hasseily/appletini-one/docs/FABRIC_TIMING_MARGIN_PLAN.md

# Fabric Timing Margin Plan

## Goal

Raise intrinsic fabric timing margin at 133.333 MHz. A timing candidate may
become the incremental reference only after it meets all of these gates:

- Two clean, full, non-incremental builds of the same Git commit pass in a row.
- Each build has setup WNS of at least `+0.300 ns` and setup TNS of `0`.
- Each build has nonnegative hold WNS and hold TNS of `0`.
- Each build has nonnegative pulse-width slack and no failing endpoints.
- Each build has no unconstrained internal endpoint, route error, bus-skew
  error, or XDC query that matched no object.
- The exact firmware made from the first passing checkpoint passes the full
  hardware test list.
- The checkpoint, bitstream, XSA, firmware, reports, commit, and tool version
  have saved hashes or IDs.

The `+0.300 ns` setup target gives useful build margin. Two runs with Vivado's
default seed show repeatability on one tool version and host. They do not prove
that all seeds or later Vivado releases will pass. Record both facts and rerun
the gate after a tool change.

## Confirmed Starting Point

The prior `+0.012 ns` result came from a full build. It did not use the known
good checkpoint. Its final timing was:

| Check | Result |
| --- | ---: |
| Setup WNS | `+0.012 ns` |
| Setup TNS | `0.000 ns` |
| Hold WNS | `+0.048 ns` |
| Hold TNS | `0.000 ns` |
| Pulse-width WNS | `+0.265 ns` |

The worst setup path starts at `ab_read_r.addr[11]` and ends in the Apple cycle
capture FIFO RAM. It has about `6.685 ns` of data delay, ten logic levels, and
about 79 percent route delay. The next two paths end at a Disk II
`drive_bit_offset` clock enable and have 15 logic levels. A fix to the capture
path can expose Disk II as the next limit, so each change needs a new top-path
review.

The prior resource report showed 10,223 slices, 30,465 LUTs, 20,153 registers,
74 block RAM tiles, and 1,001 control sets. Vivado reported a minimum of 994
control sets. This leaves little gain from a broad control-set rewrite unless a
later report shows a worse result.

Current synthesis maps both 4,096 by 16-bit SSI263 F2 copies and the 2,048 by
8-bit SmartPort C8 ROM into LUTs. The earlier assumption that the C8 ROM used
block RAM was wrong. The bus write arbiter has 12 clients; vTW is client 11.
Most clients already register their requests.

## Build Records and Promotion

Each build gets an immutable directory under:

```text
.timing_runs/<UTC>-<commit>-<full-or-incremental>/
```

The directory contains a manifest, the final checkpoint, bitstream, XSA, and
reports. `.timing_runs/builds.csv` stores one row per attempt.
`.timing_runs/paths.csv` stores the top ten setup paths, including full start
and end names, cell types, clocks, delay split, route share, logic levels, and
fanout. Failed attempts also get a manifest and CSV row.

The manifest records:

- Git commit and dirty state.
- Vivado version, device, speed grade, build mode, and reference checkpoint.
- Synthesis and implementation strategies and key directives.
- Timing, failing endpoints, route status, bus skew, and constraint warnings.
- Slice, LUT, register, block RAM, DSP, and control-set use.
- SHA-256 hashes for the checkpoint, bitstream, and XSA.

The build script keeps a named checkpoint and XSA in each build directory for
test firmware. It does not replace the known-good checkpoint. Promotion takes
two named build IDs. It checks that they are the two latest consecutive full
builds of one clean commit and that both pass every timing gate. It also checks
an immutable hardware record tied to the first checkpoint and tested firmware.

## Phase 0: Measure the Design

Status: complete for the initial baseline.

1. Add immutable build manifests, `builds.csv`, and `paths.csv` to the normal
   build script.
2. Record setup, hold, pulse width, failing endpoints, route and bus-skew
   status, missing XDC objects, resources, control sets, strategies, tool
   version, and hashes.
3. Add an optional diagnostic set:
   `report_design_analysis -congestion`, `report_high_fanout_nets`, and
   `report_qor_suggestions`. Always write timing, use, control-set, route,
   bus-skew, clock, method, and constraint reports.
4. Add a promotion script that enforces the two-build and hardware gates.
5. Add direct simulator tests at the Apple renderer and SDD capture FIFO
   boundaries before changing their timing.
6. Run a clean full build with diagnostics. Treat its reports as the campaign
   baseline and rank path classes by delay, route share, fanout, and count.

Run the baseline from a clean commit:

```powershell
$env:APPLETINI_FULL_BUILD = "1"
$env:APPLETINI_TIMING_DIAGNOSTICS = "1"
vivado -mode batch -source scripts/build_and_export_xsa.tcl
Remove-Item Env:APPLETINI_FULL_BUILD
Remove-Item Env:APPLETINI_TIMING_DIAGNOSTICS
```

Do not compare WNS alone. Compare the top path class, setup path count, hold,
route share, LUT levels, use, and control sets.

### Phase 0 Baseline Result

The clean full build `20260812T153728Z-7342c1a5-full` used commit
`7342c1a51dd9b1e8b29220e276b0094d885b3038` and Vivado 2025.2. It used no
incremental reference and no rescue pass. It produced:

| Check | Result |
| --- | ---: |
| Setup WNS / TNS | `+0.012 ns` / `0.000 ns` |
| Hold WNS / TNS | `+0.048 ns` / `0.000 ns` |
| Pulse-width WNS / TNS | `+0.265 ns` / `0.000 ns` |
| Worst bus-skew slack | `+5.496 ns` |
| Route errors | `0` |
| Unconstrained internal endpoints | `0` |
| Missing XDC objects | `0` |

The final design used 10,226 slices, 30,465 LUTs, 20,153 registers, 74 block
RAM tiles, six DSPs, and 1,001 control sets. The routed design had no congestion
window above Vivado level 5. Vivado gave no QoR suggestion because timing met.
This makes broad floorplanning and control-set work lower priority than the
measured path classes.

The top ten setup paths were:

| Rank | End block | Slack | Route share | Levels | Max fanout |
| ---: | --- | ---: | ---: | ---: | ---: |
| 1 | Apple capture FIFO RAM | `+0.012 ns` | 78.6% | 10 | 48 |
| 2-3 | Disk II `drive_bit_offset` enable | `+0.015 ns` | 72.8% | 15 | 81 |
| 4-5 | Apple capture FIFO RAM | `+0.050` to `+0.073 ns` | about 78% | 10 | 48-54 |
| 6 | Apple bus direction output | `+0.079 ns` | 44.7% | 5 | 11 |
| 7-9 | Apple cycle egress space logic | `+0.079 ns` | 57.9% | 13 | 8 |
| 10 | Disk II `drive_phase` enable | `+0.108 ns` | 74.0% | 14 | 81 |

The first five and tenth paths start at `ab_read_r.addr[11]`. The capture path
passes through slot-7 overlay qualification, pending-record selection, and the
FIFO input before it reaches block RAM. The Disk II path passes through slot-7,
boot-menu, vTW Disk II, and drive-state logic. The capture register stage should
remove three top-ten paths, but Disk II will then set WNS near `+0.015 ns` unless
placement changes. Review the Disk II path before assuming bus-snapshot copies
alone can add the remaining margin.

## Phase 1: Remove Route-Heavy Capture Paths

### 1. Register Capture Records

Add one record-assembly stage before each FIFO write path:

- Apple cycle renderer capture.
- SDD capture.

Register the complete source record and a valid bit at the capture event. Feed
the current collision, pending-event, loss, gap, storm, and jam rules from that
stage. Do not delay only `wr_en`; data and all event state must move together.

The tests must prove:

- Normal Apple writes keep address, data, and flags together.
- Frame events keep their order against Apple writes.
- I/O events that arrive first stay first.
- Pending collisions keep both events without duplication.
- A full FIFO sets the same sticky drop and overlay-loss state.
- Acknowledge and a new drop in one clock use set-wins behavior.
- C029, SHR mode, reset, and overlay flags stay on the same record.
- SDD records keep all address, data, and state bits.
- Storm and jam records keep the last intended record and count.
- Disable and reset clear the same state as before.

One extra 133 MHz cycle is about 7.5 ns. CPU1 drains these queues much later,
so this latency should not affect visible behavior. The full regression and
hardware tests still decide acceptance.

After this change, run a full build. Accept it only if the old capture path
class leaves the top paths and all counts remain exact. If Disk II becomes the
new limit, record that result before the next edit.

#### First Capture-Pipeline Build

Commit `e26205d08f3a2fdfcb7bc00d295d669a3f09c537` added the one-cycle
record stage to both capture FIFOs. The direct simulations proved consecutive
records, I/O-before-Apple order, pending-record handling, full-FIFO loss,
set-over-ack behavior, reset, SDD storm and jam trigger records, and exact
record data. The VidHD/SHR, Apple egress, SDD stream, and linear-overlay tests
also passed.

The clean full build `20260812T160459Z-e26205d0-full` produced:

| Check | Result |
| --- | ---: |
| Setup WNS / TNS | `+0.006 ns` / `0.000 ns` |
| Hold WNS / TNS | `+0.037 ns` / `0.000 ns` |
| Pulse-width WNS / TNS | `+0.265 ns` / `0.000 ns` |
| Worst bus-skew slack | `+5.904 ns` |
| Route errors | `0` |
| Unconstrained internal endpoints | `0` |
| Missing XDC objects | `0` |

No capture FIFO endpoint remained in the top ten. The change removed the
target path class, but it did not raise total margin. The new leading paths
were:

| Rank | End block | Slack | Route share | Levels |
| ---: | --- | ---: | ---: | ---: |
| 1 | vTW 65C02 `a_q[1]` to `p_q[1]` | `+0.006 ns` | 62.0% | 13 |
| 2 | Apple DMA `line_idx_q[2]` to PSRAM write data | `+0.037 ns` | 72.0% | 9 |
| 3-4 | Disk II `drive_phase` | `+0.044` to `+0.050 ns` | 77-79% | 11-12 |
| 5 | vTW Apple-bus direction output | `+0.057 ns` | 48.2% | 3 |
| 6-7, 9 | SmartPort output FIFO address | `+0.063` to `+0.101 ns` | about 76% | 12 |

The build used 10,072 slices, 30,541 LUTs, 20,282 registers, 74 block RAM
tiles, and 1,008 control sets. Against the baseline, slices fell by 154 while
LUTs rose by 76, registers rose by 129, and control sets rose by seven. The
build used the normal post-route `Explore` pass and no extra rescue pass.

Keep the capture stage because it removes the measured long decode-to-BRAM
path and its tests pass. Do not promote this build. Trace the new 65C02,
DMA/PSRAM, Disk II, and SmartPort paths before the next edit. A local vTW
Disk II enable register is a better first cut for the measured 11- to 12-level
Disk II cone than a broad fanout setting. Bus snapshot copies may still help
the SmartPort paths and the remaining common route delay, but fresh reports
must show the useful copy points.

#### vTW Disk II Gate Build

Commit `4a61407ff25d3e649a967ff854959f9f28383880` registered only the
boot-menu Disk II gate used by vTW. It kept the native handoff gate live. All
14 vTW benches, 19 standard Disk II tests, and 66 WOZ tests passed. The clean
full build `20260812T163431Z-4a61407f-full` produced:

| Check | Result |
| --- | ---: |
| Setup WNS / TNS | `+0.004 ns` / `0.000 ns` |
| Hold WNS / TNS | `+0.057 ns` / `0.000 ns` |
| Pulse-width WNS / TNS | `+0.265 ns` / `0.000 ns` |
| Worst bus-skew slack | `+5.366 ns` |
| Route errors | `0` |
| Missing XDC objects | `0` |

The long address-to-vTW Disk II path left the top ten. Local Disk II paths
now start at registered drive state and have at least `+0.100 ns` slack. Four
of the top ten paths start at `ab_read_r.addr[13]` and end in SmartPort or
Disk II; they have 46 to 74 loads and about 74 to 77 percent route delay. The
worst path is a Mockingboard response to the Apple data-direction pin at
`+0.004 ns`.

The design used 10,077 slices, 30,598 LUTs, 20,305 registers, 74 block RAM
tiles, and 1,053 control sets. Keep the local Disk II gate stage, but do not
promote this build. Test a synthesis `MAX_FANOUT` of 32 on the sampled 16-bit
Apple address register as one flow change. Do not apply it to the whole bus or
to the local capture record stage.

#### Apple Address `MAX_FANOUT` Build

Commit `3802754e1313f12d0a34a9e875a405ce103e2a02` set `MAX_FANOUT` to
32 on the 16 sampled Apple address registers. A post-synthesis cell check found
155 address-register cells instead of 16, so synthesis made 139 copies. It made
the most copies for the low address bits and only two cells for each of bits
11 through 15.

The clean full build `20260812T165450Z-3802754e-full` produced:

| Check | Result |
| --- | ---: |
| Setup WNS / TNS | `+0.004 ns` / `0.000 ns` |
| Hold WNS / TNS | `+0.014 ns` / `0.000 ns` |
| Pulse-width WNS / TNS | `+0.265 ns` / `0.000 ns` |
| Worst bus-skew slack | `+5.657 ns` |
| Route errors | `0` |
| Missing XDC objects | `0` |

Setup WNS did not change from the prior full build, while hold WNS fell from
`+0.057 ns` to `+0.014 ns`. The worst path still started at live
`ab_read_r.addr[11]` and ended in Disk II. Other address-to-Disk II and
address-to-SmartPort paths remained in the top ten. The build used 9,787
slices, 30,577 LUTs, 20,319 registers, 74 block RAM tiles, and 1,041 control
sets.

The broad limit did not make useful per-card groups and did not raise margin.
Commit `f75dc4d` removed it. Do not use a broad `MAX_FANOUT` rule on these
registers. If a later path calls for copies, make explicit same-cycle source
copies for named consumer groups, preserve the Apple bus sample edge, and
measure that change on its own.

#### Physical Response Stage Build

Commit `fbddd81997ee8c0c537ce64c6929aa006f886051` registered the
physical data-response tuple after the 12-client arbiter. Data, normal data
enable, address ownership, R/W, and the INH dependency move together. Address,
R/W, control-line requests, and the early DMA-window control remain live. The
staged byte also feeds the DMA window because both DMA clients hold it well
before that window opens.

The stage keeps the raw PHI0 release at the placed output LUT. It also stores
the INH dependency with an II+ saved read, so closing the machine-mode
interlock releases both INH and the live or held byte. The focused tests proved
late and back-to-back card responses, native and vTW-owned reads and writes,
II+ saved-byte hold, live and saved INH cutoff, reset masking, and the existing
AD8088 DMA window. The AD8088 bench still measured `158.8` to `323.8 ns`, with
zero ghost writes.

The clean full build `20260813T045644Z-fbddd819-full` produced:

| Check | Result |
| --- | ---: |
| Setup WNS / TNS | `+0.003 ns` / `0.000 ns` |
| Hold WNS / TNS | `+0.045 ns` / `0.000 ns` |
| Pulse-width WNS / TNS | `+0.265 ns` / `0.000 ns` |
| Worst bus-skew slack | `+5.376 ns` |
| Route errors | `0` |
| Missing XDC objects | `0` |

The card-to-data-direction path left the top paths. Against the prior accepted
netlist, slices fell from 10,077 to 9,752, LUTs fell from 30,598 to 30,558,
and control sets fell from 1,053 to 1,008. Registers rose from 20,305 to
20,314. Keep the stage for the removed output path and lower use, but do not
promote this build. Setup margin stayed flat because Disk II replaced the
removed path:

| Rank | Path class | Slack | Route share | Levels |
| ---: | --- | ---: | ---: | ---: |
| 1-4 | Apple address to Disk II bit-offset enable | `+0.003 ns` | 79.8% | 10 |
| 5 | PS to Disk II underrun count | `+0.010 ns` | 77.5% | 5 |
| 6-9 | Disk II spin count to latch enable | `+0.014 ns` | 75.3% | 13 |
| 10 | Disk II spin count to step-delay enable | `+0.034 ns` | 77.2% | 12 |

Trace and cut these two Disk II enable classes before adding bus snapshot
copies. The new report does not support a broad address-copy change.

#### Disk II vTW Rotation Stage Build

Commit `03de4daec1d2d03a1c566bdffe669365ec97d0f1` registered the
Disk II rotation state only at the boundary into vTW speed control. Local Q7,
cache-miss, media-ready, and sequencer logic remain live. Motor and drive
changes come through physical Disk II cycles, so the new view settles well
before vTW can start another private cycle.

All 14 vTW benches, 19 standard Disk II tests, and 66 WOZ tests passed. The
boot-menu source checks passed 19 of 20 tests; the one failed source-order guard
is unrelated to this RTL change and existed before it.

The clean full build `20260813T052716Z-03de4dae-full` produced:

| Check | Result |
| --- | ---: |
| Setup WNS / TNS | `+0.093 ns` / `0.000 ns` |
| Hold WNS / TNS | `+0.047 ns` / `0.000 ns` |
| Pulse-width WNS / TNS | `+0.265 ns` / `0.000 ns` |
| Worst bus-skew slack | `+5.921 ns` |
| Route errors | `0` |
| Missing XDC objects | `0` |
| Rescue used | `0` |

The spin-count-to-vTW-to-Disk II feedback paths left the top ten. The prior
Apple-address-to-Disk II paths also stayed out of the top ten in this placement.
The build used 9,916 slices, 30,540 LUTs, 20,285 registers, 74 block RAM tiles,
and 1,007 control sets. Against the response-stage build, LUTs fell by 18,
registers fell by 29, control sets fell by one, and slices rose by 164.

The new top paths are:

| Rank | Path class | Slack | Route share | Levels |
| ---: | --- | ---: | ---: | ---: |
| 1 | Raw PHI0 input to data-direction output | `+0.093 ns` | 39.7% | 3 |
| 2-4 | vTW cycle address to record enable | `+0.112 ns` | 71.9% | 10 |
| 5 | vTW cycle address to record enable | `+0.135 ns` | 72.0% | 10 |
| 6-10 | Slot mapping to Disk II dirty-track enable | `+0.163 ns` | 76.9% | 11 |

Keep the rotation stage, but do not promote this build. The setup gain is
`0.090 ns`, and the target remains `+0.300 ns`. Review the fixed PHI0 release
route, then cut the vTW record-control and Disk II mapping cones. Do not add a
broad fanout rule: none of these paths starts at a high-load source.

#### Data-Direction Pad Build

Commit `d9cb0beefc688798046bfe52a6ae8dba0b4e8016` kept the existing
12 mA drive on `a2fpga_dir_d` and changed only its output slew from slow to
fast. This keeps the raw-PHI0 truth table and clock count unchanged. A routed
checkpoint test predicted `+0.624 ns` on the eight-nanosecond pad-to-pad bound.
All 14 vTW benches passed before the full build.

The clean full build `20260813T055125Z-d9cb0bee-full` produced:

| Check | Result |
| --- | ---: |
| Setup WNS / TNS | `+0.036 ns` / `0.000 ns` |
| Hold WNS / TNS | `+0.066 ns` / `0.000 ns` |
| Pulse-width WNS / TNS | `+0.265 ns` / `0.000 ns` |
| Worst bus-skew slack | `+5.388 ns` |
| Route errors | `0` |
| Missing XDC objects | `0` |
| Rescue used | `0` |

The target path improved from `+0.093` to `+0.476 ns`, even though its route
delay rose from `3.136` to `3.284 ns`. The output-buffer delay fell by about
`0.53 ns`. Keep this constraint because the raw-PHI0 release path now clears
the campaign target without changing its logic. Hardware signoff must still
check the faster control edge for ringing.

Global WNS fell due to placement of a different path. The new top paths are:

| Rank | Path class | Slack | Route share | Levels |
| ---: | --- | ---: | ---: | ---: |
| 1-2, 4-5, 10 | Slot state to SmartPort output-FIFO address | `+0.036` to `+0.207 ns` | 74-76% | 12-13 |
| 3 | Disk II track length to data latch | `+0.161 ns` | 75.9% | 13 |
| 6-9 | vTW cycle address to RamWorks data enable | `+0.205 ns` | 69.1% | 10 |

The build used 10,013 slices, 30,542 LUTs, 20,267 registers, 74 block RAM
tiles, and 1,008 control sets. Do not promote it. Cut the SmartPort FIFO
address path next, then the measured vTW and Disk II paths.

#### SmartPort FIFO Address Build

Commit `12dc4977418f0cc3e4e35812c63ebf772b6a716e` removed the same-edge
post-pop lookahead from the SmartPort output FIFO. The block RAM now reads
from the registered pointer. The word catches up one fabric clock after a
pop, before either the native Apple bus or vTW can issue its next DATA read.
The test bench covers a five-byte word crossing through both paths. All 14
vTW benches, 16 SmartPort service tests, six ROM tests, and 15 menu tests
passed before the full build.

The clean full build `20260813T061638Z-12dc4977-full` produced:

| Check | Result |
| --- | ---: |
| Setup WNS / TNS | `+0.017 ns` / `0.000 ns` |
| Hold WNS / TNS | `+0.030 ns` / `0.000 ns` |
| Pulse-width WNS / TNS | `+0.265 ns` / `0.000 ns` |
| Worst bus-skew slack | `+5.915 ns` |
| Route errors | `0` |
| Missing XDC objects | `0` |
| Rescue used | `0` |

The target SmartPort block-RAM address path left the top ten. Keep the cut.
The lower global WNS comes from a different machine-mode-to-data-direction
route under the ten-nanosecond output bound. The new top paths are:

| Rank | Path class | Slack | Route share | Levels |
| ---: | --- | ---: | ---: | ---: |
| 1 | Machine mode to data-direction output | `+0.017 ns` | 55.5% | 3 |
| 2-5 | Disk II quarter-track to bit-offset enable | `+0.124 ns` | 75.3% | 13 |
| 6-7 | Apple address to Disk II WOZ shift enable | `+0.137 ns` | 77.9% | 11 |
| 8-10 | Disk II quarter-track to stream-position enable | `+0.159` to `+0.165 ns` | 75.2% | 13 |

The build used 9,909 slices, 30,567 LUTs, 20,289 registers, 74 block RAM
tiles, and 1,018 control sets. Do not promote it. First remove the live
machine-mode decode from the direction-output cone. Then cut the measured
Disk II rotation and native-event cones.

#### Bus Safety Interlock Copy Build

Commit `c647de77861ad7cadaf797d77da7be7e61db13ee` added a preserved,
same-edge copy of the machine INH safety flag for `apple_bus_wrapper`. The
copy keeps reset and machine-mode update behavior unchanged. All 14 vTW
benches passed before the full build.

The clean full build `20260813T063714Z-c647de77-full` used Vivado 2025.2,
no incremental reference, and no rescue pass. It produced:

| Check | Result |
| --- | ---: |
| Setup WNS / TNS | `+0.116 ns` / `0.000 ns` |
| Hold WNS / TNS | `+0.075 ns` / `0.000 ns` |
| Pulse-width WNS / TNS | `+0.265 ns` / `0.000 ns` |
| Worst bus-skew slack | `+5.928 ns` |
| Route errors | `0` |
| Missing XDC objects | `0` |
| Unconstrained internal endpoints | `0` |
| Rescue used | `0` |

The build used 9,826 slices, 30,541 LUTs, 20,296 registers, 74 block RAM
tiles, six DSPs, and 1,009 control sets. The new top paths are:

| Rank | Path class | Slack | Route share | Levels |
| ---: | --- | ---: | ---: | ---: |
| 1-7 | vTW CPU state to private RamWorks-bank enable | `+0.116 ns` | 80.8% | 7 |
| 8 | vTW cycle address to card-control read data | `+0.140 ns` | 68.8% | 14 |
| 9 | Apple address to SmartPort input count | `+0.155 ns` | 67.6% | 14 |
| 10 | Disk II quarter-track to bit-offset enable | `+0.159 ns` | 74.4% | 13 |

The first path class starts at a CPU state bit with fanout 93 and ends at all
seven `ss_ramworks_bank` clock enables. Cut this measured class next by using
a private soft-switch apply pulse after the captured vTW cycle tuple is ready.

The copy improved placement, but it did not remove every old
machine-mode-to-data-direction route. The new local-copy path to `DIR_D` has
`+0.445 ns` slack, while the original machine-mode path through the write
arbiter remains at `+0.359 ns`. Neither path limits this build. Keep the copy,
but do not claim that it removed the old route. Do not promote this build;
setup margin remains below `+0.300 ns`.

#### vTW Soft-Switch Apply Build

Commit `bceefabda0ba6449a5fa5a42009c41f13abba786` moved only the
private vTW soft-switch manager to a one-clock apply stage. `X_CAPTURE` saves
the core address, read/write state, write data, and pre-access switch state.
`X_ROUTE` applies that saved tuple to the private manager. The shared
`ssm_pulse` and the `$C074` speed latch remain at `X_CAPTURE`.

The full-system test now checks both `$C071` and `$C073`: the RamWorks bank
stays old at `X_CAPTURE`, changes at `X_ROUTE`, and appears in the next access
snapshot. Its existing checks also kept `$C006/$C007`, the C3/CFFF claim and
release, double `$C083`, video switches, and `$C074` behavior intact. All 14
vTW benches passed. The RamWorks 8 MB contract test, capture-FIFO, cycle-egress,
SDD stream, linear-overlay, and VidHD/SHR regressions also passed.

The clean full build `20260813T071806Z-bceefabd-full` used Vivado 2025.2,
no incremental reference, and no rescue pass. It produced:

| Check | Result |
| --- | ---: |
| Setup WNS / TNS | `+0.009 ns` / `0.000 ns` |
| Hold WNS / TNS | `+0.041 ns` / `0.000 ns` |
| Pulse-width WNS / TNS | `+0.265 ns` / `0.000 ns` |
| Worst bus-skew slack | `+5.911 ns` |
| Route errors | `0` |
| Missing XDC objects | `0` |
| Unconstrained internal endpoints | `0` |
| Rescue used | `0` |

The build used 9,855 slices, 30,501 LUTs, 20,263 registers, 74 block RAM
tiles, six DSPs, and 1,008 control sets. Against the bus-safety-copy build,
slices rose by 29, LUTs fell by 40, registers fell by 33, and control sets
fell by one.

The CPU-state-to-`ss_ramworks_bank` enable paths left the top ten, so keep
this structural cut. Global WNS fell by `0.107 ns` because Disk II and live
Apple-address paths took over:

| Rank | Path class | Slack | Route share | Levels |
| ---: | --- | ---: | ---: | ---: |
| 1, 7-10 | Disk II quarter-track to WOZ-shift enable | `+0.009`, then `+0.075 ns` | 76.1-76.2% | 12 |
| 2 | Apple address to Disk II bit-offset data | `+0.017 ns` | 76.7% | 12 |
| 3, 5 | Disk II quarter-track to data-latch enable | `+0.038`, `+0.069 ns` | 76.3-76.5% | 12 |
| 4 | Apple address to SmartPort input-FIFO write enable | `+0.066 ns` | 74.9% | 12 |
| 6 | vTW cycle address to posted-write memory input | `+0.074 ns` | 76.4% | 10 |

Do not promote this build. It passes the nonnegative export gates but remains
well below `+0.300 ns`. Trace the Disk II quarter-track enable cone and the
live Apple-address consumer cone before choosing the next cut. Do not infer a
new change from WNS alone; both classes are route-heavy and need path-level
control-flow review.

#### vTW Disk II Time-Tick Stage Build

Commit `bd99547fb82abcf90b5c4adbf7928926b536be46` stages only the
accepted normal vTW Disk II time tick by one 133.333 MHz fabric clock. The
stage clears when the core session ends. Private Disk II reads keep their
registered direct-access tick, while native and Q7 cycles keep the physical
1 MHz tick path.

All 14 vTW benches passed. The focused checks prove exact accepted and output
pulse counts across a readiness stall, let an accepted tick drain after a
later stall, clear a pending tick on session reset, and keep private, native,
and Q7 tick selection separate. All 19 standard Disk II tests, 66 WOZ tests,
the capture-FIFO and cycle-egress tests, nine SDD tests, the linear-overlay
source and RTL tests, and 17 VidHD/SHR tests also passed.

The clean full diagnostic run `20260813T082040Z-bd99547f-full` used Vivado
2025.2, the default seed, and no incremental reference. Its normal
post-route `Explore` result had `-0.030 ns` setup WNS. The extra
`AggressiveExplore` rescue pass did not improve it, so `rescue_used=1`. The
run failed its setup gate and exported no candidate DCP, bitstream, or XSA.

| Check | Result |
| --- | ---: |
| Build status | `failed` |
| Setup WNS / TNS | `-0.030 ns` / `-0.030 ns` |
| Setup failing endpoints | `1` |
| Hold WNS / TNS | `+0.039 ns` / `0.000 ns` |
| Pulse-width WNS / TNS | `+0.265 ns` / `0.000 ns` |
| Worst bus-skew slack | `+5.994 ns` |
| Route errors | `0` |
| Missing XDC objects | `0` |
| Unconstrained internal endpoints | `0` |
| Rescue used | `1` |
| Hardware export | refused |

The run used 9,725 slices, 30,398 LUTs, 20,289 registers, 74 block RAM
tiles, six DSPs, and 1,008 control sets. Against the soft-switch apply build,
slices fell by 130, LUTs fell by 103, registers rose by 26, and control sets
stayed unchanged. Setup WNS fell by `0.039 ns`, hold WNS fell by `0.002 ns`,
and bus-skew slack rose by `0.083 ns`.

The old Disk II quarter-track/readiness/normal-tick paths to the WOZ shift and
data-latch enables left the top ten. The existing vTW posted-write class took
over instead:

| Rank | Path class | Slack | Route share | Levels |
| ---: | --- | ---: | ---: | ---: |
| 1, 5-7, 9 | vTW cycle address to posted-write BRAM enable/data | `-0.030`, then `+0.059` to `+0.123 ns` | 76.3-76.6% | 10 |
| 2 | vTW write-direction state to address-direction output | `+0.003 ns` | 48.4% | 2 |
| 3 | Machine-INH safety copy to data-direction output | `+0.004 ns` | 53.5% | 3 |
| 4, 8 | vTW cycle address to posted-fill state | `+0.040`, `+0.119 ns` | 66.7-67.4% | 13 |
| 10 | Disk II request address to recalibration-sound arm state | `+0.133 ns` | 80.2% | 8 |

Keep the time-tick stage because it cut the measured same-cycle feedback and
passed its functional checks. Do not claim that it removed every Disk II
quarter-track consumer. Do not promote this run: it has one failing setup
endpoint, used the rescue pass, and produced no hardware outputs. Trace the
cycle-address-to-posted-write BRAM enable cone before choosing another cut.

#### vTW Posted-Write Tuple Stage Build

Commit `72903dd21744a04e6f493c650492b66c3b66c4c3` adds one registered
address/data/valid tuple between final core-or-ARM acceptance and the vTW bus
engine's posted queue. The core keeps priority on an exact collision. The
stage can drain and refill on the same edge, so it keeps one write per fabric
clock. It adds one 133.333 MHz clock, about 7.5 ns, before queue entry. Reset,
disable, or Apple `RES#` cancels the pending tuple at the same transaction
boundary that clears the queue.

All 14 vTW benches passed. Away from a queue-clear boundary, the full-system
test now proves that each accepted core or ARM tuple reaches the engine on the
next edge with the same address and data. It also checks a sustained
eight-write ARM burst, exact core-over-ARM collision order, overlay-write order
before slot-7 `DEVSEL`, and reset cancellation of an accepted tuple. The
capture-FIFO, cycle-egress, nine SDD, linear-overlay source and RTL, 17
VidHD/SHR, and 16 SmartPort service tests also passed.

The clean full build `20260813T090405Z-72903dd2-full` used Vivado 2025.2, the
default seed, no incremental reference, and no rescue pass. It exported the
candidate DCP, bitstream, and XSA.

| Check | Result |
| --- | ---: |
| Build status | `exported` |
| Setup WNS / TNS | `+0.121 ns` / `0.000 ns` |
| Setup failing endpoints | `0` |
| Hold WNS / TNS | `+0.058 ns` / `0.000 ns` |
| Pulse-width WNS / TNS | `+0.265 ns` / `0.000 ns` |
| Worst bus-skew slack | `+5.816 ns` |
| Route errors | `0` |
| Missing XDC objects | `0` |
| Unconstrained internal endpoints | `0` |
| Rescue used | `0` |

The build used 10,014 slices, 30,533 LUTs, 20,273 registers, 74 block RAM
tiles, six DSPs, and 1,009 control sets. Against the Disk II time-tick run,
slices rose by 289, LUTs rose by 135, registers fell by 16, and control sets
rose by one. Setup WNS rose by `0.151 ns`, hold WNS rose by `0.019 ns`, and
bus-skew slack fell by `0.178 ns`.

The prior vTW posted-memory and posted-fill paths left the saved top ten, so
keep this cut. Live Apple-address consumers took over:

| Rank | Path class | Slack | Route share | Levels |
| ---: | --- | ---: | ---: | ---: |
| 1 | Apple address to Disk II recalibration-sound arm state | `+0.121 ns` | 73.6% | 12 |
| 2, 3, 5 | Apple address to SmartPort input-FIFO write enable | `+0.206` to `+0.255 ns` | 73.0-73.2% | 13 |
| 4, 10 | Apple address to Disk II bit-offset enable | `+0.222`, `+0.283 ns` | 75.5-75.7% | 12 |
| 6, 8 | PS AXI interface to egress and Ethernet config state | `+0.259`, `+0.278 ns` | 83.7-83.9% | 0 |
| 7 | Apple reset snapshot to control read data | `+0.264 ns` | 76.5% | 10 |
| 9 | Slot-enable mask to no-slot-clock reset | `+0.280 ns` | 80.5% | 7 |

Do not promote or package this build. Setup margin is still `0.179 ns` below
the `+0.300 ns` gate. For the next measured cut, split the native Disk II raw
read-response path from its controller side effects, then register the native
`$C0Ex` read/write pulse and low address for the stepper and bit-offset
updates. Capture write data at its current data phase. Keep the same-cycle
Apple read response and private vTW request order intact. This targets ranks
1, 4, and 10; remeasure before changing the SmartPort path.

#### Disk II Handoff Gate Build

Commit `e360dec24b71b16c96f2c3ffbb1f21e51d9cba4a` puts normal native
Disk II I/O, the physical timing strobe, and vTW activation behind the existing
one-fabric-clock registered handoff view. The first `$C600` handoff read keeps
a live one-clock bypass that ends in the slot-ROM response. The slot-6 enable
remains a live term in both gates. This avoids the unsafe plan to delay Disk II
controller side effects while keeping the first handoff ROM byte on its old
response schedule.

All 18 vTW benches passed, including the native physical-bus, native/vTW WOZ
read/write, all-speed vTW, and full vTW-to-WOZ tests. A directed RTL check
proves that the live bypass serves `$C600` but cannot turn `$C0EC` into a
controller event. All 21 boot-menu/reset, 19 standard Disk II, 66 WOZ, 16
SmartPort service, six SmartPort ROM, nine SDD, 17 VidHD/SHR, 12 Phasor,
Uthernet, SSC, cycle-egress, capture-FIFO, and linear-overlay checks also
passed. Hardware tests remain deferred.

The clean full build `20260813T112209Z-e360dec2-full` used Vivado 2025.2, the
default seed, no incremental reference, and no rescue pass. It exported the
candidate DCP, bitstream, and XSA.

| Check | Result |
| --- | ---: |
| Build status | `exported` |
| Setup WNS / TNS | `+0.053 ns` / `0.000 ns` |
| Setup failing endpoints | `0` |
| Hold WNS / TNS | `+0.049 ns` / `0.000 ns` |
| Pulse-width WNS / TNS | `+0.265 ns` / `0.000 ns` |
| Worst bus-skew slack | `+5.980 ns` |
| Route errors | `0` |
| Missing XDC objects | `0` |
| Unconstrained internal endpoints | `0` |
| Rescue used | `0` |

The build used 9,899 slices, 30,661 LUTs, 20,374 registers, 74 block RAM
tiles, six DSPs, and 1,025 control sets. Against the posted-write build, slices
fell by 115, LUTs rose by 128, registers rose by 101, and control sets rose by
16. Setup WNS fell by `0.068 ns`, hold WNS fell by `0.009 ns`, and bus-skew
slack rose by `0.164 ns`.

The old handoff-qualified Disk II paths left the saved top ten. A targeted
checkpoint query still finds Apple-address paths into the named Disk II
bit-offset and recalibration endpoint group, but their worst slack is now
`+0.362 ns` with seven logic levels instead of the prior `+0.121 ns` with 12
levels. The worst Apple-address path into the SmartPort input-FIFO BRAM write
enable is `+0.328 ns`; it also left the saved top ten but was not removed.

| Rank | Path class | Slack | Route share | Levels |
| ---: | --- | ---: | ---: | ---: |
| 1 | vTW write-direction state to the address-direction pad | `+0.053 ns` | 48.8% | 2 |
| 2, 8, 10 | Slot-C3-ROM state to SmartPort input count | `+0.092` to `+0.171 ns` | 64.3-65.0% | 16 |
| 3-6 | PS AXI interface to boot-menu key-FIFO enable | `+0.113 ns` | 73.9% | 6 |
| 7 | SSI263 formant accumulator to filter history | `+0.144 ns` | 44.6% | 20 |
| 9 | PS AXI interface to Phasor audio output | `+0.170 ns` | 84.2% | 0 |

Keep the handoff cut, but do not promote or package this build. Its setup
margin is still `0.247 ns` below the `+0.300 ns` gate, and no hardware check
has run. Trace the address-direction pad path and the slot-C3-ROM-to-SmartPort
count cone before choosing the next measured cut. Do not spend the next commit
on the old SmartPort BRAM-write path alone; its measured residual is already
above the promotion gate.

#### Address-Direction Fast-Edge Build

Commit `78b839a65f7893f9d0a0d51806f051da582c339e` kept the existing 12 mA
drive on `a2fpga_dir_a` and changed only its output slew from slow to fast.
The 18 vTW benches and the Appli-Card/AD8088 source checks passed. A query on
the prior routed checkpoint predicted that the output-buffer delay would fall
by `0.531 ns`, moving the target path from `+0.053 ns` to `+0.584 ns` without
changing logic or clock count.

The clean full build `20260813T114539Z-78b839a6-full` used Vivado 2025.2,
the default seed, no incremental reference, and no rescue pass. It exported
the candidate DCP, bitstream, and XSA.

| Check | Result |
| --- | ---: |
| Build status | `exported` |
| Setup WNS / TNS | `+0.015 ns` / `0.000 ns` |
| Setup failing endpoints | `0` |
| Hold WNS / TNS | `+0.044 ns` / `0.000 ns` |
| Pulse-width WNS / TNS | `+0.265 ns` / `0.000 ns` |
| Worst bus-skew slack | `+5.748 ns` |
| Route errors | `0` |
| Missing XDC objects | `0` |
| Unconstrained internal endpoints | `0` |
| Rescue used | `0` |

The build used 10,038 slices, 30,646 LUTs, 20,315 registers, 74 block RAM
tiles, six DSPs, and 1,007 control sets. Against the handoff-gate build,
slices rose by 139, LUTs fell by 15, registers fell by 59, and control sets
fell by 18. Setup WNS fell by `0.038 ns`, hold WNS fell by `0.005 ns`, and
bus-skew slack fell by `0.232 ns`.

The fast pad did reduce logic and output-buffer delay from `3.799 ns` to
`3.214 ns`. The route delay rose from `3.625 ns` to `4.244 ns`, however, so
the same address-direction endpoint remained worst and fell from `+0.053 ns`
to `+0.015 ns`. The target did not improve in a clean implementation.

| Rank | Path class | Slack | Route share | Levels |
| ---: | --- | ---: | ---: | ---: |
| 1 | vTW write-direction state to the address-direction pad | `+0.015 ns` | 56.9% | 2 |
| 2, 4, 8 | Apple address to SmartPort input-FIFO write enable | `+0.110` to `+0.159 ns` | 72.2-72.4% | 13 |
| 3 | Apple address to SmartPort input count | `+0.112 ns` | 63.3% | 16 |
| 5-7 | Disk II WOZ accumulator to data-latch enable | `+0.148 ns` | 60.2% | 10 |
| 9 | Apple address to SmartPort output count | `+0.163 ns` | 62.8% | 16 |
| 10 | vTW cycle address to aux-shadow BRAM address | `+0.169 ns` | 82.8% | 7 |

Reject and revert the DIR_A fast-edge trial. It did not improve the measured
target or global WNS, and its faster electrical edge cannot be checked without
hardware. Keep DIR_D fast because its own measured target cleared the campaign
gate; restore DIR_A to slow before the next structural build. Then register
the vTW SmartPort request target at the existing route-to-issue boundary so the
live handoff and Apple-address decode cannot reach the FIFO write/count cones.

#### vTW SmartPort Target Stage Build

Commit `81888341018f6a903d0141ba7934e1a0ffc4a1aa` captures the final
three-bit SmartPort request target when `X_ROUTE` accepts a SmartPort access.
`X_SP_ISSUE` already starts on the following fabric edge, so the register adds
no state or request cycle. The 18 vTW benches passed, including the Disk II
physical-bus, WOZ read/write, all-speed, and end-to-end WOZ checks. The 16
SmartPort service checks, 21 boot-menu/reset checks, and nine SuperSprite
checks also passed. The system bench drops SmartPort ownership after route
capture and proves that request-valid and the captured target stay fixed.

The clean full build `20260813T120543Z-81888341-full` used Vivado 2025.2,
the default seed, no incremental reference, and no rescue pass. It exported
the candidate DCP, bitstream, and XSA.

| Check | Result |
| --- | ---: |
| Build status | `exported` |
| Setup WNS / TNS | `+0.057 ns` / `0.000 ns` |
| Setup failing endpoints | `0` |
| Hold WNS / TNS | `+0.051 ns` / `0.000 ns` |
| Pulse-width WNS / TNS | `+0.265 ns` / `0.000 ns` |
| Worst bus-skew slack | `+5.885 ns` |
| Route errors | `0` |
| Missing XDC objects | `0` |
| Unconstrained internal endpoints | `0` |
| Rescue used | `0` |

The build used 9,915 slices, 30,561 LUTs, 20,236 registers, 74 block RAM
tiles, six DSPs, and 1,103 control sets. Against the kept Disk II handoff-gate
build, slices rose by 16, LUTs fell by 100, registers fell by 138, and control
sets rose by 78. Setup WNS rose by `0.004 ns`, hold WNS rose by `0.002 ns`,
and bus-skew slack fell by `0.095 ns`.

The prior vTW SmartPort target-to-FIFO class left the saved top ten. The exact
old slot-C3-ROM-to-input-count-bit-9 path improved from `+0.092 ns`, 16 logic
levels, and `7.315 ns` of data delay to `+1.132 ns`, 12 levels, and `6.305 ns`.
A targeted checkpoint query shows the new target-register paths at `+2.707 ns` to the
input-FIFO write enable, `+2.755 ns` to the input count, and `+3.634 ns` to
the output count. Live Apple-address, slot-C3-ROM, and boot-activation paths
still reach those endpoints through the native SmartPort slot-access route;
they were not removed. Their worst measured slacks are now `+0.844 ns`,
`+0.975 ns`, and `+1.356 ns`, respectively, across the three endpoint groups.

| Rank | Path class | Slack | Route share | Levels |
| ---: | --- | ---: | ---: | ---: |
| 1, 3, 4 | PS AXI interface to SmartPort input-FIFO read address | `+0.057` to `+0.153 ns` | 62.8-63.8% | 8-9 |
| 2 | PS AXI interface to AXI exclusive-access lock state | `+0.064 ns` | 54.1% | 14 |
| 5-8 | PS AXI interface to boot-menu C8-ROM write address | `+0.161 ns` | 83.5% | 0 |
| 9 | PS AXI interface to vTW slowdown state | `+0.165 ns` | 83.9% | 0 |
| 10 | vTW cycle address to RamWorks cache-data enable | `+0.169 ns` | 74.2% | 10 |

Keep the registered target, but do not promote or package this build. It is
still `0.243 ns` below the `+0.300 ns` setup gate, and no hardware check has
run. Trace the PS-AXI-to-SmartPort input-FIFO address cone next. Do not change
the new target stage based on global WNS alone; its measured residual has more
than `+2.7 ns` of slack.

#### SmartPort Input-FIFO Read-Address Build

Commit `b3bd14a4c63f61a573dd068a11bc93666add5084` reads the SmartPort input
FIFO from its registered read pointer instead of a combinational post-pop
pointer. Pop acceptance, pointer and count updates, clear priority, and AXI
completion stay on their old edge. The cached head word now refreshes one
fabric edge after a pop, matching the existing output-FIFO structure. A new
minimum-gap regression checks packed `POP_IN4` to `IN_HEAD4`, every scalar
byte lane, and the packed-word boundary. The 18 vTW benches, 16 SmartPort
service checks, six SmartPort ROM checks, 21 boot-menu/reset checks, and nine
SuperSprite checks passed.

The clean full build `20260813T123026Z-b3bd14a4-full` used Vivado 2025.2,
the default seed, no incremental reference, and no rescue pass. It exported
the candidate DCP, bitstream, and XSA.

| Check | Result |
| --- | ---: |
| Build status | `exported` |
| Setup WNS / TNS | `+0.105 ns` / `0.000 ns` |
| Setup failing endpoints | `0` |
| Hold WNS / TNS | `+0.039 ns` / `0.000 ns` |
| Pulse-width WNS / TNS | `+0.265 ns` / `0.000 ns` |
| Worst bus-skew slack | `+5.879 ns` |
| Route errors | `0` |
| Missing XDC objects | `0` |
| Unconstrained internal endpoints | `0` |
| Rescue used | `0` |

The build used 9,811 slices, 30,620 LUTs, 20,215 registers, 74 block RAM
tiles, six DSPs, and 1,009 control sets. Against the target-stage build,
slices fell by 104, LUTs rose by 59, registers fell by 21, and control sets
fell by 94. Setup WNS rose by `0.048 ns`, hold WNS fell by `0.012 ns`, and
bus-skew slack fell by `0.006 ns`.

The prior PS-write-decode-to-input-FIFO-address class left the saved top ten.
A targeted query of every path into the input-FIFO read-address pins finds a
worst residual of `+5.712 ns`, zero logic levels, and a local registered
startpoint. The prior exact class was `+0.057 ns` with nine logic levels. The
cut therefore removed the measured combinational pop/prefetch cone.

| Rank | Path class | Slack | Route share | Levels |
| ---: | --- | ---: | ---: | ---: |
| 1 | PS write data to Disk II PSRAM-base state | `+0.105 ns` | 84.1% | 0 |
| 2 | vTW shadow-host pointer to aux-shadow BRAM address | `+0.135 ns` | 94.8% | 0 |
| 3 | PS write data to Mouse-card X state | `+0.137 ns` | 84.0% | 0 |
| 4-7 | PS write data to boot-menu C8-ROM write address | `+0.169 ns` | 84.2% | 0 |
| 8-10 | PS write data to another boot-menu C8-ROM write bank | `+0.196 ns` | 84.2% | 0 |

Keep the registered read address, but do not promote or package this build. It
is still `0.195 ns` below the `+0.300 ns` setup gate, and no hardware check has
run. Trace the direct PS-write-data-to-Disk-II configuration path next. The
former AXI exclusive-monitor cone is no longer in the saved top ten, so do not
remove that protocol feature solely on the prior placement result.

#### AXI Write-Data Stage Build

Commit `8f2d80393efead02ebc74c31a7e6637e208061d2` places a registered
two-entry skid buffer on the PS GP0 write-data channel. It keeps `WDATA`,
`WSTRB`, and `WLAST` in one 37-bit tuple and leaves the independent address
channel in the existing AXI bridge. The stage adds one fabric clock before an
unstalled write beat reaches the bridge, keeps one-beat-per-clock throughput,
and does not issue a write response until the saved beat reaches its selected
client. The wrapper's existing contract still forbids AXI3 write-data
interleaving across write IDs because the design does not carry `WID`.

The focused wrapper regression passed address-before-data, data-before-address,
same-edge channels, two-entry backpressure, a 16-beat burst with distinct byte
strobes, client selection, response ordering and backpressure, and reset
cancellation. A second bench sent full, partial, adjacent, and reset-canceled
BASE writes through the real wrapper and Disk II card. It checked the exact
client edge, eight-byte alignment, cache and write-queue invalidation, ordered
responses, and response-before-readback ordering. The 18 vTW benches, 19
standard-Disk-II checks, 66 WOZ checks, 16 SmartPort checks, 21 boot-menu/reset
checks, and the Mouse, Appli-Card, Uthernet II, SSC, and Phasor suites passed.

The clean full build `20260813T132044Z-8f2d8039-full` used Vivado 2025.2,
the default seed, no incremental reference, and no rescue pass. It exported
the candidate DCP, bitstream, and XSA.

| Check | Result |
| --- | ---: |
| Build status | `exported` |
| Setup WNS / TNS | `+0.139 ns` / `0.000 ns` |
| Setup failing endpoints | `0` |
| Hold WNS / TNS | `+0.053 ns` / `0.000 ns` |
| Pulse-width WNS / TNS | `+0.265 ns` / `0.000 ns` |
| Worst bus-skew slack | `+5.908 ns` |
| Route errors | `0` |
| Missing XDC objects | `0` |
| Unconstrained internal endpoints | `0` |
| Rescue used | `0` |

The build used 10,082 slices, 30,593 LUTs, 20,303 registers, 74 block RAM
tiles, six DSPs, and 1,009 control sets. Against the SmartPort read-address
build, slices rose by 271, LUTs fell by 27, registers rose by 88, and control
sets did not change. Setup WNS rose by `0.034 ns`, hold WNS rose by `0.014 ns`,
and bus-skew slack rose by `0.029 ns`. No reported congestion window exceeded
level 5.

The raw PS `MAXIGP0WDATA` class left the saved top ten. It had occupied nine
of ten positions in the prior build, including the `+0.105 ns` Disk II BASE
path, the `+0.137 ns` Mouse path, and the `+0.169` to `+0.196 ns` boot-ROM
paths. The worst saved residual from the new write-data register is a
zero-level route to vTW ARM-address state at `+0.288 ns`; the cut therefore
placed a sequential boundary before the shared PS write-data loads, although
its route remains `0.012 ns` short of the campaign gate.

| Rank | Path class | Slack | Route share | Levels |
| ---: | --- | ---: | ---: | ---: |
| 1-7, 10 | PS reset to PSRAM input-DDR reset recovery | `+0.139` to `+0.277 ns` | 80.4-81.3% | 1 |
| 8 | Disk II seek state to zero-length sound-event state | `+0.268 ns` | 69.1% | 10 |
| 9 | PSRAM CE tape to the falling-edge CE output | `+0.269 ns` | 81.6% | 1 |

Keep the registered write-data stage, but do not promote or package this
build. It remains `0.161 ns` below the `+0.300 ns` setup gate, and no hardware
check has run. The current WNS is an asynchronous-reset recovery path into the
eight PSRAM input-DDR cells, not a read-data path. Review whether those cells
need their separate reset, prove reset-during-read and first-read behavior in
simulation, and measure that cut next. Do not change the registered write-data
stage based on global WNS alone; its measured residual is already `+0.288 ns`.

#### PSRAM Input-IDDR Reset Build

Commit `3c3a2064bbaf7817054a1e36f2f61a1010ccccbe` ties the reset input of
each PSRAM data IDDR low. Configuration still initializes both IDDR outputs to
zero. The input delays keep their existing reset, and fabric reset still
clears the PSRAM command state, capture tape, shift word, data, and response
valid state. A new read also clears the shift word before its delayed
eight-sample input window. The change removes only the eight redundant IDDR
reset sinks; it does not change the PSRAM clock, delay taps, sample phase, or
read and write state timing.

The focused XSim regression compared the production design with explicit
asynchronous-reset, synchronous-reset, and reset-free IDDR variants. It
checked both sampling phases, exact eight-sample reads, reset after samples
one, three, and seven, the first read after reset, reset during a QPI write,
and delay taps 0, 15, and 31. It also checked configuration initialization,
the retained input-delay resets, and the top-level reset connection. The
existing PSRAM handshake bench and 134 reported vTW, capture, egress, SDD,
overlay, video, standard-Disk-II, and WOZ checks passed.

The clean full build `20260813T141240Z-3c3a2064-full` used Vivado 2025.2,
the default seed, no incremental reference, and no rescue pass. It exported
the candidate DCP, bitstream, and XSA.

| Check | Result |
| --- | ---: |
| Build status | `exported` |
| Setup WNS / TNS | `+0.013 ns` / `0.000 ns` |
| Setup failing endpoints | `0` |
| Hold WNS / TNS | `+0.049 ns` / `0.000 ns` |
| Pulse-width WNS / TNS | `+0.265 ns` / `0.000 ns` |
| Worst bus-skew slack | `+5.909 ns` |
| Route errors | `0` |
| Missing XDC objects | `0` |
| Unconstrained internal endpoints | `0` |
| Rescue used | `0` |

The build used 10,125 slices, 30,597 LUTs, 20,375 registers, 74 block RAM
tiles, six DSPs, and 1,010 control sets. Against the AXI write-data build,
slices rose by 43, LUTs rose by four, registers rose by 72, and control sets
rose by one. Setup WNS fell by `0.126 ns`, hold WNS fell by `0.004 ns`, pulse
width did not change, and bus-skew slack rose by `0.001 ns`.

The target class is gone. The prior report had eight timing destinations on
PSRAM input-IDDR reset pins and 16 total report mentions of those pins; the
new report has none. The asynchronous 133 MHz group lost exactly those eight
endpoints and its WNS rose from `+0.139 ns` to `+1.158 ns`. Global WNS fell
because an unrelated, existing vTW address-direction output path routed
worse: its slack moved from `+0.885 ns` to `+0.013 ns` without a logic-depth
change.

| Rank | Path class | Slack | Route share | Levels |
| ---: | --- | ---: | ---: | ---: |
| 1 | vTW address-drive enable to `a2fpga_dir_a` | `+0.013 ns` | 49.7% | 2 |
| 2 | vTW cycle address to main shadow-RAM write enable | `+0.168 ns` | 83.2% | 7 |
| 3 | Registered AXI write data to Ethernet host write data | `+0.253 ns` | 94.6% | 0 |
| 4-6, 8 | vTW CPU and engine control to debug state | `+0.255` to `+0.286 ns` | 73.8-74.9% | 8 |
| 7, 9-10 | Disk II Q7 state to WOZ cached-line enables | `+0.280` to `+0.289 ns` | 79.7-79.8% | 9 |

Keep the reset cut, but do not promote or package this build. It remains
`0.287 ns` below the `+0.300 ns` setup gate, and no hardware check has run.
Trace the address-direction output route next while preserving its same-cycle
assertion and release, its `10.000 ns` maximum-delay constraint, and its
current electrical slew. Do not infer PSRAM eye margin from RTL simulation;
run the eye calibration and real PSRAM, Disk II, WOZ, and vTW read/write checks
when hardware becomes available.

#### Address-Direction Final-LUT Placement Build

Commit `e6654ba9cc8f3b11c4cf454c186a50dc2a23f463` factors the address-drive
enable into the Boolean-equivalent OR of vTW and all other clients, then keeps
that final LUT at `SLICE_X112Y23/A6LUT` near the U17 direction output. It adds
no register or bus phase. The INH safety gate remains before both inputs, the
DIR_A pad keeps its slow edge, and the existing `10.000 ns` maximum-delay
constraint remains unchanged.

The focused arbiter regression compared the placed form with the generic
reduction for all 4,096 client-enable masks. It also checked every client's
assertion and release, every unsafe-INH block and re-enable, and a vTW to
Appli-Card handoff with no low gap. All 19 vTW benches passed, including the
physical Disk II bus, native and vTW WOZ read/write, and all vTW speed modes.
The Appli-Card suite and the 19 standard-Disk-II and 66 WOZ checks also passed.

The clean full build `20260813T145234Z-e6654ba9-full` used Vivado 2025.2,
the default seed, no incremental reference, and no rescue pass. It exported
the candidate DCP, bitstream, and XSA.

| Check | Result |
| --- | ---: |
| Build status | `exported` |
| Setup WNS / TNS | `+0.106 ns` / `0.000 ns` |
| Setup failing endpoints | `0` |
| Hold WNS / TNS | `+0.079 ns` / `0.000 ns` |
| Pulse-width WNS / TNS | `+0.265 ns` / `0.000 ns` |
| Worst bus-skew slack | `+5.809 ns` |
| Route errors | `0` |
| Missing XDC objects | `0` |
| Unconstrained internal endpoints | `0` |
| Rescue used | `0` |

The build used 10,037 slices, 30,597 LUTs, 20,381 registers, 74 block RAM
tiles, six DSPs, and 1,013 control sets. Against the PSRAM input-reset build,
slices fell by 88, LUTs did not change, registers rose by six, and control sets
rose by three. Setup WNS rose by `0.093 ns`, hold WNS rose by `0.030 ns`, pulse
width did not change, and bus-skew slack fell by `0.100 ns` while still
passing.

The placed LUT bound at the requested site. The exact vTW
`wr_addr_rw_en_q` to `a2fpga_dir_a` path kept the same LUT2 plus slow OBUF and
the same `10.000 ns` bound. Its slack rose from `+0.013 ns` to `+0.340 ns`,
clearing the local campaign gate by `0.040 ns`. Logic delay stayed at
`3.745 ns`; route delay fell from `3.702 ns` to `3.377 ns`. The longer route
into the near-pin LUT was outweighed by the final route falling from
`2.876 ns` to `1.641 ns`. The worst non-vTW DIR_A path is the Appli-Card at
`+0.895 ns`; none of the eight timed DIR_A paths remains below `+0.300 ns`.

| Rank | Path class | Slack | Route share | Levels |
| ---: | --- | ---: | ---: | ---: |
| 1 | Disk II seek start to zero-length sound-event state | `+0.106 ns` | 64.8% | 11 |
| 2-5, 9 | Disk II track length to vTW PC-trace enables | `+0.156` to `+0.212 ns` | 78.1% | 10 |
| 6-7 | SDD producer pointer to free-beat reset state | `+0.200 ns` | 58.0% | 13 |
| 8 | PS AXI address state to exclusive-lock state | `+0.204 ns` | 52.7% | 15 |
| 10 | vTW CPU accumulator to status state | `+0.217 ns` | 60.0% | 13 |

Keep the placed final OR, but do not promote or package this build. Global
setup remains `0.194 ns` below the `+0.300 ns` gate, and hardware validation
is deferred. The extra methodology warning is the control-set count crossing
Vivado's advisory threshold, not a timing or route failure. Trace the Disk II
sound zero-length calculation next. Keep this physical constraint tied to the
fixed production device and U17 pin, and later check DIR_A handoff and edge
quality on hardware.

#### Disk II Sound Zero-Length Retime Build

Commit `f0d13f64ed70231621be699c31b25c2e2d1fa75e` moves the Disk II seek
zero-length comparison into the existing next sound-event pipeline stage. It
compares the registered start and end sample positions, removes the prior
zero-length register, and adds no pipeline stage or event latency. It changes
sound-event setup only; it does not change Disk II rotation, Q6/Q7, media
reads or writes, WOZ state, or vTW cycle pacing.

The standard-Disk-II regression exhaustively compared the old arithmetic and
the independent boundary rule for all 16 event codes, all 256 start tracks,
and all 256 distances. It also checked the exact registered-stage contract.
All 20 standard-Disk-II checks, 66 WOZ checks, and 19 vTW benches passed.
The vTW suite includes the physical Disk II bus, native and vTW WOZ
read/write, and every supported vTW speed.

The clean full build `20260813T151743Z-f0d13f64-full` used Vivado 2025.2,
the default seed, no incremental reference, and no rescue pass. It exported
the candidate DCP, bitstream, and XSA.

| Check | Result |
| --- | ---: |
| Build status | `exported` |
| Setup WNS / TNS | `+0.083 ns` / `0.000 ns` |
| Setup failing endpoints | `0` |
| Hold WNS / TNS | `+0.039 ns` / `0.000 ns` |
| Pulse-width WNS / TNS | `+0.265 ns` / `0.000 ns` |
| Worst bus-skew slack | `+5.883 ns` |
| Route errors | `0` |
| Missing XDC objects | `0` |
| Unconstrained internal endpoints | `0` |
| Rescue used | `0` |

The build used 10,131 slices, 30,469 LUTs, 20,349 registers, 74 block RAM
tiles, six DSPs, and 1,008 control sets. Against the address-direction build,
slices rose by 94, LUTs fell by 128, registers fell by 32, and control sets
fell by five. Setup WNS fell by `0.023 ns`, hold WNS fell by `0.040 ns`, pulse
width did not change, and bus-skew slack rose by `0.074 ns`. The control-set
method warning also cleared.

The saved checkpoints prove the local cut. The prior
`event_pos_zero_length_q` endpoint had a worst `+0.106 ns` path with 11 logic
levels. That register, its D pin, and all matching nets are absent from the
new checkpoint. The worst registered-position to replacement zero-length
path has `+4.815 ns` slack and three logic levels. The worst setup-input path
to the registered end position has `+1.780 ns` slack. The local sound cone is
therefore no longer near the timing limit.

| Rank | Path class | Slack | Route share | Levels |
| ---: | --- | ---: | ---: | ---: |
| 1-3, 5, 9 | vTW cycle address to shadow-RAM write/address pins | `+0.083` to `+0.240 ns` | 82.9-84.2% | 6-7 |
| 4, 7-8 | Registered AXI write data to vTW host/control state | `+0.190` to `+0.239 ns` | 91.1-94.3% | 0-1 |
| 6 | Apple address state to Disk II WOZ shift enable | `+0.226 ns` | 83.2% | 7 |
| 10 | Registered AXI write data to boot-ROM write address | `+0.242 ns` | 94.6% | 0 |

Keep the sound retime, but do not promote or package this build. The local
target is gone, while unrelated placement exposed the vTW shadow path and
left global setup `0.217 ns` below the `+0.300 ns` gate. Trace the captured
cycle-address to shadow-RAM cone next. Preserve the Apple-cycle translation
snapshot and do not add a vTW core state or change Disk II time-ready pacing.
Hardware validation remains deferred.

#### vTW Translated Route-Tuple Capture Build

Commit `f1e3da2845efcb1e0db98648646d5c21144fa748` translates the stable
W65C02 cycle during the existing `X_CAPTURE` state and saves the decoded
address, route class, shadow validity, and final shadow address beside the
raw cycle tuple. `X_ROUTE` consumes those registers. The change adds no FSM
state or Apple cycle, and the private switch manager still applies the saved
access at `X_ROUTE`, after translation used the pre-access switch state.

The full-system vTW monitor recomputed the prior translator result for every
saved cycle and compared all four fields. It observed bus, ROM, main, aux,
and RamWorks routes. Existing checks continued to prove C071/C073 phase
order, language-card and C3/CFFF behavior, posted-write order and pressure,
RamWorks miss/fill/writeback, and SmartPort and Disk II shortcuts. All 19
vTW benches, 20 standard-Disk-II checks, and 66 WOZ checks passed.

The clean full build `20260813T154352Z-f1e3da28-full` used Vivado 2025.2,
the default seed, no incremental reference, and no rescue pass. It exported
the candidate DCP, bitstream, and XSA.

| Check | Result |
| --- | ---: |
| Build status | `exported` |
| Setup WNS / TNS | `+0.151 ns` / `0.000 ns` |
| Setup failing endpoints | `0` |
| Hold WNS / TNS | `+0.033 ns` / `0.000 ns` |
| Pulse-width WNS / TNS | `+0.265 ns` / `0.000 ns` |
| Worst bus-skew slack | `+5.778 ns` |
| Route errors | `0` |
| Missing XDC objects | `0` |
| Unconstrained internal endpoints | `0` |
| Rescue used | `0` |

The build used 9,898 slices, 30,612 LUTs, 20,300 registers, 74 block RAM
tiles, six DSPs, and 1,013 control sets. Against the sound-retime build,
slices fell by 233, LUTs rose by 143, registers fell by 49, and control sets
rose by five. Setup WNS rose by `0.068 ns`, hold WNS fell by `0.006 ns`,
pulse width did not change, and bus-skew slack fell by `0.105 ns` while still
passing. The control-set count again crossed Vivado's advisory threshold;
it did not cause a timing or route failure.

The focused routed queries prove the intended cut. In the prior checkpoint,
the cycle-address and translate-state register banks each produced 600 paths
to the shadow address/write pins; their worst paths were `+0.083 ns` and
`+0.093 ns`, both seven levels into aux write enable. In the new checkpoint,
the translate-state bank has no path to any of the 432 write pins or 1,152
address pins. The captured tuple's worst residuals are `+1.816 ns` to write
enable with two levels and `+2.457 ns` to an address pin with one level.

Raw `cycle_addr_q` still reaches the shadow through the separate floating-bus
address mux. Those residual paths are not the removed translation cone: their
worst slack is `+0.846 ns` to write enable and `+0.620 ns` to an address pin.
The moved route-capture boundary has 32 timed endpoints. Its worst path is
W65C02 state to a saved shadow-address bit at `+0.230 ns` with eight levels;
the worst private-switch path is `+2.959 ns`.

| Rank | Path class | Slack | Route share | Levels |
| ---: | --- | ---: | ---: | ---: |
| 1 | W65C02 decimal arithmetic flag update | `+0.151 ns` | 63.9% | 14 |
| 2, 4, 6 | W65C02 state to captured shadow address | `+0.230` to `+0.284 ns` | 75.4-75.6% | 8 |
| 3 | PS AXI exclusive-access overlap state | `+0.247 ns` | 52.2% | 14 |
| 5 | vTW address-drive state to DIR_A | `+0.282 ns` | 47.8% | 2 |
| 7-10 | Registered AXI write data to boot-ROM write address | `+0.285 ns` | 94.7% | 0 |

Keep the captured route tuple, but do not promote or package this build.
Global setup remains `0.149 ns` below the `+0.300 ns` gate, and hardware
validation is deferred. The shadow-memory side of this cut now has ample
margin. Trace the W65C02 decimal flag cone next and use its existing decimal
extra cycle if a retime can preserve every bus cycle and architectural result.
Do not change the live Disk II WOZ path based on this report.

#### W65C02 Decimal-Result Retime Build

Commit `1adfc51fa719356bd5b3188b09fc937e7c9b3476` saves the exact ADC or
SBC result when a decimal operand is accepted, then commits A and P during
the W65C02's existing decimal-extra cycle. It adds no bus cycle or CPU state.
The extra-cycle dummy address, instruction boundary, binary arithmetic, and
all non-ADC/SBC paths remain unchanged. A small pending bit preserves an SO
edge while RDY or the core enable holds the extra cycle.

The CPU tests now fail with a nonzero simulator exit on any mismatch. All
180,000 WDC ADC/SBC vectors passed with exact state and bus-cycle checks over
all 18 opcode and addressing-mode forms. The Klaus decimal test checked A,
N, V, Z, and C for every accumulator, operand, and carry-in value, including
invalid BCD digits; it passed 56,640,803 cycles and 18,396,348 instructions.
Directed tests also held decimal ADC with RDY, held decimal SBC with the core
enable, and asserted SO during a held extra cycle. All 19 vTW benches, 20
standard-Disk-II checks, and 66 WOZ checks passed.

The clean full build `20260813T162120Z-1adfc51f-full` used Vivado 2025.2,
the default seed, no incremental reference, and no rescue pass. It exported
the candidate DCP, bitstream, and XSA.

| Check | Result |
| --- | ---: |
| Build status | `exported` |
| Setup WNS / TNS | `+0.127 ns` / `0.000 ns` |
| Setup failing endpoints | `0` |
| Hold WNS / TNS | `+0.041 ns` / `0.000 ns` |
| Pulse-width WNS / TNS | `+0.265 ns` / `0.000 ns` |
| Worst bus-skew slack | `+5.851 ns` |
| Route errors | `0` |
| Missing XDC objects | `0` |
| Unconstrained internal endpoints | `0` |
| Rescue used | `0` |

The build used 10,081 slices, 30,623 LUTs, 20,394 registers, 74 block RAM
tiles, six DSPs, and 1,011 control sets. Against the route-capture build,
slices rose by 183, LUTs by 11, and registers by 94; control sets fell by two.
Setup WNS fell by `0.024 ns`, hold WNS rose by `0.008 ns`, pulse width did
not change, and bus-skew slack rose by `0.073 ns`. The new global limit is an
unrelated SSI263 route, not a CPU path.

The focused routed queries prove the local cut. The prior P-to-A/P path rose
from `+0.151 ns` to `+0.879 ns`; A-to-A/P rose from `+0.395 ns` to
`+0.788 ns`; and registered input data to A/P rose from `+0.301 ns` to
`+1.125 ns`. The new arithmetic capture boundary has at least `+1.331 ns`
slack, and the saved result to A/P commit has `+4.320 ns` slack with three
logic levels. Other binary A/P updates still share the old endpoints, so do
not claim that every path to those registers disappeared.

| Rank | Path class | Slack | Route share | Levels |
| ---: | --- | ---: | ---: | ---: |
| 1, 3-5, 7-8, 10 | SSI263 clear/start pulse to formant history | `+0.127` to `+0.252 ns` | 92.5-92.7% | 1 |
| 2, 9 | Apple read-data snapshot to Mockingboard VIA timer latch | `+0.132`, `+0.229 ns` | 93.9% | 0 |
| 6 | Registered AXI write data to SDD ring base | `+0.215 ns` | 94.9% | 0 |

Keep the decimal retime, but do not promote or package this build. It is
`0.173 ns` below the `+0.300 ns` gate, and hardware validation remains
deferred. Trace the merged SSI263 clear/start pulse next. Preserve its event
edge and the formant sample sequence; do not add an audio or Apple bus cycle.

#### SSI263 Backend-Start Register Build

Commit `f265db75818be771c6f26117e52da14432a0d14a` keeps the existing
SSI263 backend-start pulse as its own register. In the secondary Votrax
instance, synthesis had merged that private audio pulse with the VIA CB1
interrupt-clear pulse because both had the same value on every edge. The
change adds no logic state, audio cycle, or Apple bus cycle. It leaves physical
replication to implementation and does not impose a fanout limit.

A new XSim bench checked 89 edge and state conditions. Each accepted Votrax
write produced exactly one backend start and one VIA clear on the same edge,
with the exact translated SSI263 and SC-01 tuple. Normal SSI starts did not
clear the Votrax interrupt. Hard reset, Apple reset, and card disable cancelled
the event, and the formant pipeline cleared and restarted on the consume edge.
All 12 Phasor tests, 19 vTW benches, 20 standard-Disk-II checks, 66 WOZ checks,
and the common capture, egress, SDD, overlay, and VidHD regressions passed.

The clean full build `20260813T165055Z-f265db75-full` used Vivado 2025.2,
the default seed, no incremental reference, and no rescue pass. It exported
the candidate DCP, bitstream, and XSA.

| Check | Result |
| --- | ---: |
| Build status | `exported` |
| Setup WNS / TNS | `+0.138 ns` / `0.000 ns` |
| Setup failing endpoints | `0` |
| Hold WNS / TNS | `+0.072 ns` / `0.000 ns` |
| Pulse-width WNS / TNS | `+0.265 ns` / `0.000 ns` |
| Worst bus-skew slack | `+5.958 ns` |
| Route errors | `0` |
| Missing XDC objects | `0` |
| Unconstrained internal endpoints | `0` |
| Rescue used | `0` |

The build used 9,958 slices, 30,627 LUTs, 20,423 registers, 74 block RAM
tiles, six DSPs, and 1,011 control sets. Against the decimal-retime build,
slices fell by 123, LUTs rose by four, and registers rose by 29. Setup WNS
rose by `0.011 ns`, hold WNS by `0.031 ns`, and bus-skew slack by `0.107 ns`;
pulse width did not change. The methodology categories did not change.

The routed checkpoint proves the split. The prior 1,011-load VIA-clear
register no longer drives the formant history. The secondary backend-start
register is distinct at `SLICE_X67Y111/AFF` with 242 direct pins, while the
VIA-clear register has two pins. No VIA-clear path remains to the former seven
endpoints. Their worst slack is now `+2.976` to `+3.227 ns`, and the worst
remaining secondary start-to-formant path is `+2.466 ns`. Normal physical
optimization made smaller start-register copies without a manual fanout rule.

| Rank | Path class | Slack | Route share | Levels |
| ---: | --- | ---: | ---: | ---: |
| 1-4, 6-8, 10 | W65C02 mode to captured vTW shadow address | `+0.138` to `+0.284 ns` | 79.8-80.2% | 8 |
| 5, 9 | Registered AXI write data to mouse Y shadow | `+0.180`, `+0.223 ns` | 94.6-95.0% | 0 |

Keep the SSI263 register, but do not promote or package this build. It remains
`0.162 ns` below the `+0.300 ns` gate, and hardware validation is deferred.
Trace the W65C02-mode to route-capture cone next. Preserve the pre-access
translation snapshot and the existing `X_CAPTURE` to `X_ROUTE` sequence; do
not add a state or change the live Disk II path.

#### vTW Post-Capture Shadow-Map Build

Commit `1b7f01f600bd5ac0af09ede02f69348e5cf85b38` saves only the full
translated address and route kind during `X_CAPTURE`, then calls the shared
shadow mapper from that registered tuple during `X_ROUTE`. It removes the
redundant shadow-valid and 18-bit physical-address capture registers. The
change adds no state or Apple cycle and keeps the same pre-access soft-switch
snapshot.

The full-system monitor now checks the saved translator result, mapped shadow
address, port enable, and write control on every `X_ROUTE`. A directed
language-card test selects bank 1 with two `$C08B` reads and proves that
`$D022` reaches physical `$C022`, including the translated bit-12 remap. All
19 vTW benches, 20 standard-Disk-II checks, and 66 WOZ checks passed.

The clean full build `20260813T172644Z-1b7f01f6-full` used Vivado 2025.2,
the default seed, no incremental reference, and no rescue pass. It exported
the candidate DCP, bitstream, and XSA.

| Check | Result |
| --- | ---: |
| Build status | `exported` |
| Setup WNS / TNS | `+0.109 ns` / `0.000 ns` |
| Setup failing endpoints | `0` |
| Hold WNS / TNS | `+0.033 ns` / `0.000 ns` |
| Pulse-width WNS / TNS | `+0.265 ns` / `0.000 ns` |
| Worst bus-skew slack | `+5.966 ns` |
| Route errors | `0` |
| Missing XDC objects | `0` |
| Unconstrained internal endpoints | `0` |
| Rescue used | `0` |

The build used 10,106 slices, 30,467 LUTs, 20,306 registers, 74 block RAM
tiles, six DSPs, and 1,012 control sets. Against the backend-start build,
slices rose by 148, while LUTs fell by 160 and registers by 117. Setup WNS
fell by `0.029 ns`, hold WNS by `0.039 ns`, and bus-skew slack rose by
`0.008 ns`; pulse width did not change. The methodology categories and counts
did not change.

The old `cycle_xl_shadow_valid_q` and `cycle_xl_shadow_phys_q` cell families
are absent from the routed design. They had supplied eight of the prior global
top ten. The worst W65C02-state path into the 13 saved decoded/route endpoints
is now `+0.382 ns` with seven levels. From those registers, the worst shadow
write-enable path is `+1.038 ns` with five levels across 32 paths, and the
worst shadow-address path is `+0.804 ns` with four levels across 568 paths.
No vTW path remains in the new top ten. The lower global WNS comes from an
unrelated SSI263 DSP arithmetic path, not a residual route-capture path.

| Rank | Path class | Slack | Route share | Levels |
| ---: | --- | ---: | ---: | ---: |
| 1-2, 8 | SSI263 formant DSP return to filter state | `+0.109` to `+0.202 ns` | 47.5-48.3% | 20 |
| 3-6 | SDD egress consumer pointer to free-space state | `+0.129 ns` | 57.4% | 13 |
| 7, 9 | Apple read-data snapshot to SDD record data | `+0.199`, `+0.202 ns` | 93.8-93.9% | 0 |
| 10 | Disk II spin countdown to bit-offset enable | `+0.224 ns` | 82.1% | 7 |

Keep the post-capture map, but do not promote or package this build. It remains
`0.191 ns` below the `+0.300 ns` gate, and hardware validation is deferred.
Trace the SSI263 arithmetic and SDD free-space paths next. Do not alter the
live Disk II sequencer based on the rank-10 placement path alone.

#### SSI263 Filter-Finalization Build

Commit `9b89c5c801dd19b9ca21b3a43629e5cc9df4a170` saves the final signed
56-bit filter sum in the existing accumulator, then shifts, saturates, and
updates filter history in a new finalization state. The state is appended so
all prior state values stay fixed. The change adds seven fabric clocks to each
audio sample, raising the exact pipeline length from 144 to 151 clocks. The
normal 192-clock simulation cadence and the roughly 2,771-clock hardware
sample period remain above that bound.

The focused filter test passed 1,973 checks across all seven filter stages,
the last and non-last tap edges, signed saturation limits, history updates,
reset/restart cancellation, and exact output samples. The start-timing bench
passed 89 checks. Quoted `00` through `3F` sweeps proved 64 unique SSI263 IDs
and 64 unique native Votrax IDs; each 92,160-sample post-change stream matched
the exact pre-change RTL byte for byte. The 152-clock minimum matched the
192-clock output, while 151 clocks correctly preempted the final output edge.
All 12 Phasor checks, 19 vTW benches, 20 standard-Disk-II checks, and 66 WOZ
checks passed.

The clean full build `20260813T181310Z-9b89c5c8-full` used Vivado 2025.2,
the default seed, no incremental reference, and no rescue pass. It exported
the candidate DCP, bitstream, and XSA.

| Check | Result |
| --- | ---: |
| Build status | `exported` |
| Setup WNS / TNS | `+0.239 ns` / `0.000 ns` |
| Setup failing endpoints | `0` |
| Hold WNS / TNS | `+0.044 ns` / `0.000 ns` |
| Pulse-width WNS / TNS | `+0.265 ns` / `0.000 ns` |
| Worst bus-skew slack | `+5.861 ns` |
| Route errors | `0` |
| Missing XDC objects | `0` |
| Unconstrained internal endpoints | `0` |
| Rescue used | `0` |

The build used 9,913 slices, 30,270 LUTs, 20,274 registers, 74 block RAM
tiles, six DSPs, and 1,013 control sets. Against the post-capture shadow-map
build, slices fell by 193, LUTs by 197, and registers by 32. Setup WNS rose by
`0.130 ns` and hold WNS by `0.011 ns`; pulse width did not change. Bus-skew
slack fell by `0.105 ns` but still passed. The methodology categories and
counts did not change.

The routed checkpoint proves the intended split in both speech instances.
The direct DSP-to-974-filter/history-endpoint class has zero paths. In the
secondary instance, the worst DSP-to-accumulator path is `+4.016 ns` with 15
levels, and the worst accumulator-to-history path is `+1.862 ns` with seven
levels. The primary instance has `+4.029 ns` and `+1.752 ns` on the same two
halves. The former direct secondary path was `+0.109 ns` with 20 levels.

| Rank | Path class | Slack | Levels |
| ---: | --- | ---: | ---: |
| 1 | PS GP0 AXI exclusive-lock state | `+0.239 ns` | 15 |
| 2-9 | Disk II drive select to vTW debug trace enables | `+0.269` to `+0.279 ns` | 8 |
| 10 | Registered AXI write data to boot-ROM write address | `+0.284 ns` | 0 |

Keep the filter-finalization stage, but do not promote or package this build.
It remains `0.061 ns` below the `+0.300 ns` gate, and hardware validation is
deferred. The next work must address the AXI exclusive path and the independent
debug/boot paths; do not change Disk II media timing to fix a debug-only enable
cone.

#### AXI Exclusive-Monitor Removal Build

Commit `f5bc4b1d81119544b7a03a0bad0105ae90522607` disables the unused
exclusive monitor only in the hard-PS GP0 AxiSimple wrapper. The eight clients
are side-effect MMIO registers, not shared memory. Locked reads and writes now
return ordinary `OKAY`; a locked write still reaches its client, so firmware
must never issue atomic or exclusive requests to this register plane.

Both Cortex-A9 applications now map the one 1 MiB section containing all eight
clients (`0x40000000-0x4007FFFF`) as Device memory before their first PL
access. The generated startup tables retain Strongly Ordered mappings for all
1,024 GP0 sections. A fresh Vitis 2025.2 build succeeded for both applications.
The linked-image audit found one early Device mapping in each `main`, no
exclusive instructions in CPU1, and only the two dormant Xilinx BSP spinlock
instructions in CPU0. Neither image calls `Xil_InitializeSpinLock`.

The wrapper regression first proved that the old monitor returned `EXOKAY` for
a matching locked read/write pair. With the monitor disabled, the same pair
performed one client write and returned `OKAY`. The existing write-data skid,
burst, reset, response-order, and real Disk II BASE checks also passed. All 19
vTW benches, 20 standard-Disk-II checks, 66 WOZ checks, 16 SmartPort checks,
21 boot-menu/reset checks, and all remaining card/capture/video regressions
passed.

The clean full build `20260813T190639Z-f5bc4b1d-full` used Vivado 2025.2,
the default seed, no incremental reference, and no rescue pass. It exported
the candidate DCP, bitstream, and XSA. The generated implementation worker had
to be started after a local run-queue stall; it then completed the normal
saved strategy without changing any design input.

| Check | Result |
| --- | ---: |
| Build status | `exported` |
| Setup WNS / TNS | `+0.156 ns` / `0.000 ns` |
| Setup failing endpoints | `0` |
| Hold WNS / TNS | `+0.039 ns` / `0.000 ns` |
| Pulse-width WNS / TNS | `+0.265 ns` / `0.000 ns` |
| Worst bus-skew slack | `+5.989 ns` |
| Route errors | `0` |
| Missing XDC objects | `0` |
| Unconstrained internal endpoints | `0` |
| Rescue used | `0` |

The build used 10,219 slices, 30,130 LUTs, 20,188 registers, 2,845
`CARRY4` blocks, 74 block RAM tiles, six DSPs, and 1,012 control sets. Against
the SSI263 filter-finalization build, it removed 140 LUTs, 86 registers, and
28 `CARRY4` blocks, but occupied slices rose by 306. The methodology classes
and counts did not change.

The former `MAXIGP0AWSIZE[0]` to `r_lock_valid/D` path and its nine-stage
carry chain are absent. As a second structural check, the saved DCP archive
contains no `EXCLUSIVE_ACCESS`, `r_lock_valid`, `r_locked_burst`, `lock_addr`,
`lock_last`, `lock_len`, `lock_size`, `lock_id`, or `locked_write` names; the
baseline archive contained the first five families. This archive-name check is
not an exact Vivado object count, but it agrees with the synthesis and routed
reports. The global limit moved to an unchanged debug-only
class from Disk II drive selection through WOZ ready/cache logic into vTW PC
trace enables. Its worst routed slack moved from `+0.269 ns` to `+0.156 ns`
because of placement and route changes; no Disk II media timing or RTL changed.

| Rank | Path class | Slack | Levels |
| ---: | --- | ---: | ---: |
| 1 | Disk II drive select to vTW PC-trace enable | `+0.156 ns` | 10 |
| 2-9 | Same debug-only class | `+0.185` to `+0.186 ns` | 10 |
| 10 | Same debug-only class | `+0.197 ns` | 10 |

Keep the monitor removal as a protocol-policy and resource cleanup, but do not
claim a global timing win. Setup WNS fell by `0.083 ns` in this one routed
sample, and the build remains `0.144 ns` below the `+0.300 ns` promotion gate.
Do not promote or package it; hardware validation is still deferred. Trace the
debug-only Disk II-to-vTW enable cone next, and preserve Disk II controller and
media timing.

#### vTW Debug-Trace Event Pipeline Build

Commit `816ab96079f1acbdb629ac1d96558e5b44375209` queues each vTW PC-trace
event and its freeze reason for one fabric clock before updating the 16-entry
history. This removes Disk II readiness from the common clock enable on all
256 PC-history bits. The queue accepts one fetch per clock, keeps the trigger
PC and bad-C000-before-C600 reason priority, and drains across Apple RESET.
Only the public forensic history and freeze status appear one 133 MHz clock
later; the CPU, Disk II controller, media state, and cycle timing do not
change.

The focused bench covered adjacent fetches, a C600 trigger behind an older
pending PC, both freeze causes and their priority, a bad-C000 pulse without a
fetch, cancellation by debug clear and hard reset, and draining across Apple
RESET. Static checks forbid a direct `core_addr` write into the history. All
20 vTW benches, 20 standard-Disk-II checks, and 66 WOZ checks passed.

The clean full build `20260813T202256Z-816ab960-full` used Vivado 2025.2,
the default seed, no incremental reference, and no rescue pass. It exported
the candidate DCP, bitstream, and XSA.

| Check | Result |
| --- | ---: |
| Build status | `exported` |
| Setup WNS / TNS | `+0.148 ns` / `0.000 ns` |
| Setup failing endpoints | `0` |
| Hold WNS / TNS | `+0.016 ns` / `0.000 ns` |
| Pulse-width WNS / TNS | `+0.265 ns` / `0.000 ns` |
| Worst bus-skew slack | `+5.789 ns` |
| Route errors | `0` |
| Missing XDC objects | `0` |
| Unconstrained internal endpoints | `0` |
| Rescue used | `0` |

The exact routed query found five Disk II drive-select launch replicas, eight
WOZ cached-mask registers, and all 256 PC-trace CE and D pins. No path remains
from drive select, cached mask, or `d2_time_ready` to any PC-trace CE or D pin.
The replacement halves have ample margin: Disk II readiness to the event stage
is `+1.224 ns`, the event stage to the trace CE is `+3.100 ns`, and the saved
PC to the trace D input is `+5.978 ns`. The unchanged same-edge I/O-trace
freeze path is also clear at `+0.900 ns`.

The build uses 9,896 slices, 30,252 LUTs, 20,174 registers, 2,845 `CARRY4`
blocks, 74 block RAM tiles, six DSPs, and 1,010 control sets. Against the AXI
exclusive-monitor build, occupied slices fell by 323, registers by 14, F7
muxes by 51, and control sets by two; LUTs rose by 122. The prior control-set
methodology warning is gone, so the methodology count fell from 101 to 100.
The exported SHA-256 values are
`732a2159bde25bc57eddc0415881fad82de93fedc80bc9c70d2a9cd148617e3c`
for the DCP,
`d38ef493fd27cbce03045254b6dbcb5a028e2892e8e7e3c6e7e3af510a68286c`
for the bitstream, and
`f00daff21780d412a6cb770e109bd9f9f9cd167d2790bbd82f29b7625709829a`
for the XSA.

The former ten Disk-II-readiness-to-PC-trace paths are absent from the global
top ten. The new global limit is an unrelated zero-logic AXI write-skid route
to the vTW shadow-host FIFO at `+0.148 ns`. Four functional vTW-cycle-address
to Disk II bit-offset enables appear at `+0.297` to `+0.330 ns`; do not retime
those without a separate same-cycle proof.

| Rank | Path class | Slack | Levels |
| ---: | --- | ---: | ---: |
| 1-5 | Registered AXI write data to vTW/Phasor registers | `+0.148` to `+0.285 ns` | 0-1 |
| 6-9 | vTW cycle address to Disk II bit-offset enable | `+0.297` to `+0.330 ns` | 9 |
| 10 | PS reset register to PSRAM CE | `+0.338 ns` | 1 |

Keep the debug pipeline as a structural timing and packing cleanup. Global
setup WNS moved by only `-0.008 ns`, so do not call it a global timing gain.
The build remains `0.152 ns` below the `+0.300 ns` promotion gate. Do not
promote or package it; hardware validation is still deferred. The next work
should address the route-heavy registered AXI write-data class without
changing the exposed vTW-to-Disk-II functional timing.

#### AXI Write-Payload Fanout Trial (Rejected)

Commit `27913a0d3db5904f1d4748329caf78bcd952257c` changed production RTL only
by adding a `MAX_FANOUT = 64` hint to the registered 37-bit AXI write-skid
payload, and it updated the matching static guard. The hint asked synthesis to
clone the existing same-edge output registers; it did not add a skid state,
change AXI handshakes, or add a client clock cycle. The wrapper regression,
all 20 vTW benches, 12 Phasor checks, 16 SmartPort checks, 20
standard-Disk-II checks, and 66 WOZ checks passed.

The clean full build `20260813T205035Z-27913a0d-full` used Vivado 2025.2,
the default seed, no incremental reference, and no rescue pass. It exported
the candidate DCP, bitstream, and XSA.

| Check | Result |
| --- | ---: |
| Build status | `exported` |
| Setup WNS / TNS | `+0.052 ns` / `0.000 ns` |
| Setup failing endpoints | `0` |
| Hold WNS / TNS | `+0.057 ns` / `0.000 ns` |
| Pulse-width WNS / TNS | `+0.265 ns` / `0.000 ns` |
| Worst bus-skew slack | `+5.773 ns` |
| Route errors | `0` |
| Missing XDC objects | `0` |
| Unconstrained internal endpoints | `0` |
| Rescue used | `0` |

The hint worked locally. The routed DCP has 76 write-skid output FDREs instead
of 39. Each measured target bit has one original and two copies, all on the
same 133 MHz clock, and the largest measured direct load fell from 147 to 60.
The worst output-register D and CE paths were `+2.080 ns` and `+2.444 ns`.

| Former target | Baseline slack | Trial slack |
| --- | ---: | ---: |
| Write data bit 8 to shadow word FIFO | `+0.148 ns` | `+2.847 ns` |
| Write data bit 1 to Phasor pan | `+0.174 ns` | `+0.250 ns` |
| Write data bit 13 to the old shadow-pointer endpoint | `+0.204 ns` | `+3.849 ns` |
| Write data bit 5 to Phasor audio | `+0.272 ns` | `+0.725 ns` |
| Write data bit 5 to shadow byte data | `+0.285 ns` | `+2.963 ns` |

No write-skid path remains in the routed global top 30. Placement instead
exposed unrelated reset-to-SSI, W65C02-to-vTW-decode, SSI backend-start, and
Disk-II-to-vTW paths at `+0.052` to `+0.095 ns`. Against the debug-pipeline
baseline, setup WNS fell by `0.096 ns`; occupied slices rose by 133, LUTs by
43, and registers by 39. The build used 10,029 slices, 30,295 LUTs, 20,213
registers, 2,845 `CARRY4` blocks, 74 block RAM tiles, six DSPs, and 1,010
control sets. Methodology classes and counts did not change.

The exported SHA-256 values are
`c1258fe3985eb213a6fc714e4c5ae14bf40df98efcdca9f10f8cd88a27197e68`
for the DCP,
`037d698d486ce102b4b866a062ed790836a2704c8ca755edfe9adca9a1d49687`
for the bitstream, and
`5e9c7491ab754cd99cb0a901a2b759fd716dec2e44d655264fa6dd0361d625bf`
for the XSA.

Reject this trial. It fixed the named routes but made total timing and packing
worse, and it remained `0.248 ns` below the promotion gate. Local commit
`321ae0b62e9c3d8115b4c6de6dfbc8f7529dffc6` restores the prior RTL and test
guard. Do not lower the fanout limit or keep this broad replication hint.

#### Targeted vTW/Phasor Write-Payload Copy Build

Commit `22a4b39408209246e360ac4922ec7a872e448e91` adds a masked copy to the
existing registered AXI write skid. Only WDATA bits 1, 5, 8, and 13 plus all
four WSTRB bits get copy flops. The copy flops use the canonical output
register's exact initial value, reset, clock enable, and input mux; they do not
sample the canonical Q output or add an AXI cycle. Unselected bits remain
direct aliases. Only vTW shadow and Phasor pan/audio writes use the copied
bus; AWVALID, AWADDR, response state, and all other clients stay canonical.

The focused wrapper bench checked copy equality after every clock across
reset, idle, AW-first, W-first, simultaneous AW/W, both skid slots, poisoned
live inputs, a 16-beat burst, response stalls, and locked MMIO. Static checks
pin the mask, parameter order, update priority, aliases, full top-level
threading, and consumer list. All 20 vTW benches, 12 Phasor checks, 16
SmartPort checks, 20 standard-Disk-II checks, 66 WOZ checks, and 64 other
card/capture/video checks passed. The capture-FIFO suite still reports its
existing note that a nonzero jam address freezes after 65 events while the
RTL comment says 64.

The clean full build `20260814T014836Z-22a4b394-full` used Vivado 2025.2,
the default seed, no incremental reference, and no rescue pass. It exported
the candidate DCP, bitstream, and XSA.

| Check | Result |
| --- | ---: |
| Build status | `exported` |
| Setup WNS / TNS | `+0.243 ns` / `0.000 ns` |
| Setup failing endpoints | `0` |
| Hold WNS / TNS | `+0.015 ns` / `0.000 ns` |
| Pulse-width WNS / TNS | `+0.265 ns` / `0.000 ns` |
| Worst bus-skew slack | `+5.893 ns` |
| Route errors | `0` |
| Missing XDC objects | `0` |
| Unconstrained internal endpoints | `0` |
| Rescue used | `0` |

The routed DCP contains exactly eight enabled copy FDREs: bits 1, 5, 8, 13,
and 32 through 35. They use the same 133 MHz clock, clock enable, and reset.
Their direct loads range from four to nine. The worst copy D and CE slacks are
`+2.091 ns` and `+1.487 ns`.

No path remains from a selected canonical write-data or strobe bit to the 658
switched vTW-shadow and Phasor D/CE endpoints. The former exact target paths
now start at the copy flops:

| Target | Routed slack |
| --- | ---: |
| Write data bit 8 to shadow word FIFO | `+4.564 ns` |
| Write data bit 1 to Phasor pan | `+4.018 ns` |
| Write data bit 13 to shadow pointer | `+5.139 ns` |
| Write data bit 5 to Phasor audio | `+5.285 ns` |
| Write data bit 5 to shadow byte data | `+5.038 ns` |

The build uses 9,868 slices, 30,181 LUTs, 20,218 registers, 2,843 `CARRY4`
blocks, 74 block RAM tiles, six DSPs, and 1,009 control sets. Against the vTW
debug-pipeline baseline, slices fell by 28, LUTs by 71, `CARRY4` blocks by two,
and control sets by one; registers rose by 44. The methodology set remains 100
findings with no new class.

| Rank | Path class | Slack | Levels |
| ---: | --- | ---: | ---: |
| 1-3, 8-10 | Reset replica to primary SSI263 filter reset | `+0.243` to `+0.289 ns` | 1 |
| 4-5 | Unmasked write-data bit 4 to Phasor/SmartPort state | `+0.262` / `+0.265 ns` | 0 |
| 6-7 | W65C02 state to vTW debug-reason staging | `+0.278` / `+0.283 ns` | 6 |

The exported SHA-256 values are
`0515b7e2019f7c7c1bab2c5b31a192e4db9595c3197292cc4dfcbb23a2564e67`
for the DCP,
`89f612e685152958b91f759c8a3c45b8ab6fec9906ca42628487e5c62aae0c8b`
for the bitstream, and
`554097de5cb1ac89ad5b064b30bb2a07488aacea141577d3f8f6f26337b5bb81`
for the XSA.

Keep this targeted copy. It improves setup WNS by `0.095 ns`, removes every
selected old target, reduces slices and LUTs, and leaves all signoff checks
clean. Do not claim that it removes the whole write-skid class: unmasked bit 4
is still route-bound at `+0.262 ns`. The build remains `0.057 ns` below the
promotion gate, so do not promote or package it; hardware validation is still
deferred. Trace the SSI263 reset class next, then decide whether the bit-4
copy is still needed.

#### Rejected SSI263 Local Hard-Reset Decode Trial

Commit `6758a6e2d0497b7e2ca1cc2899a8cf00616a3b00` added one preserved
`LUT1 INIT=1` hard-reset decode inside each SSI263 formant backend. It changed
only the outer backend's synchronous hard-reset term. The nested digital core
kept its raw reset input, and card-disable and Apple warm-reset priority did
not change. Commit `38d6d84` reverts the trial after the routed audit.

The focused formant test passed 7,620 checks at the unchanged 151-clock
pipeline length and produced the same 12 exact samples. The start-timing bench
passed 89 checks, and all 12 Phasor checks passed. Fresh 64-phone SSI263 and
64-phone native Votrax runs each captured 92,160 samples. Their text and WAV
files matched the retained post-finalization goldens byte for byte.

The clean full build `20260814T024305Z-6758a6e2-full` used Vivado 2025.2,
the default seed, no incremental reference, and no rescue pass. It exported
the candidate DCP, bitstream, and XSA.

| Check | Result |
| --- | ---: |
| Build status | `exported` |
| Setup WNS / TNS | `+0.057 ns` / `0.000 ns` |
| Setup failing endpoints | `0` |
| Hold WNS / TNS | `+0.046 ns` / `0.000 ns` |
| Pulse-width WNS / TNS | `+0.265 ns` / `0.000 ns` |
| Worst bus-skew slack | `+5.931 ns` |
| Route errors | `0` |
| Missing XDC objects | `0` |
| Unconstrained internal endpoints | `0` |
| Rescue used | `0` |

The DCP proves the requested split. It contains exactly two distinct,
unfixed `LUT1 INIT=1` cells with `KEEP` and `DONT_TOUCH`. The primary local
decode drives 1,138 outer-backend reset endpoints; the secondary drives 553.
Neither local reset crosses into the other backend or the nested digital core.
The old global reset drives no outer-backend reset endpoint and still drives
the unchanged 157 secondary digital-core reset endpoints.

| Local reset leg | LUT location | Loads | Worst full-path slack |
| --- | --- | ---: | ---: |
| Primary backend | `X52Y104/D6LUT` | 444 | `+1.691 ns` |
| Secondary backend | `X87Y90/A6LUT` | 885 | `+2.194 ns` |

The target reset legs are therefore safe, but placement made another formant
path much worse. The new first three setup paths start at the Apple-bus reset
snapshot and end at primary `f2_y2`, `f2_y3`, and `f2n_y2` data inputs. Their
slacks are `+0.057`, `+0.059`, and `+0.101 ns`. The worst path has one logic
level and 7.337 ns data delay: 0.484 ns logic and 6.853 ns route. Global setup
margin fell by `0.186 ns` from the `+0.243 ns` baseline.

The trial uses 9,873 slices, 30,175 LUTs, 20,195 registers, 2,843 `CARRY4`
blocks, 74 block RAM tiles, six DSPs, and 1,010 control sets. Against the
baseline, slices rose by five and control sets by one; LUTs fell by six and
registers by 23. The 100 methodology findings and their classes did not
change.

The exported SHA-256 values are
`c4866f9583cb448949319c6b7b83625b9155820e703a101320838322405c8a94`
for the DCP,
`016e4752d924315571a9702681046e1899220ef26f7535d85cde33e0aa7425c2`
for the bitstream, and
`0e77466d54714028671a3298e4c4464d3b85b32596c85e249d64a6f73a329a4b`
for the XSA.

Reject this trial. The local reset split works, but the full routed design
loses 0.186 ns of setup margin and adds a control set. Keep the `22a4b39`
baseline. Do not widen this reset split or thread another reset partition
without a new path report and a separate safety case.

### 2. Group Apple Bus Snapshot Copies When Needed

The broad `MAX_FANOUT` trial is complete and rejected. Use a fresh path report
before adding explicit copies. If one sampled bus source still limits several
blocks, make same-edge copies in `apple_bus_wrapper` for these consumer groups:

- Card and slot logic.
- Cycle and SDD capture.
- vTW and video state.

Capture each copy on the same edge as the completed snapshot register. Do not
add a cycle to the bus event or copy a partly assembled bus word. Keep each
copy near its named consumers. Use `DONT_TOUCH` only on copy registers that
Vivado would merge; do not put it on the full cones.

Measure this as its own commit and full build. Remove the copies if they raise
LUT use or create a worse path without a clear timing gain.

## Phase 2: Reduce Congestion

### 1. Move the SSI263 F2 Table to Block RAM

The two audio back ends use the same 4,096 by 16-bit F2 data. Replace duplicate
LUT ROMs with one inferred true dual-port block RAM when both ports need an
independent read. Register the outputs and add the read cycle to the coefficient
load state. Audio sample work has thousands of fabric clocks available, so one
read cycle should fit. Prove address and coefficient order in simulation.

Measure block RAM, LUT, F7/F8, slice, and timing changes. Keep the edit only if
it frees useful logic or improves placement without an audio fault.

### 2. Move the SmartPort C8 ROM to Block RAM

Measure the SmartPort C8 ROM as a separate change. Its two registered read
ports should fit one true dual-port block RAM without adding a read cycle, but
the synthesis report must prove the mapping and the physical and vTW ROM tests
must prove byte and cycle order.

### 3. Test Control-Set Settings

Run a full build with synthesis control-set optimization threshold `8`.
Change no RTL in that experiment. Compare control sets, slices, LUTs, WNS, and
the top paths. Test `16` later only if `8` helps. Keep a setting only if it
gives repeatable gain.

For new RTL, prefer a shared enable and a synchronous reset when the behavior
allows it. Do not remove a needed reset or merge unrelated enables just to cut
the count.

### 4. Test Synthesis Retiming

Test `STEPS.SYNTH_DESIGN.ARGS.GLOBAL_RETIMING on` as one flow-only commit.
Vivado 2025.2 marks the old `RETIMING` property obsolete. Run all CDC and
source checks. Review every XDC query after retiming; hierarchy-based queries
may no longer bind. Keep retiming only if both timing and function pass.

### 5. Sweep Place Directives

Wait until the Phase 1 and ROM netlists stop changing. Then run a small full
build sweep with one placement directive per build: `ExtraNetDelay_high`,
`ExtraPostPlacementOpt`, then `AltSpreadLogic_high`. Keep synthesis, route, and
physical optimization fixed. Record every result, including failures. Use the
best repeatable result as a candidate; do not select one lucky build by WNS
alone.

Before any flow trial, fix the build record to read `GLOBAL_RETIMING`, record
the post-route enable and route options, and make promotion compare the Vivado
version and every flow field between both builds. Promotion must also require
`rescue_used=0`; an extra rescue pass does not show intrinsic margin.

#### Rejected `ExtraNetDelay_high` Placement Trial

Commit `851a634068004755610765e6cbe85fac2e64cd7d` adds a checked
`APPLETINI_PLACE_DIRECTIVE` build setting. The default remains `Explore`; the
setting accepts only the four planned directives, reads the applied value back
from `impl_1`, and records it in the timing manifest.

The clean full build `20260814T074859Z-851a6340-full` used
`ExtraNetDelay_high`, Vivado 2025.2, the default seed, no incremental
reference, and no rescue pass. It exported the candidate DCP, bitstream, and
XSA from a clean tree.

| Check | Result |
| --- | ---: |
| Build status | `exported` |
| Setup WNS / TNS | `+0.251 ns` / `0.000 ns` |
| Setup failing endpoints | `0` |
| Hold WNS / TNS | `+0.041 ns` / `0.000 ns` |
| Pulse-width WNS / TNS | `+0.265 ns` / `0.000 ns` |
| Worst bus-skew slack | `+5.822 ns` |
| Route errors | `0` |
| Missing XDC objects | `0` |
| Unconstrained internal endpoints | `0` |
| Rescue used | `0` |

Both clean `Explore` builds, `20260814T014836Z-22a4b394-full` and
`20260814T063549Z-e6df807c-full`, produced the same `+0.243 ns` setup WNS,
resources, methodology counts, and top ten. `ExtraNetDelay_high` therefore
gained only `0.008 ns`. It moved the former reset, unmasked write-data bit 4,
and vTW debug-reason classes out of the top ten, but exposed other route-heavy
paths:

| Rank | Path class | Slack | Levels |
| ---: | --- | ---: | ---: |
| 1 | Apple bus data bit 6 to SuperSprite PSG state | `+0.251 ns` | 0 |
| 2-3 | AXI write-skid bit 2 to boot-menu C8 ROM | `+0.264` / `+0.268 ns` | 0 |
| 4 | AXI write-skid bit 12 to boot-menu timeout state | `+0.274 ns` | 0 |
| 5 | vTW cycle address to shadow block-RAM write enable | `+0.318 ns` | 5 |

The build uses 9,925 slices, 30,165 LUTs, 20,235 registers, 2,843 `CARRY4`
blocks, 74 block RAM tiles, six DSPs, and 1,010 control sets. Against the
repeatable `Explore` reference, slices rose by 57, registers by 17, and
control sets by one; LUTs fell by 16. The methodology set remains the same
100 findings and the same six rule rows.

The exported SHA-256 values are
`79a27afa41eeca809e8a9c412c7919d14c6002bae0c556bef515a6bc699c5ad0`
for the DCP,
`6ba3d0ced33f7fc507dc83503a794c7ca13e34728c6fc20426696fe5a274bf5a`
for the bitstream, and
`5e40eb4680993926324147d095e76dd2a9abc69d607e837b1820dd290034827a`
for the XSA.

Reject this directive as the placement reference. Its `0.008 ns` gain does
not justify the slice, register, and control-set cost, and it remains
`0.049 ns` below the promotion gate. Keep the `+0.243 ns` `Explore` build as
the current reference. Retain the directive-control tooling and this archive
for the remaining bounded placement trials.

## Phase 3: Use Only if the Target Still Fails

### 1. Physical Response Stage

Complete in `fbddd819`. The stage removed the final card-response mux from the
data and direction pins but did not raise total WNS. Do not add another stage
unless a new report shows a remaining physical response path.

### 2. Add Small Pblocks

Use Phase 0 congestion reports to choose a target. Start with a soft pblock for
the capture FIFO and its local logic. Check route use and hold after each
change. Do not bind all vTW shadow RAM at once; it owns many block RAMs and can
make placement worse.

### 3. Keep 125 MHz as a Separate Fallback

Changing 133.333 MHz to 125 MHz adds 6.25 percent to the period. It also changes
vTW rates, PSRAM service, timeouts, counters, and any hard-coded fabric-clock
math. Treat it as a clock and firmware change, not a timing directive. List and
retune every clock-derived constant, then run the full test and hardware list.
Do not take this step unless the structural work fails.

## Checks for Each Change

Each structural change gets its own commit. Run the focused test first, then
the source regressions that cover the touched block. Before accepting a timing
candidate, run at least:

```powershell
python scripts/test_capture_fifos.py
python scripts/test_apple_cycle_egress.py
python scripts/test_sdd_stream.py
python scripts/test_linear_text_overlay.py
python scripts/test_vidhd_shr.py
```

Also run the card tests for any changed bus or arbiter path, including
SmartPort, Disk II, Uthernet, SSC, Mockingboard, and vTW checks.

For a hardware candidate, build Vitis and the exact firmware from its named
XSA and bitstream:

```powershell
python scripts/package_timing_firmware.py <tested-build-id>
```

The packer writes `FIRMWARE.BIN` and a component-hash manifest inside the
immutable timing-run directory. Test that file, not a root-level firmware from
another build.

Test boot menu, Disk II boot, SmartPort read and write, vTW, Mockingboard audit,
linear overlay, SDD, Uthernet, SSC, and reset behavior. Record the exact test
firmware only after all pass:

```powershell
vivado -mode batch -source scripts/mark_timing_hardware_validated.tcl `
  -tclargs <tested-build-id> `
  boot-menu,disk-ii,smartport,vtw,mb-audit,linear-overlay,sdd,uthernet,ssc,reset
```

Run the second clean full build from the same commit after hardware validation.
Promote only the two latest consecutive passing full builds:

```powershell
vivado -mode batch -source scripts/promote_timing_candidate.tcl `
  -tclargs <tested-build-id> <confirm-build-id>
```

## Commit and Stop Rules

- Put one structural change in each commit.
- Do not mix RTL, a flow experiment, and a floorplan change.
- Keep all failed build records. Revert a failed experiment in a new scoped
  commit or before starting the next one.
- Do not promote a new fabric feature while setup WNS is below `+0.300 ns`.
- A correctness or safety fix may proceed below the margin bar, but it must use
  a full build and hardware test and must not become the timing reference until
  it passes the normal gate.
- Stop a phase when two clean full builds and hardware tests meet the target.
  Do not add later timing changes without a measured need.

Expected useful margin is `+0.300 ns` to about `+0.800 ns`. The measured gates,
not that estimate, decide when the campaign ends.
