hasseily/appletini-one/schematics/sc02_prototype/kicad/sc02_sheet_01_analog_1_schdoc.kicad_sch

## KiCad design schematics/sc02_prototype/kicad/sc02_sheet_01_analog_1_schdoc.kicad_sch (2026-08-26)

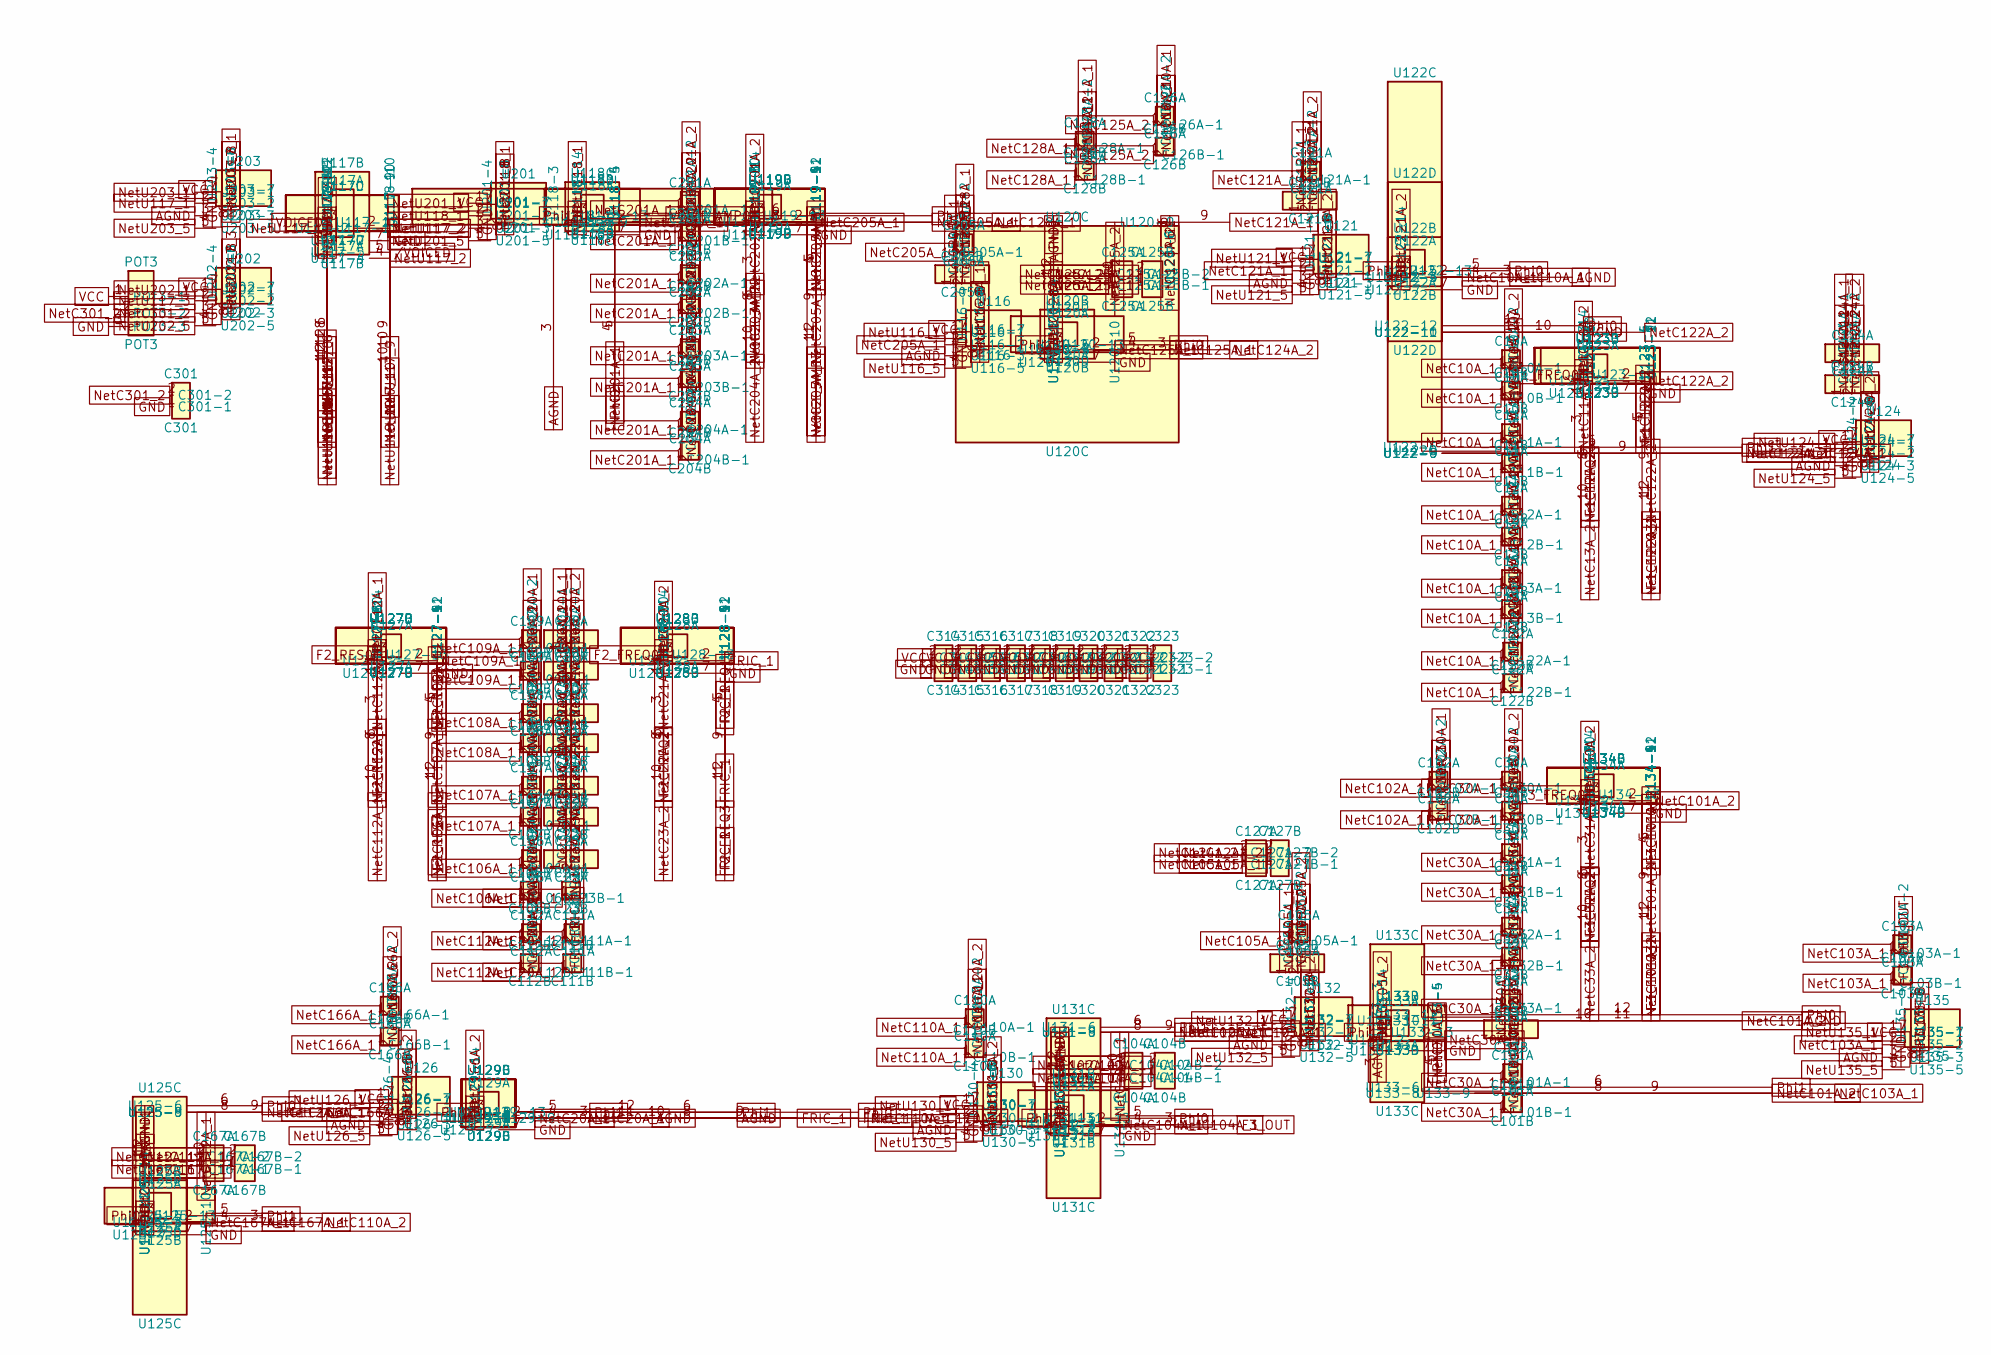
[picture p49: schematic sc02_sheet_01_analog_1_schdoc.kicad_sch]

Parts:
C10A: C10A
C10B: C10B
C11A: C11A
C11B: C11B
C12A: C12A
C12B: C12B
C13A: C13A
C13B: C13B
C20A: C20A
C20B: C20B
C21A: C21A
C21B: C21B
C22A: C22A
C22B: C22B
C23A: C23A
C23B: C23B
C30A: C30A
C30B: C30B
C31A: C31A
C31B: C31B
C32A: C32A
C32B: C32B
C33A: C33A
C33B: C33B
C101A: C101A
C101B: C101B
C102A: C102A
C102B: C102B
C103A: C103A
C103B: C103B
C104A: C104A
C104B: C104B
C105A: C105A
C105B: C105B
C106A: C106A
C106B: C106B
C107A: C107A
C107B: C107B
C108A: C108A
C108B: C108B
C109A: C109A
C109B: C109B
C110A: C110A
C110B: C110B
C111A: C111A
C111B: C111B
C112A: C112A
C112B: C112B
C121A: C121A
C121B: C121B
C122A: C122A
C122B: C122B
C124A: C124A
C124B: C124B
C125A: C125A
C125B: C125B
C126A: C126A
C126B: C126B
C127A: C127A
C127B: C127B
C128A: C128A
C128B: C128B
C166A: C166A
C166B: C166B
C167A: C167A
C167B: C167B
C201A: C201A
C201B: C201B
C202A: C202A
C202B: C202B
C203A: C203A
C203B: C203B
C204A: C204A
C204B: C204B
C205A: C205A
C205B: C205B
C301: C301
C314: C314
C315: C315
C316: C316
C317: C317
C318: C318
C319: C319
C320: C320
C321: C321
C322: C322
C323: C323
POT3: POT3
U116: U116
U117A: U117A
U117B: U117B
U117C: U117C
U117D: U117D
U118A: U118A
U118B: U118B
U118C: U118C
U118D: U118D
U119A: U119A
U119B: U119B
U119C: U119C
U119D: U119D
U120A: U120A
U120B: U120B
U120C: U120C
U120D: U120D
U121: U121
U122A: U122A
U122B: U122B
U122C: U122C
U122D: U122D
U123A: U123A
U123B: U123B
U123C: U123C
U123D: U123D
U124: U124
U125A: U125A
U125B: U125B
U125C: U125C
U125D: U125D
U126: U126
U127A: U127A
U127B: U127B
U127C: U127C
U127D: U127D
U128A: U128A
U128B: U128B
U128C: U128C
U128D: U128D
U129A: U129A
U129B: U129B
U129C: U129C
U129D: U129D
U130: U130
U131A: U131A
U131B: U131B
U131C: U131C
U131D: U131D
U132: U132
U133A: U133A
U133B: U133B
U133C: U133C
U133D: U133D
U134A: U134A
U134B: U134B
U134C: U134C
U134D: U134D
U135: U135
U201: U201
U202: U202
U203: U203

Connections:
/VOICED: U117B.5 (U117-5)
AGND: U116.3 (U116-3), U118B.3 (U118-3), U120D.11 (U120-11), U121.3 (U121-3), U122B.3 (U122-3), U122D.11 (U122-11), U124.3 (U124-3), U125D.11 (U125-11), U126.3 (U126-3), U129B.3 (U129-3), U129D.11 (U129-11), U130.3 (U130-3), U131D.11 (U131-11), U132.3 (U132-3), U133B.3 (U133-3), U133D.11 (U133-11), U135.3 (U135-3), U203.3 (U203-3)
F1_FREQ0: U123A.13 (U123-13)
F1_FREQ1: U123B.5 (U123-5)
F1_FREQ2: U123C.6 (U123-6)
F1_FREQ3: U123D.12 (U123-12)
F2_FREQ0: U128A.13 (U128-13)
F2_FREQ1: U128B.5 (U128-5)
F2_FREQ2: U128C.6 (U128-6)
F2_FREQ3: U128D.12 (U128-12)
F2_RES0: U127A.13 (U127-13)
F2_RES1: U127B.5 (U127-5)
F2_RES2: U127C.6 (U127-6)
F2_RES3: U127D.12 (U127-12)
F3_FREQ0: U134A.13 (U134-13)
F3_FREQ1: U134B.5 (U134-5)
F3_FREQ2: U134C.6 (U134-6)
F3_FREQ3: U134D.12 (U134-12)
F3_OUT: C103A.2 (C103A-2), C103B.2 (C103B-2), U131B.3 (U131-3), U135.6 (U135-6)
FRIC_1: C111A.2 (C111A-2), C111B.2 (C111B-2), U128A.2 (U128-2), U128B.4 (U128-4), U128C.9 (U128-9), U128D.11 (U128-11), U129C.8 (U129-8), U129D.10 (U129-10)
GND: C301.1 (C301-1), C314.1 (C314-1), C315.1 (C315-1), C316.1 (C316-1), C317.1 (C317-1), C318.1 (C318-1), C319.1 (C319-1), C320.1 (C320-1), C321.1 (C321-1), C322.1 (C322-1), C323.1 (C323-1), POT3.3 (POT3-3), U116.4 (U116-4), U117B.7 (U117-7), U118A.7 (U118-7), U119A.7 (U119-7), U120A.7 (U120-7), U121.4 (U121-4), U122A.7 (U122-7), U123A.7 (U123-7), U124.4 (U124-4), U125A.7 (U125-7), U126.4 (U126-4), U127A.7 (U127-7), U128A.7 (U128-7), U129A.7 (U129-7), U130.4 (U130-4), U131A.7 (U131-7), U132.4 (U132-4), U133A.7 (U133-7), U134A.7 (U134-7), U135.4 (U135-4), U201.4 (U201-4), U202.4 (U202-4), U203.4 (U203-4)
NetC10A_1: C10A.1 (C10A-1), C10B.1 (C10B-1), C11A.1 (C11A-1), C11B.1 (C11B-1), C12A.1 (C12A-1), C12B.1 (C12B-1), C13A.1 (C13A-1), C13B.1 (C13B-1), C122A.1 (C122A-1), C122B.1 (C122B-1), C126A.2 (C126A-2), C126B.2 (C126B-2), U122A.2 (U122-2), U122B.4 (U122-4)
NetC10A_2: C10A.2 (C10A-2), C10B.2 (C10B-2), U123A.1 (U123-1)
NetC11A_2: C11A.2 (C11A-2), C11B.2 (C11B-2), U123B.3 (U123-3)
NetC12A_2: C12A.2 (C12A-2), C12B.2 (C12B-2), U123C.8 (U123-8)
NetC13A_2: C13A.2 (C13A-2), C13B.2 (C13B-2), U123D.10 (U123-10)
NetC20A_1: C20A.1 (C20A-1), C20B.1 (C20B-1), C21A.1 (C21A-1), C21B.1 (C21B-1), C22A.1 (C22A-1), C22B.1 (C22B-1), C23A.1 (C23A-1), C23B.1 (C23B-1), C106A.2 (C106A-2), C106B.2 (C106B-2), C107A.2 (C107A-2), C107B.2 (C107B-2), C108A.2 (C108A-2), C108B.2 (C108B-2), C109A.2 (C109A-2), C109B.2 (C109B-2), C111A.1 (C111A-1), C111B.1 (C111B-1), C112A.2 (C112A-2), C112B.2 (C112B-2), U129A.2 (U129-2), U129B.4 (U129-4)
NetC20A_2: C20A.2 (C20A-2), C20B.2 (C20B-2), U128A.1 (U128-1)
NetC21A_2: C21A.2 (C21A-2), C21B.2 (C21B-2), U128B.3 (U128-3)
NetC22A_2: C22A.2 (C22A-2), C22B.2 (C22B-2), U128C.8 (U128-8)
NetC23A_2: C23A.2 (C23A-2), C23B.2 (C23B-2), U128D.10 (U128-10)
NetC30A_1: C30A.1 (C30A-1), C30B.1 (C30B-1), C31A.1 (C31A-1), C31B.1 (C31B-1), C32A.1 (C32A-1), C32B.1 (C32B-1), C33A.1 (C33A-1), C33B.1 (C33B-1), C101A.1 (C101A-1), C101B.1 (C101B-1), C102A.2 (C102A-2), C102B.2 (C102B-2), U133A.2 (U133-2), U133B.4 (U133-4)
NetC30A_2: C30A.2 (C30A-2), C30B.2 (C30B-2), U134A.1 (U134-1)
NetC31A_2: C31A.2 (C31A-2), C31B.2 (C31B-2), U134B.3 (U134-3)
NetC32A_2: C32A.2 (C32A-2), C32B.2 (C32B-2), U134C.8 (U134-8)
NetC33A_2: C33A.2 (C33A-2), C33B.2 (C33B-2), U134D.10 (U134-10)
NetC101A_2: C101A.2 (C101A-2), C101B.2 (C101B-2), U133C.8 (U133-8), U133D.10 (U133-10), U134A.2 (U134-2), U134B.4 (U134-4), U134C.9 (U134-9), U134D.11 (U134-11)
NetC102A_1: C102A.1 (C102A-1), C102B.1 (C102B-1), C104A.2 (C104A-2), C104B.2 (C104B-2), U131C.8 (U131-8), U131D.10 (U131-10)
NetC103A_1: C103A.1 (C103A-1), C103B.1 (C103B-1), U133C.9 (U133-9), U135.2 (U135-2)
NetC104A_1: C104A.1 (C104A-1), C104B.1 (C104B-1), U131A.2 (U131-2), U131B.4 (U131-4)
NetC105A_1: C105A.1 (C105A-1), C105B.1 (C105B-1), C127A.1 (C127A-1), C127B.1 (C127B-1), U131C.9 (U131-9), U132.2 (U132-2)
NetC105A_2: C105A.2 (C105A-2), C105B.2 (C105B-2), U132.6 (U132-6), U133A.1 (U133-1)
NetC106A_1: C106A.1 (C106A-1), C106B.1 (C106B-1), U127D.11 (U127-11)
NetC107A_1: C107A.1 (C107A-1), C107B.1 (C107B-1), U127C.9 (U127-9)
NetC108A_1: C108A.1 (C108A-1), C108B.1 (C108B-1), U127B.4 (U127-4)
NetC109A_1: C109A.1 (C109A-1), C109B.1 (C109B-1), U127A.2 (U127-2)
NetC110A_1: C110A.1 (C110A-1), C110B.1 (C110B-1), U129C.9 (U129-9), U130.2 (U130-2)
NetC110A_2: C110A.2 (C110A-2), C110B.2 (C110B-2), U125B.3 (U125-3), U130.6 (U130-6), U131A.1 (U131-1)
NetC112A_1: C112A.1 (C112A-1), C112B.1 (C112B-1), C167A.2 (C167A-2), C167B.2 (C167B-2), U125C.8 (U125-8), U125D.10 (U125-10), U127A.1 (U127-1), U127B.3 (U127-3), U127C.8 (U127-8), U127D.10 (U127-10)
NetC121A_1: C121A.1 (C121A-1), C121B.1 (C121B-1), C128A.2 (C128A-2), C128B.2 (C128B-2), U120C.9 (U120-9), U121.2 (U121-2)
NetC121A_2: C121A.2 (C121A-2), C121B.2 (C121B-2), U121.6 (U121-6), U122A.1 (U122-1)
NetC122A_2: C122A.2 (C122A-2), C122B.2 (C122B-2), U122C.8 (U122-8), U122D.10 (U122-10), U123A.2 (U123-2), U123B.4 (U123-4), U123C.9 (U123-9), U123D.11 (U123-11)
NetC124A_1: C124A.1 (C124A-1), C124B.1 (C124B-1), U122C.9 (U122-9), U124.2 (U124-2)
NetC124A_2: C124A.2 (C124A-2), C124B.2 (C124B-2), C127A.2 (C127A-2), C127B.2 (C127B-2), U120B.3 (U120-3), U124.6 (U124-6), U125A.1 (U125-1)
NetC125A_1: C125A.1 (C125A-1), C125B.1 (C125B-1), U120A.2 (U120-2), U120B.4 (U120-4)
NetC125A_2: C125A.2 (C125A-2), C125B.2 (C125B-2), C126A.1 (C126A-1), C126B.1 (C126B-1), U120C.8 (U120-8), U120D.10 (U120-10)
NetC128A_1: C128A.1 (C128A-1), C128B.1 (C128B-1), C205A.2 (C205A-2), C205B.2 (C205B-2), U116.6 (U116-6), U118C.9 (U118-9), U120A.1 (U120-1)
NetC166A_1: C166A.1 (C166A-1), C166B.1 (C166B-1), U125C.9 (U125-9), U126.2 (U126-2)
NetC166A_2: C166A.2 (C166A-2), C166B.2 (C166B-2), U126.6 (U126-6), U129A.1 (U129-1)
NetC167A_1: C167A.1 (C167A-1), C167B.1 (C167B-1), U125A.2 (U125-2), U125B.4 (U125-4)
NetC201A_1: C201A.1 (C201A-1), C201B.1 (C201B-1), C202A.1 (C202A-1), C202B.1 (C202B-1), C203A.1 (C203A-1), C203B.1 (C203B-1), C204A.1 (C204A-1), C204B.1 (C204B-1), U118A.2 (U118-2), U118B.4 (U118-4)
NetC201A_2: C201A.2 (C201A-2), C201B.2 (C201B-2), U119A.1 (U119-1)
NetC202A_2: C202A.2 (C202A-2), C202B.2 (C202B-2), U119B.3 (U119-3)
NetC203A_2: C203A.2 (C203A-2), C203B.2 (C203B-2), U119C.8 (U119-8)
NetC204A_2: C204A.2 (C204A-2), C204B.2 (C204B-2), U119D.10 (U119-10)
NetC205A_1: C205A.1 (C205A-1), C205B.1 (C205B-1), U116.2 (U116-2), U118C.8 (U118-8), U119A.2 (U119-2), U119B.4 (U119-4), U119C.9 (U119-9), U119D.11 (U119-11)
NetC301_2: C301.2 (C301-2), POT3.2 (POT3-2), U202.3 (U202-3)
NetU116_1: U116.1 (U116-1)
NetU116_5: U116.5 (U116-5)
NetU116_8: U116.8 (U116-8)
NetU117_1: U117A.1 (U117-1), U203.2 (U203-2), U203.6 (U203-6)
NetU117_2: U117A.2 (U117-2), U117B.4 (U117-4), U201.3 (U201-3)
NetU117_3: U117B.3 (U117-3), U202.2 (U202-2), U202.6 (U202-6)
NetU117_6: U117C.6 (U117-6)
NetU117_8: U117C.8 (U117-8)
NetU117_9: U117C.9 (U117-9)
NetU117_10: U117D.10 (U117-10)
NetU117_11: U117D.11 (U117-11)
NetU117_12: U117D.12 (U117-12)
NetU118_1: U118A.1 (U118-1), U201.2 (U201-2), U201.6 (U201-6)
NetU118_10: U118D.10 (U118-10)
NetU118_11: U118D.11 (U118-11)
NetU118_12: U118D.12 (U118-12)
NetU121_1: U121.1 (U121-1)
NetU121_5: U121.5 (U121-5)
NetU121_8: U121.8 (U121-8)
NetU124_1: U124.1 (U124-1)
NetU124_5: U124.5 (U124-5)
NetU124_8: U124.8 (U124-8)
NetU126_1: U126.1 (U126-1)
NetU126_5: U126.5 (U126-5)
NetU126_8: U126.8 (U126-8)
NetU130_1: U130.1 (U130-1)
NetU130_5: U130.5 (U130-5)
NetU130_8: U130.8 (U130-8)
NetU132_1: U132.1 (U132-1)
NetU132_5: U132.5 (U132-5)
NetU132_8: U132.8 (U132-8)
NetU135_1: U135.1 (U135-1)
NetU135_5: U135.5 (U135-5)
NetU135_8: U135.8 (U135-8)
NetU201_1: U201.1 (U201-1)
NetU201_5: U201.5 (U201-5)
NetU201_8: U201.8 (U201-8)
NetU202_1: U202.1 (U202-1)
NetU202_5: U202.5 (U202-5)
NetU202_8: U202.8 (U202-8)
NetU203_1: U203.1 (U203-1)
NetU203_5: U203.5 (U203-5)
NetU203_8: U203.8 (U203-8)
Phi0: U118B.5 (U118-5), U118C.6 (U118-6), U120B.5 (U120-5), U120D.12 (U120-12), U122B.5 (U122-5), U122D.12 (U122-12), U125A.13 (U125-13), U125C.6 (U125-6), U129A.13 (U129-13), U129C.6 (U129-6), U131B.5 (U131-5), U131D.12 (U131-12), U133B.5 (U133-5), U133D.12 (U133-12)
Phi1: U118A.13 (U118-13), U120A.13 (U120-13), U120C.6 (U120-6), U122A.13 (U122-13), U122C.6 (U122-6), U125B.5 (U125-5), U125D.12 (U125-12), U129B.5 (U129-5), U129D.12 (U129-12), U131A.13 (U131-13), U131C.6 (U131-6), U133A.13 (U133-13), U133C.6 (U133-6)
VCC: C314.2 (C314-2), C315.2 (C315-2), C316.2 (C316-2), C317.2 (C317-2), C318.2 (C318-2), C319.2 (C319-2), C320.2 (C320-2), C321.2 (C321-2), C322.2 (C322-2), C323.2 (C323-2), POT3.1 (POT3-1), U116.7 (U116-7), U121.7 (U121-7), U124.7 (U124-7), U126.7 (U126-7), U130.7 (U130-7), U132.7 (U132-7), U135.7 (U135-7), U201.7 (U201-7), U202.7 (U202-7), U203.7 (U203-7)
VDD: U117A.14 (U117-14), U118A.14 (U118-14), U119A.14 (U119-14), U120A.14 (U120-14), U122A.14 (U122-14), U123A.14 (U123-14), U125A.14 (U125-14), U127A.14 (U127-14), U128A.14 (U128-14), U129A.14 (U129-14), U131A.14 (U131-14), U133A.14 (U133-14), U134A.14 (U134-14)
VOICED: U117A.13 (U117-13)
VOICE_AMP0: U119A.13 (U119-13)
VOICE_AMP1: U119B.5 (U119-5)
VOICE_AMP2: U119C.6 (U119-6)
VOICE_AMP3: U119D.12 (U119-12)
