hasseily/appletini-one/schematics/sc02_prototype/kicad/sc02_sheet_02_analog_2_schdoc.kicad_sch

## KiCad design schematics/sc02_prototype/kicad/sc02_sheet_02_analog_2_schdoc.kicad_sch (2026-08-26)

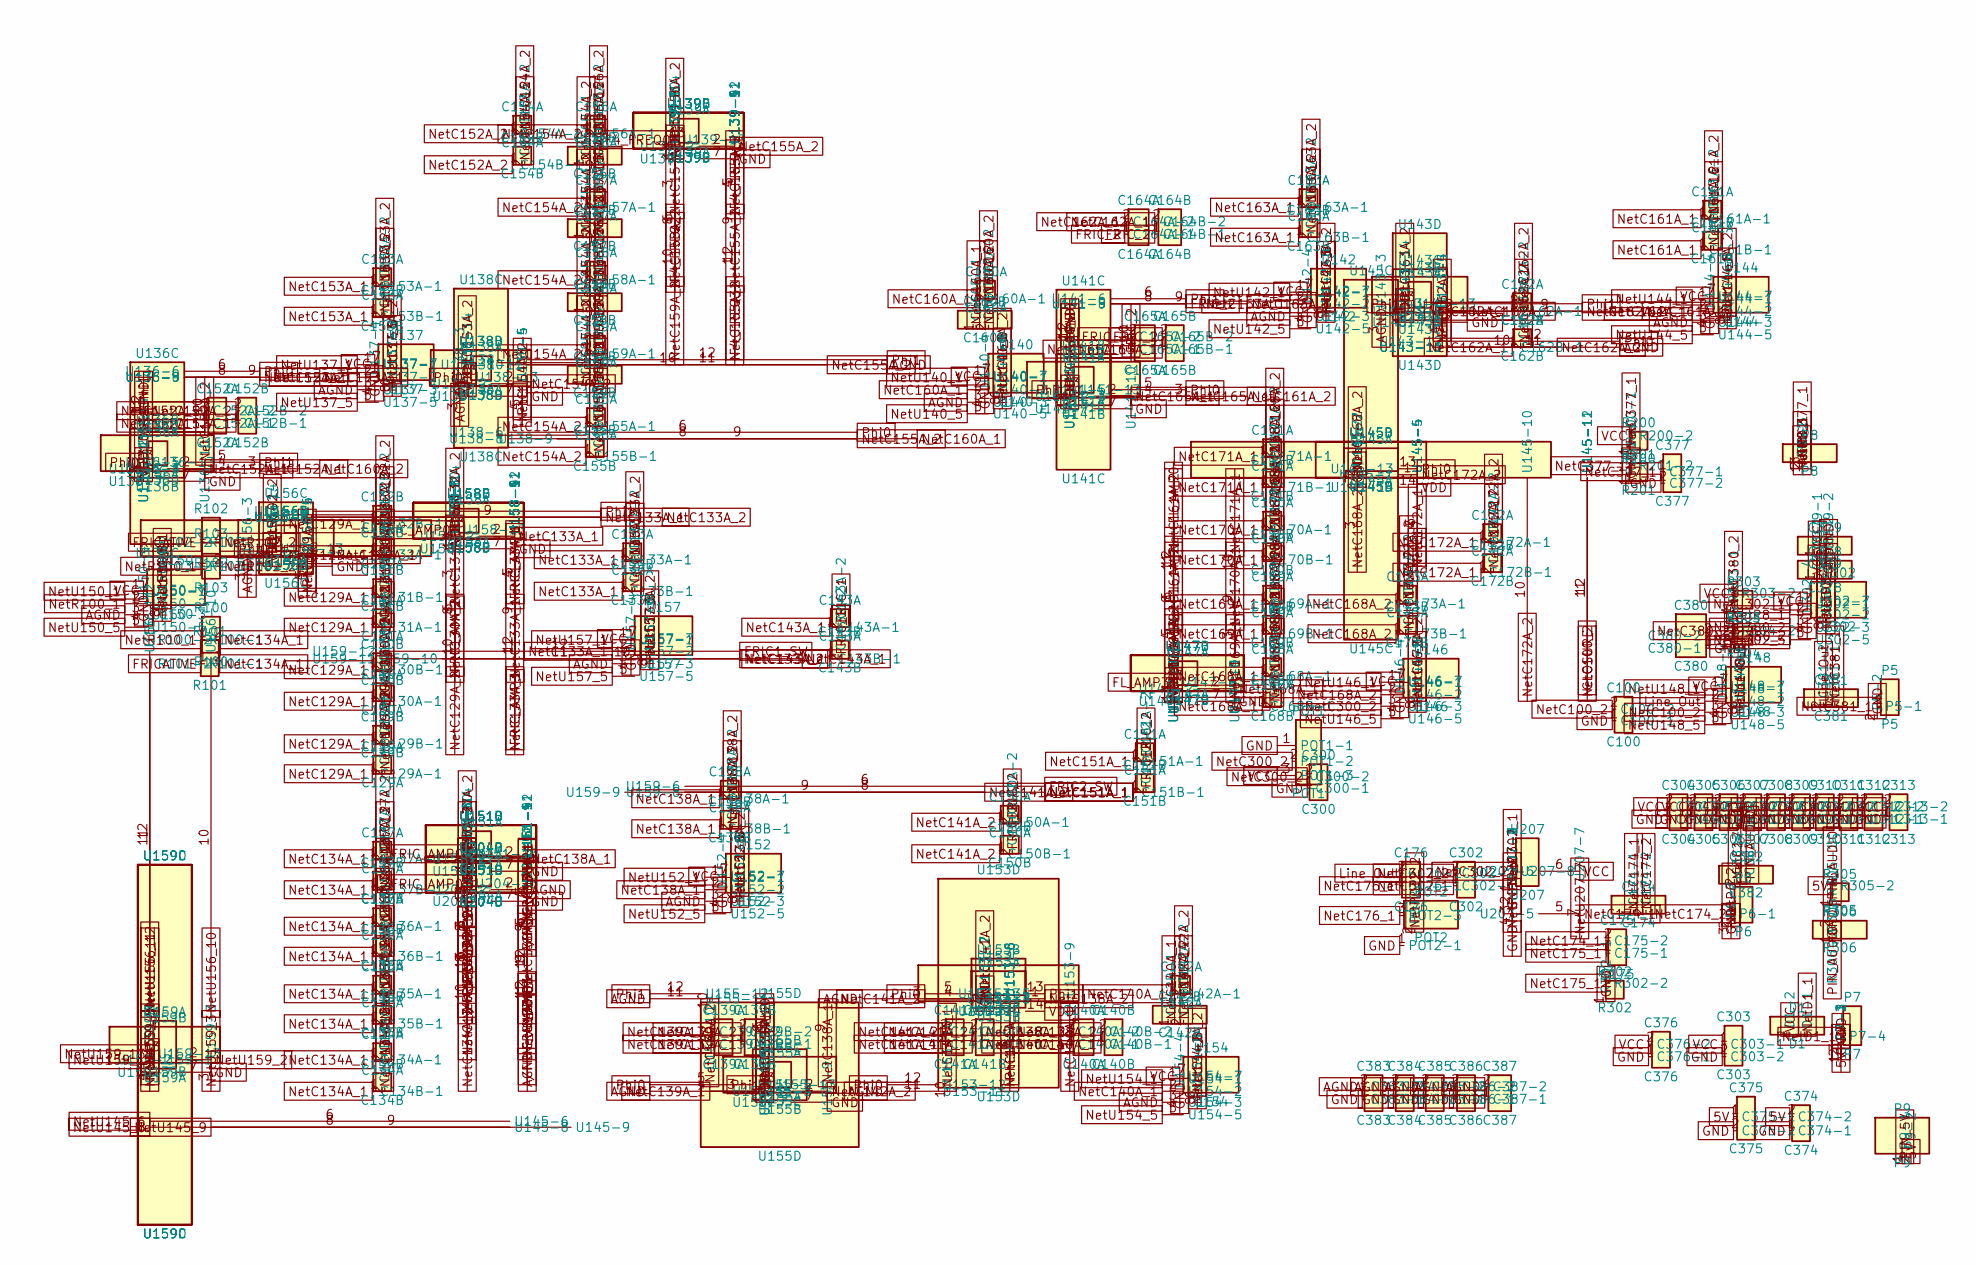
[picture p50: schematic sc02_sheet_02_analog_2_schdoc.kicad_sch]

Parts:
C100: C100
C129A: C129A
C129B: C129B
C130A: C130A
C130B: C130B
C131A: C131A
C131B: C131B
C132A: C132A
C132B: C132B
C133A: C133A
C133B: C133B
C134A: C134A
C134B: C134B
C135A: C135A
C135B: C135B
C136A: C136A
C136B: C136B
C137A: C137A
C137B: C137B
C138A: C138A
C138B: C138B
C139A: C139A
C139B: C139B
C140A: C140A
C140B: C140B
C141A: C141A
C141B: C141B
C142A: C142A
C142B: C142B
C143A: C143A
C143B: C143B
C150A: C150A
C150B: C150B
C151A: C151A
C151B: C151B
C152A: C152A
C152B: C152B
C153A: C153A
C153B: C153B
C154A: C154A
C154B: C154B
C155A: C155A
C155B: C155B
C156A: C156A
C156B: C156B
C157A: C157A
C157B: C157B
C158A: C158A
C158B: C158B
C159A: C159A
C159B: C159B
C160A: C160A
C160B: C160B
C161A: C161A
C161B: C161B
C162A: C162A
C162B: C162B
C163A: C163A
C163B: C163B
C164A: C164A
C164B: C164B
C165A: C165A
C165B: C165B
C168A: C168A
C168B: C168B
C169A: C169A
C169B: C169B
C170A: C170A
C170B: C170B
C171A: C171A
C171B: C171B
C172A: C172A
C172B: C172B
C173A: C173A
C173B: C173B
C174: C174
C175: C175
C176: C176
C300: C300
C302: C302
C303: C303
C304: C304
C305: C305
C306: C306
C307: C307
C308: C308
C309: C309
C310: C310
C311: C311
C312: C312
C313: C313
C374: C374
C375: C375
C376: C376
C377: C377
C378: C378
C379: C379
C380: C380
C381: C381
C382: C382
C383: C383
C384: C384
C385: C385
C386: C386
C387: C387
D1: D1
P5: P5
P6: P6
P7: P7
P8: P8
P9: P9
POT1: POT1
POT2: POT2
R100: R100
R101: R101
R102: R102
R103: R103
R200: R200
R201: R201
R302: R302
R303: R303
R304: R304
R305: R305
R306: R306
U136A: U136A
U136B: U136B
U136C: U136C
U136D: U136D
U137: U137
U138A: U138A
U138B: U138B
U138C: U138C
U138D: U138D
U139A: U139A
U139B: U139B
U139C: U139C
U139D: U139D
U140: U140
U141A: U141A
U141B: U141B
U141C: U141C
U141D: U141D
U142: U142
U143A: U143A
U143B: U143B
U143C: U143C
U143D: U143D
U144: U144
U145A: U145A
U145B: U145B
U145C: U145C
U145D: U145D
U146: U146
U147A: U147A
U147B: U147B
U147C: U147C
U147D: U147D
U148: U148
U150: U150
U151A: U151A
U151B: U151B
U151C: U151C
U151D: U151D
U152: U152
U153A: U153A
U153B: U153B
U153C: U153C
U153D: U153D
U154: U154
U155A: U155A
U155B: U155B
U155C: U155C
U155D: U155D
U156A: U156A
U156B: U156B
U156C: U156C
U156D: U156D
U157: U157
U158A: U158A
U158B: U158B
U158C: U158C
U158D: U158D
U159A: U159A
U159B: U159B
U159C: U159C
U159D: U159D
U204A: U204A
U204B: U204B
U204C: U204C
U204D: U204D
U207: U207
U302: U302

Connections:
5V: C374.2 (C374-2), C375.1 (C375-1), P7.1 (P7-1), P9.2 (P9-2), R305.2 (R305-2)
/FRIC_AMP0: U204A.13 (U204-13)
/FRIC_AMP1: U204B.5 (U204-5)
/FRIC_AMP2: U204C.6 (U204-6)
/FRIC_AMP3: U204D.12 (U204-12)
AGND: C383.2 (C383-2), C384.2 (C384-2), C385.2 (C385-2), C386.2 (C386-2), C387.2 (C387-2), P8.2 (P8-2), U136D.11 (U136-11), U137.3 (U137-3), U138B.3 (U138-3), U138D.11 (U138-11), U140.3 (U140-3), U141D.11 (U141-11), U142.3 (U142-3), U143B.3 (U143-3), U143D.11 (U143-11), U144.3 (U144-3), U150.3 (U150-3), U152.3 (U152-3), U153B.3 (U153-3), U153D.11 (U153-11), U154.3 (U154-3), U155B.4 (U155-4), U155D.11 (U155-11), U156B.3 (U156-3), U157.3 (U157-3), U204A.2 (U204-2), U204B.4 (U204-4), U204C.9 (U204-9), U204D.11 (U204-11)
CLOSURE: U145D.12 (U145-12)
F3_OUT: U136A.1 (U136-1)
F4_FREQ0: U139A.13 (U139-13)
F4_FREQ1: U139B.5 (U139-5)
F4_FREQ2: U139C.6 (U139-6)
F4_FREQ3: U139D.12 (U139-12)
FL_AMP0: U147D.12 (U147-12)
FL_AMP1: U147C.6 (U147-6)
FL_AMP2: U147B.5 (U147-5)
FL_AMP3: U147A.13 (U147-13)
FRIC1_SW: U159D.12 (U159-12)
FRIC2_SW: U159C.6 (U159-6)
FRICATIVE: R101.1 (R101-1), R102.1 (R102-1)
FRIC_1: C143A.2 (C143A-2), C143B.2 (C143B-2)
FRIC_2: C150A.2 (C150A-2), C150B.2 (C150B-2), C151A.2 (C151A-2), C151B.2 (C151B-2), C164A.1 (C164A-1), C164B.1 (C164B-1), C165A.2 (C165A-2), C165B.2 (C165B-2), U141C.8 (U141-8), U141D.10 (U141-10)
FRIC_AMP0: U151A.13 (U151-13), U158A.13 (U158-13)
FRIC_AMP1: U151B.5 (U151-5), U158B.5 (U158-5)
FRIC_AMP2: U151C.6 (U151-6), U158C.6 (U158-6)
FRIC_AMP3: U151D.12 (U151-12), U158D.12 (U158-12)
GND: C100.1 (C100-1), C300.1 (C300-1), C303.2 (C303-2), C304.1 (C304-1), C305.1 (C305-1), C306.1 (C306-1), C307.1 (C307-1), C308.1 (C308-1), C309.1 (C309-1), C310.1 (C310-1), C311.1 (C311-1), C312.1 (C312-1), C313.1 (C313-1), C374.1 (C374-1), C375.2 (C375-2), C376.1 (C376-1), C377.2 (C377-2), C378.2 (C378-2), C379.2 (C379-2), C380.1 (C380-1), C383.1 (C383-1), C384.1 (C384-1), C385.1 (C385-1), C386.1 (C386-1), C387.1 (C387-1), P5.2 (P5-2), P6.3 (P6-3), P7.2 (P7-2), P7.3 (P7-3), POT1.1 (POT1-1), POT2.1 (POT2-1), R201.1 (R201-1), R302.1 (R302-1), R304.1 (R304-1), R306.1 (R306-1), U136A.7 (U136-7), U137.4 (U137-4), U138A.7 (U138-7), U139A.7 (U139-7), U140.4 (U140-4), U141A.7 (U141-7), U142.4 (U142-4), U143A.7 (U143-7), U144.4 (U144-4), U145A.7 (U145-7), U146.4 (U146-4), U147A.7 (U147-7), U148.4 (U148-4), U150.4 (U150-4), U151A.7 (U151-7), U152.4 (U152-4), U153A.7 (U153-7), U154.4 (U154-4), U155A.7 (U155-7), U156A.7 (U156-7), U157.4 (U157-4), U158A.7 (U158-7), U159A.7 (U159-7), U204A.7 (U204-7), U207.2 (U207-2), U207.4 (U207-4), U302.4 (U302-4)
Line Out: C176.2 (C176-2), C381.2 (C381-2), U148.2 (U148-2), U148.6 (U148-6)
NetC100_2: C100.2 (C100-2), U145D.11 (U145-11), U148.3 (U148-3)
NetC129A_1: C129A.1 (C129A-1), C129B.1 (C129B-1), C130A.1 (C130A-1), C130B.1 (C130B-1), C131A.1 (C131A-1), C131B.1 (C131B-1), C132A.1 (C132A-1), C132B.1 (C132B-1), U156A.2 (U156-2), U156B.4 (U156-4)
NetC129A_2: C129A.2 (C129A-2), C129B.2 (C129B-2), U158D.10 (U158-10)
NetC130A_2: C130A.2 (C130A-2), C130B.2 (C130B-2), U158C.8 (U158-8)
NetC131A_2: C131A.2 (C131A-2), C131B.2 (C131B-2), U158B.3 (U158-3)
NetC132A_2: C132A.2 (C132A-2), C132B.2 (C132B-2), U158A.1 (U158-1)
NetC133A_1: C133A.1 (C133A-1), C133B.1 (C133B-1), U156C.8 (U156-8), U157.2 (U157-2), U158A.2 (U158-2), U158B.4 (U158-4), U158C.9 (U158-9), U158D.11 (U158-11)
NetC133A_2: C133A.2 (C133A-2), C133B.2 (C133B-2), U156C.9 (U156-9), U157.6 (U157-6), U159D.11 (U159-11)
NetC134A_1: C134A.1 (C134A-1), C134B.1 (C134B-1), C135A.1 (C135A-1), C135B.1 (C135B-1), C136A.1 (C136A-1), C136B.1 (C136B-1), C137A.1 (C137A-1), C137B.1 (C137B-1), R100.2 (R100-2), R101.2 (R101-2)
NetC134A_2: C134A.2 (C134A-2), C134B.2 (C134B-2), U151D.10 (U151-10), U204D.10 (U204-10)
NetC135A_2: C135A.2 (C135A-2), C135B.2 (C135B-2), U151C.8 (U151-8), U204C.8 (U204-8)
NetC136A_2: C136A.2 (C136A-2), C136B.2 (C136B-2), U151B.3 (U151-3), U204B.3 (U204-3)
NetC137A_2: C137A.2 (C137A-2), C137B.2 (C137B-2), U151A.1 (U151-1), U204A.1 (U204-1)
NetC138A_1: C138A.1 (C138A-1), C138B.1 (C138B-1), U151A.2 (U151-2), U151B.4 (U151-4), U151C.9 (U151-9), U151D.11 (U151-11), U152.2 (U152-2), U155C.9 (U155-9)
NetC138A_2: C138A.2 (C138A-2), C138B.2 (C138B-2), C140A.2 (C140A-2), C140B.2 (C140B-2), U152.6 (U152-6), U153A.1 (U153-1)
NetC139A_1: C139A.1 (C139A-1), C139B.1 (C139B-1), U155A.1 (U155-1), U155B.3 (U155-3)
NetC139A_2: C139A.2 (C139A-2), C139B.2 (C139B-2), U155C.8 (U155-8), U155D.10 (U155-10)
NetC140A_1: C140A.1 (C140A-1), C140B.1 (C140B-1), C142A.1 (C142A-1), C142B.1 (C142B-1), U153C.9 (U153-9), U154.2 (U154-2)
NetC141A_1: C141A.1 (C141A-1), C141B.1 (C141B-1), U153C.8 (U153-8), U153D.10 (U153-10)
NetC141A_2: C141A.2 (C141A-2), C141B.2 (C141B-2), C150A.1 (C150A-1), C150B.1 (C150B-1), U153A.2 (U153-2), U153B.4 (U153-4), U159C.9 (U159-9)
NetC142A_2: C142A.2 (C142A-2), C142B.2 (C142B-2), U154.6 (U154-6), U155A.2 (U155-2)
NetC143A_1: C143A.1 (C143A-1), C143B.1 (C143B-1), U159D.10 (U159-10)
NetC151A_1: C151A.1 (C151A-1), C151B.1 (C151B-1), U159C.8 (U159-8)
NetC152A_1: C152A.1 (C152A-1), C152B.1 (C152B-1), U136A.2 (U136-2), U136B.4 (U136-4)
NetC152A_2: C152A.2 (C152A-2), C152B.2 (C152B-2), C154A.1 (C154A-1), C154B.1 (C154B-1), U136C.8 (U136-8), U136D.10 (U136-10)
NetC153A_1: C153A.1 (C153A-1), C153B.1 (C153B-1), U136C.9 (U136-9), U137.2 (U137-2)
NetC153A_2: C153A.2 (C153A-2), C153B.2 (C153B-2), U137.6 (U137-6), U138A.1 (U138-1)
NetC154A_2: C154A.2 (C154A-2), C154B.2 (C154B-2), C155A.1 (C155A-1), C155B.1 (C155B-1), C156A.1 (C156A-1), C156B.1 (C156B-1), C157A.1 (C157A-1), C157B.1 (C157B-1), C158A.1 (C158A-1), C158B.1 (C158B-1), C159A.1 (C159A-1), C159B.1 (C159B-1), U138A.2 (U138-2), U138B.4 (U138-4)
NetC155A_2: C155A.2 (C155A-2), C155B.2 (C155B-2), U138C.8 (U138-8), U138D.10 (U138-10), U139A.2 (U139-2), U139B.4 (U139-4), U139C.9 (U139-9), U139D.11 (U139-11)
NetC156A_2: C156A.2 (C156A-2), C156B.2 (C156B-2), U139A.1 (U139-1)
NetC157A_2: C157A.2 (C157A-2), C157B.2 (C157B-2), U139B.3 (U139-3)
NetC158A_2: C158A.2 (C158A-2), C158B.2 (C158B-2), U139C.8 (U139-8)
NetC159A_2: C159A.2 (C159A-2), C159B.2 (C159B-2), U139D.10 (U139-10)
NetC160A_1: C160A.1 (C160A-1), C160B.1 (C160B-1), U138C.9 (U138-9), U140.2 (U140-2)
NetC160A_2: C160A.2 (C160A-2), C160B.2 (C160B-2), U136B.3 (U136-3), U140.6 (U140-6), U141A.1 (U141-1)
NetC161A_1: C161A.1 (C161A-1), C161B.1 (C161B-1), U143C.9 (U143-9), U144.2 (U144-2)
NetC161A_2: C161A.2 (C161A-2), C161B.2 (C161B-2), U141B.3 (U141-3), U144.6 (U144-6), U147A.1 (U147-1), U147B.4 (U147-4), U147C.8 (U147-8), U147D.11 (U147-11)
NetC162A_1: C162A.1 (C162A-1), C162B.1 (C162B-1), C164A.2 (C164A-2), C164B.2 (C164B-2), U143A.2 (U143-2), U143B.4 (U143-4)
NetC162A_2: C162A.2 (C162A-2), C162B.2 (C162B-2), U143C.8 (U143-8), U143D.10 (U143-10)
NetC163A_1: C163A.1 (C163A-1), C163B.1 (C163B-1), U141C.9 (U141-9), U142.2 (U142-2)
NetC163A_2: C163A.2 (C163A-2), C163B.2 (C163B-2), U142.6 (U142-6), U143A.1 (U143-1)
NetC165A_1: C165A.1 (C165A-1), C165B.1 (C165B-1), U141A.2 (U141-2), U141B.4 (U141-4)
NetC168A_1: C168A.1 (C168A-1), C168B.1 (C168B-1), U147A.2 (U147-2)
NetC168A_2: C168A.2 (C168A-2), C168B.2 (C168B-2), C169A.2 (C169A-2), C169B.2 (C169B-2), C170A.2 (C170A-2), C170B.2 (C170B-2), C171A.2 (C171A-2), C171B.2 (C171B-2), C173A.1 (C173A-1), C173B.1 (C173B-1), U145A.2 (U145-2), U145B.3 (U145-3), U146.2 (U146-2)
NetC169A_1: C169A.1 (C169A-1), C169B.1 (C169B-1), U147B.3 (U147-3)
NetC170A_1: C170A.1 (C170A-1), C170B.1 (C170B-1), U147C.9 (U147-9)
NetC171A_1: C171A.1 (C171A-1), C171B.1 (C171B-1), U147D.10 (U147-10)
NetC172A_1: C172A.1 (C172A-1), C172B.1 (C172B-1), U145B.4 (U145-4)
NetC172A_2: C172A.2 (C172A-2), C172B.2 (C172B-2), C173A.2 (C173A-2), C173B.2 (C173B-2), U145A.1 (U145-1), U145D.10 (U145-10), U146.6 (U146-6)
NetC174_1: C174.1 (C174-1), C175.2 (C175-2), C382.2 (C382-2), U207.5 (U207-5)
NetC174_2: C174.2 (C174-2), P6.1 (P6-1)
NetC175_1: C175.1 (C175-1), R302.2 (R302-2)
NetC176_1: C176.1 (C176-1), POT2.3 (POT2-3)
NetC300_2: C300.2 (C300-2), POT1.2 (POT1-2), U146.3 (U146-3)
NetC302_1: C302.1 (C302-1), U207.1 (U207-1)
NetC302_2: C302.2 (C302-2), U207.8 (U207-8)
NetC377_1: C377.1 (C377-1), P8.3 (P8-3), R200.1 (R200-1), R201.2 (R201-2)
NetC380_2: C380.2 (C380-2), R303.1 (R303-1), R304.2 (R304-2), U302.3 (U302-3)
NetC381_1: C381.1 (C381-1), P5.1 (P5-1)
NetD1_1: D1.1 (D1-1), P7.4 (P7-4)
NetP6_2: P6.2 (P6-2)
NetP8_1: P8.1 (P8-1), U302.2 (U302-2), U302.6 (U302-6)
NetPOT2_2: POT2.2 (POT2-2), U207.3 (U207-3)
NetR100_1: R100.1 (R100-1), R103.1 (R103-1), U150.2 (U150-2), U150.6 (U150-6)
NetR102_2: R102.2 (R102-2), R103.2 (R103-2), U156A.1 (U156-1)
NetU137_1: U137.1 (U137-1)
NetU137_5: U137.5 (U137-5)
NetU137_8: U137.8 (U137-8)
NetU140_1: U140.1 (U140-1)
NetU140_5: U140.5 (U140-5)
NetU140_8: U140.8 (U140-8)
NetU142_1: U142.1 (U142-1)
NetU142_5: U142.5 (U142-5)
NetU142_8: U142.8 (U142-8)
NetU144_1: U144.1 (U144-1)
NetU144_5: U144.5 (U144-5)
NetU144_8: U144.8 (U144-8)
NetU145_6: U145C.6 (U145-6)
NetU145_8: U145C.8 (U145-8)
NetU145_9: U145C.9 (U145-9)
NetU146_1: U146.1 (U146-1)
NetU146_5: U146.5 (U146-5)
NetU146_8: U146.8 (U146-8)
NetU148_1: U148.1 (U148-1)
NetU148_5: U148.5 (U148-5)
NetU148_8: U148.8 (U148-8)
NetU150_1: U150.1 (U150-1)
NetU150_5: U150.5 (U150-5)
NetU150_8: U150.8 (U150-8)
NetU152_1: U152.1 (U152-1)
NetU152_5: U152.5 (U152-5)
NetU152_8: U152.8 (U152-8)
NetU154_1: U154.1 (U154-1)
NetU154_5: U154.5 (U154-5)
NetU154_8: U154.8 (U154-8)
NetU156_10: U156D.10 (U156-10)
NetU156_11: U156D.11 (U156-11)
NetU156_12: U156D.12 (U156-12)
NetU157_1: U157.1 (U157-1)
NetU157_5: U157.5 (U157-5)
NetU157_8: U157.8 (U157-8)
NetU159_1: U159A.1 (U159-1)
NetU159_2: U159A.2 (U159-2)
NetU159_3: U159B.3 (U159-3)
NetU159_4: U159B.4 (U159-4)
NetU159_5: U159B.5 (U159-5)
NetU159_13: U159A.13 (U159-13)
NetU207_7: U207.7 (U207-7)
NetU302_1: U302.1 (U302-1)
NetU302_5: U302.5 (U302-5)
NetU302_8: U302.8 (U302-8)
PIN_5V: P9.1 (P9-1)
PIN_AUDIO: C382.1 (C382-1), R305.1 (R305-1), R306.2 (R306-2)
Phi0: U136A.13 (U136-13), U136C.6 (U136-6), U138A.13 (U138-13), U138C.6 (U138-6), U141B.5 (U141-5), U141D.12 (U141-12), U143B.5 (U143-5), U143D.12 (U143-12), U145A.13 (U145-13), U153B.5 (U153-5), U153D.12 (U153-12), U155B.5 (U155-5), U155C.6 (U155-6), U156A.13 (U156-13)
Phi1: U136B.5 (U136-5), U136D.12 (U136-12), U138B.5 (U138-5), U138D.12 (U138-12), U141A.13 (U141-13), U141C.6 (U141-6), U143A.13 (U143-13), U143C.6 (U143-6), U145B.5 (U145-5), U153A.13 (U153-13), U153C.6 (U153-6), U155A.13 (U155-13), U155D.12 (U155-12), U156B.5 (U156-5), U156C.6 (U156-6)
VCC: C303.1 (C303-1), C304.2 (C304-2), C305.2 (C305-2), C306.2 (C306-2), C307.2 (C307-2), C308.2 (C308-2), C309.2 (C309-2), C310.2 (C310-2), C311.2 (C311-2), C312.2 (C312-2), C313.2 (C313-2), C376.2 (C376-2), C378.1 (C378-1), C379.1 (C379-1), D1.2 (D1-2), POT1.3 (POT1-3), R200.2 (R200-2), R303.2 (R303-2), U137.7 (U137-7), U140.7 (U140-7), U142.7 (U142-7), U144.7 (U144-7), U146.7 (U146-7), U148.7 (U148-7), U150.7 (U150-7), U152.7 (U152-7), U154.7 (U154-7), U157.7 (U157-7), U207.6 (U207-6), U302.7 (U302-7)
VDD: U136A.14 (U136-14), U138A.14 (U138-14), U139A.14 (U139-14), U141A.14 (U141-14), U143A.14 (U143-14), U145A.14 (U145-14), U147A.14 (U147-14), U151A.14 (U151-14), U153A.14 (U153-14), U155A.14 (U155-14), U156A.14 (U156-14), U158A.14 (U158-14), U159A.14 (U159-14), U204A.14 (U204-14)
