hasseily/appletini-one/schematics/sc02_prototype/kicad/sc02_sheet_03_digital_1_schdoc.kicad_sch

## KiCad design schematics/sc02_prototype/kicad/sc02_sheet_03_digital_1_schdoc.kicad_sch (2026-08-26)

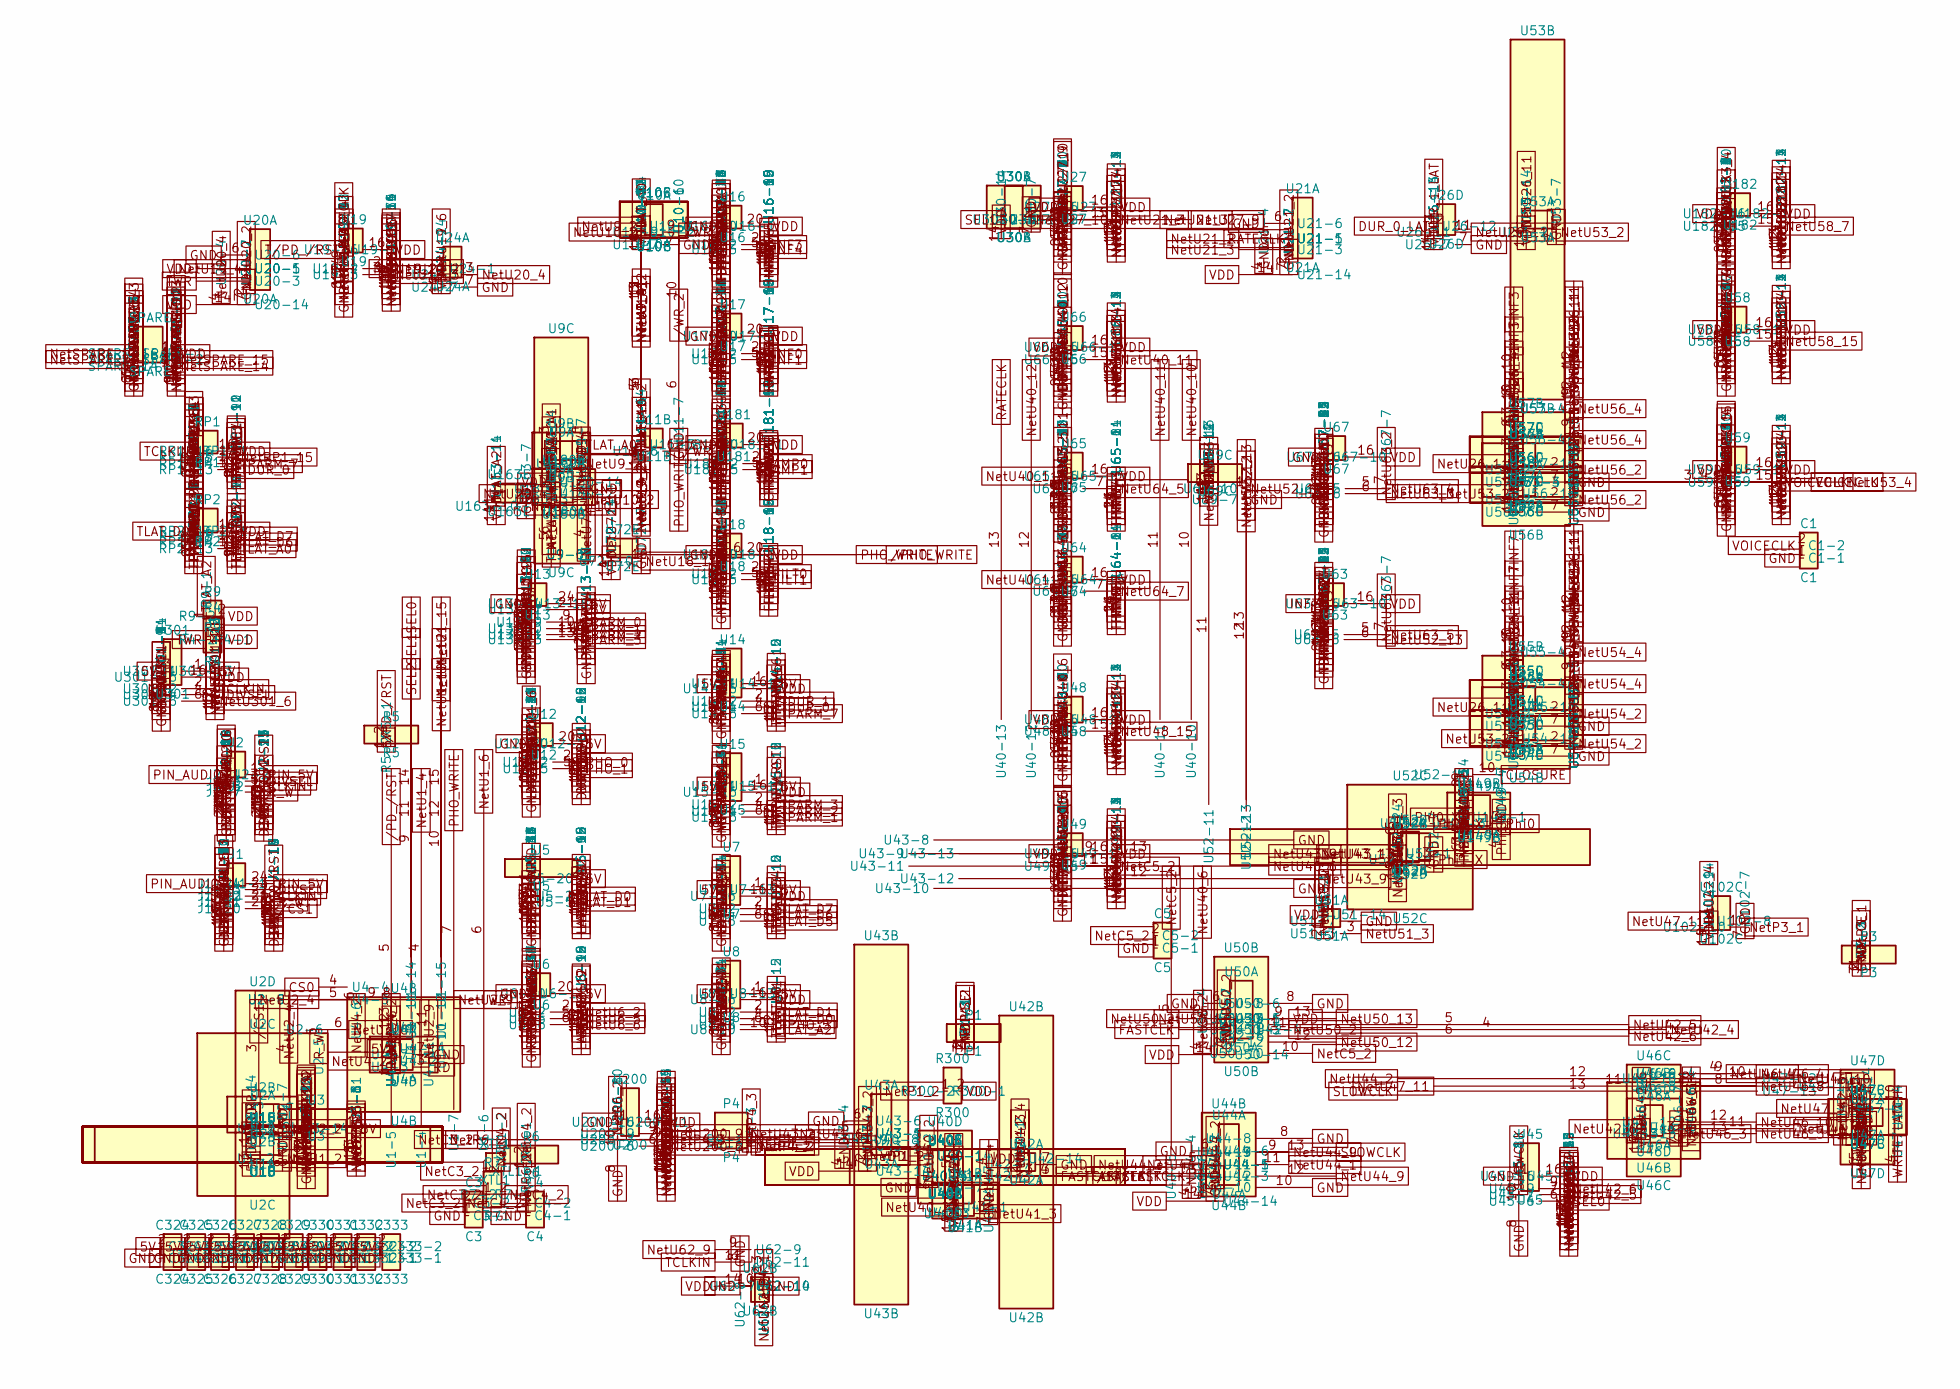
[picture p51: schematic sc02_sheet_03_digital_1_schdoc.kicad_sch]

Parts:
C1: C1
C3: C3
C4: C4
C5: C5
C324: C324
C325: C325
C326: C326
C327: C327
C328: C328
C329: C329
C330: C330
C331: C331
C332: C332
C333: C333
J1: J1
J2: J2
P1: P1
P3: P3
P4: P4
R4: R4
R5: R5
R6: R6
R7: R7
R9: R9
R300: R300
RP1: RP1
RP2: RP2
SPARE: SPARE
U1A: U1A
U1B: U1B
U1C: U1C
U1D: U1D
U1E: U1E
U1F: U1F
U2A: U2A
U2B: U2B
U2C: U2C
U2D: U2D
U3: U3
U4A: U4A
U4B: U4B
U4D: U4D
U5: U5
U6: U6
U7: U7
U8: U8
U9A: U9A
U9B: U9B
U9C: U9C
U10A: U10A
U10B: U10B
U10C: U10C
U11B: U11B
U12: U12
U13: U13
U14: U14
U15: U15
U16: U16
U17: U17
U18: U18
U19: U19
U20A: U20A
U21A: U21A
U24A: U24A
U26D: U26D
U27: U27
U30A: U30A
U30B: U30B
U40A: U40A
U40B: U40B
U40C: U40C
U40D: U40D
U40E: U40E
U40F: U40F
U41A: U41A
U41B: U41B
U42A: U42A
U42B: U42B
U43A: U43A
U43B: U43B
U44A: U44A
U44B: U44B
U45: U45
U46A: U46A
U46B: U46B
U46C: U46C
U46D: U46D
U47A: U47A
U47B: U47B
U47C: U47C
U47D: U47D
U48: U48
U49: U49
U50A: U50A
U50B: U50B
U51A: U51A
U52A: U52A
U52B: U52B
U52C: U52C
U52D: U52D
U53A: U53A
U53B: U53B
U54A: U54A
U54B: U54B
U54C: U54C
U54D: U54D
U55A: U55A
U55B: U55B
U55C: U55C
U55D: U55D
U56A: U56A
U56B: U56B
U56C: U56C
U56D: U56D
U57A: U57A
U57B: U57B
U57C: U57C
U57D: U57D
U58: U58
U59: U59
U62B: U62B
U63: U63
U64: U64
U65: U65
U66: U66
U67: U67
U69C: U69C
U72E: U72E
U102C: U102C
U149A: U149A
U149B: U149B
U163E: U163E
U180A: U180A
U180B: U180B
U181: U181
U182: U182
U200: U200
U301: U301
XTL1: XTL1

Connections:
5V: C324.2 (C324-2), C325.2 (C325-2), C326.2 (C326-2), C327.2 (C327-2), C328.2 (C328-2), C329.2 (C329-2), C330.2 (C330-2), C331.2 (C331-2), C332.2 (C332-2), C333.2 (C333-2), R5.2 (R5-2), U1A.1 (U1-1), U2A.14 (U2-14), U3.14 (U3-14), U4A.14 (U4-14), U5.20 (U5-20), U6.20 (U6-20), U7.1 (U7-1), U7.13 (U7-13), U8.1 (U8-1), U8.13 (U8-13), U12.20 (U12-20), U13.21 (U13-21), U13.24 (U13-24), U14.1 (U14-1), U14.13 (U14-13), U15.1 (U15-1), U15.13 (U15-13), U301.1 (U301-1), U301.13 (U301-13)
/CS1: J1.20 (J1-20), J2.9 (J2-9), U2B.3 (U2-3)
/FASTCLK: U19.9 (U19-9), U40B.4 (U40-4), U44A.3 (U44-3), U48.2 (U48-2), U49.2 (U49-2)
/PD_/RST: J1.18 (J1-18), J2.13 (J2-13), R5.1 (R5-1), U1B.5 (U1-5)
/PHO_WRITE: U9C.6 (U9-6)
/WR_1: U10A.9 (U10-9), U16.11 (U16-11)
/WR_2: U10C.10 (U10-10), U17.11 (U17-11)
/WR_3: U11B.6 (U11-6), U181.11 (U181-11)
A/R: J1.4 (J1-4), J2.8 (J2-8)
AMP0: U181.2 (U181-2)
AMP1: U181.5 (U181-5)
AMP2: U181.6 (U181-6)
AMP3: U181.9 (U181-9)
CLKIN: J1.22 (J1-22), J2.5 (J2-5), U301.3 (U301-3)
CLOSURE: U52C.10 (U52-10)
CS0: J1.19 (J1-19), J2.11 (J2-11), U4B.4 (U4-4)
CTRL: U181.19 (U181-19)
D0: J1.9 (J1-9), J2.18 (J2-18), U5.3 (U5-3)
D1: J1.10 (J1-10), J2.20 (J2-20), U5.4 (U5-4)
D2: J1.11 (J1-11), J2.22 (J2-22), U5.7 (U5-7)
D3: J1.13 (J1-13), J2.23 (J2-23), U5.8 (U5-8)
D4: J1.14 (J1-14), J2.21 (J2-21), U5.13 (U5-13)
D5: J1.15 (J1-15), J2.19 (J2-19), U5.14 (U5-14)
D6: J1.16 (J1-16), J2.17 (J2-17), U5.17 (U5-17)
D7: J1.17 (J1-17), J2.15 (J2-15), U3.3 (U3-3), U5.18 (U5-18)
DIVSEL: J1.23 (J1-23), J2.3 (J2-3), U301.5 (U301-5)
DONE_RB: U1A.3 (U1-3)
DUR_0: U12.16 (U12-16), U14.5 (U14-5)
DUR_0_LAT: U26D.12 (U26-12)
DUR_1: U12.19 (U12-19), U14.3 (U14-3)
DUR_1_LAT: U26D.13 (U26-13)
FASTCLK: U40B.3 (U40-3), U42A.3 (U42-3), U50A.3 (U50-3)
FILT0: U18.2 (U18-2), U48.3 (U48-3)
FILT1: U18.5 (U18-5), U48.4 (U48-4)
FILT2: U18.6 (U18-6), U48.5 (U48-5)
FILT3: U18.9 (U18-9), U48.6 (U48-6)
FILT4: U18.12 (U18-12), U49.3 (U49-3)
FILT5: U18.15 (U18-15), U49.4 (U49-4)
FILT6: U18.16 (U18-16), U49.5 (U49-5)
FILT7: U18.19 (U18-19), U49.6 (U49-6)
GND: C1.1 (C1-1), C3.1 (C3-1), C4.1 (C4-1), C5.1 (C5-1), C324.1 (C324-1), C325.1 (C325-1), C326.1 (C326-1), C327.1 (C327-1), C328.1 (C328-1), C329.1 (C329-1), C330.1 (C330-1), C331.1 (C331-1), C332.1 (C332-1), C333.1 (C333-1), J1.2 (J1-2), J1.12 (J1-12), J2.4 (J2-4), J2.24 (J2-24), P1.3 (P1-3), P3.3 (P3-3), SPARE.8 (SPARE-8), U1A.8 (U1-8), U2A.7 (U2-7), U3.7 (U3-7), U4A.7 (U4-7), U5.1 (U5-1), U5.10 (U5-10), U6.1 (U6-1), U6.10 (U6-10), U7.8 (U7-8), U8.8 (U8-8), U9A.7 (U9-7), U10A.7 (U10-7), U11B.7 (U11-7), U12.1 (U12-1), U12.10 (U12-10), U13.12 (U13-12), U13.18 (U13-18), U13.19 (U13-19), U13.20 (U13-20), U13.22 (U13-22), U14.8 (U14-8), U15.8 (U15-8), U16.1 (U16-1), U16.10 (U16-10), U17.1 (U17-1), U17.10 (U17-10), U18.1 (U18-1), U18.10 (U18-10), U19.8 (U19-8), U20A.6 (U20-6), U20A.7 (U20-7), U21A.4 (U21-4), U21A.6 (U21-6), U21A.7 (U21-7), U24A.7 (U24-7), U26D.7 (U26-7), U27.8 (U27-8), U30A.7 (U30-7), U40A.7 (U40-7), U41A.7 (U41-7), U42A.7 (U42-7), U43A.4 (U43-4), U43A.6 (U43-6), U43A.7 (U43-7), U43B.8 (U43-8), U43B.10 (U43-10), U44A.4 (U44-4), U44A.6 (U44-6), U44A.7 (U44-7), U44B.8 (U44-8), U44B.10 (U44-10), U45.8 (U45-8), U45.11 (U45-11), U46A.7 (U46-7), U47A.7 (U47-7), U48.8 (U48-8), U49.8 (U49-8), U50A.6 (U50-6), U50A.7 (U50-7), U50B.8 (U50-8), U51A.7 (U51-7), U52A.7 (U52-7), U53A.7 (U53-7), U54A.7 (U54-7), U55A.7 (U55-7), U56A.7 (U56-7), U57A.7 (U57-7), U58.8 (U58-8), U59.8 (U59-8), U62B.7 (U62-7), U62B.8 (U62-8), U62B.10 (U62-10), U63.8 (U63-8), U64.1 (U64-1), U64.3 (U64-3), U64.4 (U64-4), U64.8 (U64-8), U64.12 (U64-12), U64.13 (U64-13), U65.1 (U65-1), U65.3 (U65-3), U65.4 (U65-4), U65.8 (U65-8), U65.12 (U65-12), U65.13 (U65-13), U66.8 (U66-8), U67.2 (U67-2), U67.4 (U67-4), U67.8 (U67-8), U67.9 (U67-9), U67.10 (U67-10), U67.11 (U67-11), U67.12 (U67-12), U67.13 (U67-13), U67.14 (U67-14), U69C.7 (U69-7), U72E.7 (U72-7), U102C.7 (U102-7), U149A.7 (U149-7), U163E.7 (U163-7), U180A.7 (U180-7), U181.1 (U181-1), U181.10 (U181-10), U182.8 (U182-8), U200.8 (U200-8), U200.11 (U200-11), U301.7 (U301-7), U301.8 (U301-8), U301.9 (U301-9), U301.11 (U301-11), U301.14 (U301-14)
INF0: U17.2 (U17-2), U182.3 (U182-3)
INF1: U17.5 (U17-5), U182.4 (U182-4)
INF2: U17.6 (U17-6), U182.5 (U182-5)
INF3: U16.2 (U16-2), U56D.10 (U56-10), U66.3 (U66-3)
INF4: U16.5 (U16-5), U56C.8 (U56-8), U66.4 (U66-4)
INF5: U16.6 (U16-6), U56B.3 (U56-3), U66.5 (U66-5)
INF6: U16.9 (U16-9), U56A.1 (U56-1), U67.15 (U67-15)
INF7: U16.12 (U16-12), U54D.10 (U54-10), U63.10 (U63-10)
INF8: U16.15 (U16-15), U54C.8 (U54-8), U63.12 (U63-12)
INF9: U16.16 (U16-16), U54B.3 (U54-3), U63.13 (U63-13)
INF10: U16.19 (U16-19), U54A.1 (U54-1), U63.15 (U63-15)
INF11: U17.9 (U17-9), U59.6 (U59-6)
LATCH: U47C.10 (U47-10)
LAT_A0: U6.16 (U6-16), U8.14 (U8-14)
LAT_A1: U6.19 (U6-19), U8.11 (U8-11)
LAT_A2: U6.15 (U6-15), U8.9 (U8-9)
LAT_D0: U5.2 (U5-2), U8.5 (U8-5), U12.3 (U12-3)
LAT_D1: U5.5 (U5-5), U8.3 (U8-3), U12.4 (U12-4)
LAT_D2: U5.6 (U5-6), U7.14 (U7-14), U12.7 (U12-7)
LAT_D3: U5.9 (U5-9), U7.11 (U7-11), U12.8 (U12-8)
LAT_D4: U5.12 (U5-12), U7.9 (U7-9), U12.13 (U12-13)
LAT_D5: U5.15 (U5-15), U7.7 (U7-7), U12.14 (U12-14)
LAT_D6: U5.16 (U5-16), U7.5 (U7-5), U12.17 (U12-17)
LAT_D7: U5.19 (U5-19), U7.3 (U7-3), U12.18 (U12-18)
NetC3_2: C3.2 (C3-2), R7.1 (R7-1), U40D.9 (U40-9), XTL1.1 (XTL1-1)
NetC4_2: C4.2 (C4-2), R6.1 (R6-1), R7.2 (R7-2), XTL1.2 (XTL1-2)
NetC5_2: C5.2 (C5-2), U40C.5 (U40-5), U49.15 (U49-15), U50A.4 (U50-4), U50B.10 (U50-10), U51A.1 (U51-1), U52C.9 (U52-9)
NetJ1_3: J1.3 (J1-3)
NetJ1_5: J1.5 (J1-5)
NetJ2_6: J2.6 (J2-6)
NetJ2_10: J2.10 (J2-10)
NetP1_2: P1.2 (P1-2), R300.1 (R300-1), U40A.1 (U40-1), U41B.5 (U41-5)
NetP3_1: P3.1 (P3-1), U102C.10 (U102-10)
NetP4_1: P4.1 (P4-1), U62B.13 (U62-13)
NetP4_2: P4.2 (P4-2), U41A.2 (U41-2), U43A.3 (U43-3)
NetP4_3: P4.3 (P4-3), U200.7 (U200-7)
NetR6_2: R6.2 (R6-2), U40D.8 (U40-8), U200.10 (U200-10)
NetRP1_3: RP1.3 (RP1-3)
NetRP1_4: RP1.4 (RP1-4)
NetRP1_5: RP1.5 (RP1-5)
NetRP1_6: RP1.6 (RP1-6)
NetRP1_7: RP1.7 (RP1-7)
NetRP1_15: RP1.15 (RP1-15)
NetSPARE_1: SPARE.1 (SPARE-1)
NetSPARE_2: SPARE.2 (SPARE-2)
NetSPARE_3: SPARE.3 (SPARE-3)
NetSPARE_4: SPARE.4 (SPARE-4)
NetSPARE_5: SPARE.5 (SPARE-5)
NetSPARE_6: SPARE.6 (SPARE-6)
NetSPARE_7: SPARE.7 (SPARE-7)
NetSPARE_9: SPARE.9 (SPARE-9)
NetSPARE_10: SPARE.10 (SPARE-10)
NetSPARE_11: SPARE.11 (SPARE-11)
NetSPARE_12: SPARE.12 (SPARE-12)
NetSPARE_13: SPARE.13 (SPARE-13)
NetSPARE_14: SPARE.14 (SPARE-14)
NetSPARE_15: SPARE.15 (SPARE-15)
NetU1_2: U1A.2 (U1-2), U3.2 (U3-2)
NetU1_4: U1B.4 (U1-4), U15.11 (U15-11)
NetU1_6: U1C.6 (U1-6), U12.11 (U12-11)
NetU1_10: U1D.10 (U1-10), U13.6 (U13-6)
NetU1_12: U1E.12 (U1-12), U13.7 (U13-7)
NetU1_15: U1F.15 (U1-15), U13.8 (U13-8)
NetU2_2: U2A.2 (U2-2), U3.1 (U3-1)
NetU2_4: U2B.4 (U2-4), U4B.5 (U4-5)
NetU2_6: U2C.6 (U2-6), U4D.12 (U4-12)
NetU2_9: U2D.9 (U2-9), U4D.11 (U4-11)
NetU3_4: U3.4 (U3-4)
NetU3_5: U3.5 (U3-5)
NetU3_6: U3.6 (U3-6)
NetU3_8: U3.8 (U3-8)
NetU3_9: U3.9 (U3-9)
NetU3_10: U3.10 (U3-10)
NetU3_11: U3.11 (U3-11)
NetU3_12: U3.12 (U3-12)
NetU3_13: U3.13 (U3-13)
NetU4_2: U4A.2 (U4-2), U4B.6 (U4-6), U4D.13 (U4-13)
NetU6_2: U6.2 (U6-2)
NetU6_3: U6.3 (U6-3)
NetU6_4: U6.4 (U6-4)
NetU6_5: U6.5 (U6-5)
NetU6_6: U6.6 (U6-6)
NetU6_7: U6.7 (U6-7)
NetU6_8: U6.8 (U6-8)
NetU6_9: U6.9 (U6-9)
NetU6_12: U6.12 (U6-12)
NetU6_13: U6.13 (U6-13)
NetU9_2: U9A.2 (U9-2), U10A.1 (U10-1), U10B.3 (U10-3)
NetU9_4: U9B.4 (U9-4), U10B.5 (U10-5), U10C.13 (U10-13)
NetU10_2: U10A.2 (U10-2), U10B.4 (U10-4), U10C.12 (U10-12), U11B.4 (U11-4), U180A.3 (U180-3)
NetU18_11: U18.11 (U18-11), U72E.10 (U72-10)
NetU19_2: U19.2 (U19-2), U19.5 (U19-5), U24A.1 (U24-1)
NetU19_3: U19.3 (U19-3)
NetU19_4: U19.4 (U19-4), U20A.1 (U20-1)
NetU19_6: U19.6 (U19-6), U24A.2 (U24-2)
NetU19_7: U19.7 (U19-7)
NetU19_10: U19.10 (U19-10)
NetU19_11: U19.11 (U19-11)
NetU19_12: U19.12 (U19-12)
NetU19_13: U19.13 (U19-13)
NetU19_14: U19.14 (U19-14)
NetU19_15: U19.15 (U19-15)
NetU20_2: U20A.2 (U20-2)
NetU20_4: U20A.4 (U20-4), U24A.3 (U24-3), U180A.2 (U180-2), U180B.6 (U180-6)
NetU21_2: U21A.2 (U21-2), U21A.5 (U21-5)
NetU21_3: U21A.3 (U21-3), U27.15 (U27-15), U30B.3 (U30-3)
NetU26_11: U26D.11 (U26-11), U53A.1 (U53-1), U55A.13 (U55-13), U55B.5 (U55-5), U55C.6 (U55-6), U55D.12 (U55-12), U57A.13 (U57-13), U57B.5 (U57-5), U57C.6 (U57-6), U57D.12 (U57-12)
NetU27_9: U27.9 (U27-9), U30B.4 (U30-4)
NetU27_10: U27.10 (U27-10), U30A.2 (U30-2)
NetU27_11: U27.11 (U27-11)
NetU27_12: U27.12 (U27-12)
NetU27_13: U27.13 (U27-13)
NetU27_14: U27.14 (U27-14)
NetU40_2: U40A.2 (U40-2), U41A.1 (U41-1)
NetU40_6: U40C.6 (U40-6), U43B.11 (U43-11), U48.9 (U48-9), U49.9 (U49-9)
NetU40_10: U40E.10 (U40-10), U66.9 (U66-9)
NetU40_11: U40E.11 (U40-11), U64.15 (U64-15), U65.15 (U65-15), U66.15 (U66-15)
NetU40_12: U40F.12 (U40-12), U66.10 (U66-10)
NetU41_3: U41A.3 (U41-3), U42A.1 (U42-1)
NetU41_4: U41B.4 (U41-4), U42A.2 (U42-2)
NetU41_6: U41B.6 (U41-6), U43A.1 (U43-1)
NetU42_4: U42B.4 (U42-4), U102C.9 (U102-9)
NetU42_5: U42B.5 (U42-5), U45.7 (U45-7), U47A.1 (U47-1), U47A.2 (U47-2), U47B.5 (U47-5)
NetU42_6: U42B.6 (U42-6), U45.9 (U45-9), U46A.1 (U46-1), U46A.2 (U46-2)
NetU43_2: U43A.2 (U43-2), U43A.5 (U43-5)
NetU43_9: U43B.9 (U43-9), U43B.12 (U43-12), U52B.5 (U52-5)
NetU43_13: U43B.13 (U43-13), U52A.1 (U52-1), U52C.8 (U52-8)
NetU44_1: U44A.1 (U44-1), U44B.11 (U44-11)
NetU44_2: U44A.2 (U44-2), U44A.5 (U44-5), U47D.12 (U47-12)
NetU44_9: U44B.9 (U44-9), U44B.12 (U44-12)
NetU45_1: U45.1 (U45-1)
NetU45_2: U45.2 (U45-2)
NetU45_4: U45.4 (U45-4)
NetU45_12: U45.12 (U45-12)
NetU45_13: U45.13 (U45-13)
NetU45_14: U45.14 (U45-14)
NetU45_15: U45.15 (U45-15)
NetU46_3: U46A.3 (U46-3), U46B.5 (U46-5), U46D.13 (U46-13)
NetU46_4: U46B.4 (U46-4), U46C.9 (U46-9)
NetU46_8: U46C.8 (U46-8), U46D.11 (U46-11), U47B.6 (U47-6), U47C.9 (U47-9)
NetU46_10: U46C.10 (U46-10), U46D.12 (U46-12)
NetU47_3: U47A.3 (U47-3), U47C.8 (U47-8)
NetU47_11: U47D.11 (U47-11), U102C.8 (U102-8)
NetU48_11: U48.11 (U48-11)
NetU48_12: U48.12 (U48-12)
NetU48_13: U48.13 (U48-13)
NetU48_14: U48.14 (U48-14)
NetU48_15: U48.15 (U48-15), U49.7 (U49-7), U49.10 (U49-10)
NetU49_11: U49.11 (U49-11)
NetU49_12: U49.12 (U49-12)
NetU49_13: U49.13 (U49-13)
NetU49_14: U49.14 (U49-14)
NetU50_1: U50A.1 (U50-1)
NetU50_2: U50A.2 (U50-2), U50A.5 (U50-5), U50B.11 (U50-11)
NetU50_12: U50B.12 (U50-12)
NetU50_13: U50B.13 (U50-13), U51A.2 (U51-2)
NetU51_3: U51A.3 (U51-3), U52A.2 (U52-2), U52B.6 (U52-6)
NetU52_11: U52D.11 (U52-11), U65.5 (U65-5)
NetU52_12: U52D.12 (U52-12), U69C.10 (U69-10)
NetU52_13: U52D.13 (U52-13), U63.6 (U63-6)
NetU53_2: U53A.2 (U53-2), U54A.13 (U54-13), U54B.5 (U54-5), U54C.6 (U54-6), U54D.12 (U54-12), U56A.13 (U56-13), U56B.5 (U56-5), U56C.6 (U56-6), U56D.12 (U56-12)
NetU53_4: U53B.4 (U53-4), U58.9 (U58-9), U59.9 (U59-9), U182.9 (U182-9)
NetU54_2: U54A.2 (U54-2), U55A.2 (U55-2), U59.5 (U59-5)
NetU54_4: U54B.4 (U54-4), U55B.4 (U55-4), U59.4 (U59-4)
NetU54_9: U54C.9 (U54-9), U55C.9 (U55-9), U59.3 (U59-3)
NetU54_11: U54D.11 (U54-11), U55D.11 (U55-11), U58.6 (U58-6)
NetU56_2: U56A.2 (U56-2), U57A.2 (U57-2), U58.5 (U58-5)
NetU56_4: U56B.4 (U56-4), U57B.4 (U57-4), U58.4 (U58-4)
NetU56_9: U56C.9 (U56-9), U57C.9 (U57-9), U58.3 (U58-3)
NetU56_11: U56D.11 (U56-11), U57D.11 (U57-11), U182.6 (U182-6)
NetU58_7: U58.7 (U58-7), U58.10 (U58-10), U182.15 (U182-15)
NetU58_11: U58.11 (U58-11)
NetU58_12: U58.12 (U58-12)
NetU58_13: U58.13 (U58-13)
NetU58_14: U58.14 (U58-14)
NetU58_15: U58.15 (U58-15), U59.7 (U59-7), U59.10 (U59-10)
NetU59_11: U59.11 (U59-11)
NetU59_12: U59.12 (U59-12)
NetU59_13: U59.13 (U59-13)
NetU59_14: U59.14 (U59-14)
NetU62_9: U62B.9 (U62-9), U62B.12 (U62-12)
NetU63_2: U63.2 (U63-2), U67.7 (U67-7)
NetU63_3: U63.3 (U63-3), U67.6 (U67-6)
NetU63_4: U63.4 (U63-4), U67.5 (U67-5)
NetU63_5: U63.5 (U63-5), U64.10 (U64-10), U65.10 (U65-10)
NetU63_7: U63.7 (U63-7)
NetU64_5: U64.5 (U64-5), U65.7 (U65-7)
NetU64_7: U64.7 (U64-7)
NetU66_11: U66.11 (U66-11)
NetU66_12: U66.12 (U66-12)
NetU66_13: U66.13 (U66-13)
NetU66_14: U66.14 (U66-14)
NetU72_11: U72E.11 (U72-11), U180B.4 (U180-4)
NetU163_10: U163E.10 (U163-10), U180A.1 (U180-1)
NetU182_11: U182.11 (U182-11)
NetU182_12: U182.12 (U182-12)
NetU182_13: U182.13 (U182-13)
NetU182_14: U182.14 (U182-14)
NetU200_1: U200.1 (U200-1)
NetU200_2: U200.2 (U200-2)
NetU200_3: U200.3 (U200-3)
NetU200_4: U200.4 (U200-4)
NetU200_5: U200.5 (U200-5)
NetU200_6: U200.6 (U200-6)
NetU200_9: U200.9 (U200-9)
NetU200_12: U200.12 (U200-12)
NetU200_13: U200.13 (U200-13)
NetU200_14: U200.14 (U200-14)
NetU200_15: U200.15 (U200-15)
NetU301_6: U301.6 (U301-6)
NetU301_10: U301.10 (U301-10)
NetU301_12: U301.12 (U301-12)
NetU301_15: U301.15 (U301-15)
PARM_0: U13.9 (U13-9), U15.9 (U15-9)
PARM_1: U13.10 (U13-10), U15.7 (U15-7)
PARM_2: U13.11 (U13-11), U15.5 (U15-5)
PARM_3: U13.13 (U13-13), U15.3 (U15-3)
PARM_4: U13.14 (U13-14), U14.14 (U14-14)
PARM_5: U13.15 (U13-15), U14.11 (U14-11)
PARM_6: U13.16 (U13-16), U14.9 (U14-9)
PARM_7: U13.17 (U13-17), U14.7 (U14-7)
PHO_0: U12.2 (U12-2), U13.5 (U13-5)
PHO_1: U12.5 (U12-5), U13.4 (U13-4)
PHO_2: U12.6 (U12-6), U13.3 (U13-3)
PHO_3: U12.9 (U12-9), U13.2 (U13-2)
PHO_4: U12.12 (U12-12), U13.1 (U13-1)
PHO_5: U8.7 (U8-7), U12.15 (U12-15), U13.23 (U13-23)
PHO_WRITE: U1C.7 (U1-7), U9C.5 (U9-5), U10B.6 (U10-6)
PIN_5V: J1.24 (J1-24), J2.1 (J2-1)
PIN_AUDIO: J1.1 (J1-1), J2.2 (J2-2)
Phi0: U149A.3 (U149-3)
Phi0_X: U52B.4 (U52-4), U149A.1 (U149-1), U149A.2 (U149-2)
Phi1: U149B.4 (U149-4)
Phi1_X: U52A.3 (U52-3), U149B.5 (U149-5), U149B.6 (U149-6)
RAM_CE: P3.2 (P3-2)
RATE0: U17.12 (U17-12), U27.3 (U27-3)
RATE1: U17.15 (U17-15), U27.4 (U27-4)
RATE2: U17.16 (U17-16), U27.5 (U27-5)
RATE3: U17.19 (U17-19), U27.6 (U27-6)
RATECLK: U21A.1 (U21-1), U40F.13 (U40-13), U66.2 (U66-2)
RD: U2A.1 (U2-1), U4A.3 (U4-3)
RS0: J1.8 (J1-8), J2.16 (J2-16), U6.17 (U6-17)
RS1: J1.7 (J1-7), J2.14 (J2-14), U6.18 (U6-18)
RS2: J1.6 (J1-6), J2.12 (J2-12), U6.14 (U6-14)
R_W: J1.21 (J1-21), J2.7 (J2-7), U2C.5 (U2-5), U4A.1 (U4-1)
SEL0: U1F.14 (U1-14), U45.6 (U45-6)
SEL1: U1E.11 (U1-11), U27.2 (U27-2), U30A.1 (U30-1), U45.5 (U45-5)
SEL2: U1D.9 (U1-9), U45.3 (U45-3)
SLOWCLK: U44B.13 (U44-13), U45.10 (U45-10), U46B.6 (U46-6), U47D.13 (U47-13), U58.2 (U58-2), U59.2 (U59-2), U182.2 (U182-2)
T/PD_/RST: RP2.3 (RP2-3), U15.12 (U15-12), U19.1 (U19-1)
TCLKIN: RP1.1 (RP1-1), U62B.11 (U62-11), U301.2 (U301-2)
TDIVSEL: P1.1 (P1-1), RP1.2 (RP1-2), U301.4 (U301-4)
TDUR_0: RP1.13 (RP1-13), U14.4 (U14-4)
TDUR_1: RP1.12 (RP1-12), U14.2 (U14-2)
TINF3: U57D.10 (U57-10), U65.6 (U65-6), U69C.13 (U69-13)
TINF4: U57C.8 (U57-8), U65.11 (U65-11), U69C.12 (U69-12)
TINF5: U57B.3 (U57-3), U65.14 (U65-14), U69C.11 (U69-11)
TINF6: U57A.1 (U57-1), U65.2 (U65-2), U67.1 (U67-1)
TINF7: U55D.10 (U55-10), U63.9 (U63-9), U64.6 (U64-6)
TINF8: U55C.8 (U55-8), U63.11 (U63-11), U64.11 (U64-11)
TINF9: U55B.3 (U55-3), U63.14 (U63-14), U64.14 (U64-14)
TINF10: U55A.1 (U55-1), U63.1 (U63-1), U64.2 (U64-2)
TLAT_A0: RP2.13 (RP2-13), U8.15 (U8-15), U9B.3 (U9-3), U10A.8 (U10-8), U11B.3 (U11-3)
TLAT_A1: RP2.4 (RP2-4), U8.12 (U8-12), U9A.1 (U9-1), U10C.11 (U10-11), U11B.5 (U11-5)
TLAT_A2: R9.1 (R9-1), U8.10 (U8-10), U163E.11 (U163-11), U180B.5 (U180-5)
TLAT_D0: RP2.1 (RP2-1), U8.4 (U8-4), U16.3 (U16-3), U17.3 (U17-3), U18.3 (U18-3), U181.3 (U181-3)
TLAT_D1: RP2.2 (RP2-2), U8.2 (U8-2), U16.4 (U16-4), U17.4 (U17-4), U18.4 (U18-4), U181.4 (U181-4)
TLAT_D2: RP2.12 (RP2-12), U7.15 (U7-15), U16.7 (U16-7), U17.7 (U17-7), U18.7 (U18-7), U181.7 (U181-7)
TLAT_D3: RP2.10 (RP2-10), U7.12 (U7-12), U16.8 (U16-8), U17.8 (U17-8), U18.8 (U18-8), U181.8 (U181-8)
TLAT_D4: RP2.9 (RP2-9), U7.10 (U7-10), U16.13 (U16-13), U17.13 (U17-13), U18.13 (U18-13), U181.13 (U181-13)
TLAT_D5: RP2.11 (RP2-11), U7.6 (U7-6), U16.14 (U16-14), U17.14 (U17-14), U18.14 (U18-14), U181.14 (U181-14)
TLAT_D6: RP2.14 (RP2-14), U7.4 (U7-4), U16.17 (U16-17), U17.17 (U17-17), U18.17 (U18-17), U181.17 (U181-17)
TLAT_D7: RP2.15 (RP2-15), U7.2 (U7-2), U16.18 (U16-18), U17.18 (U17-18), U18.18 (U18-18), U181.18 (U181-18)
TPARM_0: RP2.8 (RP2-8), U15.10 (U15-10)
TPARM_1: RP2.7 (RP2-7), U15.6 (U15-6)
TPARM_2: RP2.6 (RP2-6), U15.4 (U15-4)
TPARM_3: RP2.5 (RP2-5), U15.2 (U15-2)
TPARM_4: RP1.11 (RP1-11), U14.15 (U14-15)
TPARM_5: RP1.10 (RP1-10), U14.12 (U14-12)
TPARM_6: RP1.9 (RP1-9), U14.10 (U14-10)
TPARM_7: RP1.14 (RP1-14), U14.6 (U14-6)
TPHO_5: RP1.8 (RP1-8), U8.6 (U8-6)
TRANS0: U181.12 (U181-12)
TRANS1: U181.15 (U181-15)
TRANS2: U181.16 (U181-16)
TWR: R4.1 (R4-1), U15.15 (U15-15), U20A.3 (U20-3)
VDD: R4.2 (R4-2), R9.2 (R9-2), R300.2 (R300-2), RP1.16 (RP1-16), RP2.16 (RP2-16), SPARE.16 (SPARE-16), U7.16 (U7-16), U8.16 (U8-16), U9A.14 (U9-14), U10A.14 (U10-14), U11B.14 (U11-14), U14.16 (U14-16), U15.16 (U15-16), U16.20 (U16-20), U17.20 (U17-20), U18.20 (U18-20), U19.16 (U19-16), U20A.5 (U20-5), U20A.14 (U20-14), U21A.14 (U21-14), U24A.14 (U24-14), U26D.14 (U26-14), U27.1 (U27-1), U27.7 (U27-7), U27.16 (U27-16), U30A.14 (U30-14), U40A.14 (U40-14), U41A.14 (U41-14), U42A.14 (U42-14), U43A.14 (U43-14), U44A.14 (U44-14), U45.16 (U45-16), U46A.14 (U46-14), U47A.14 (U47-14), U48.1 (U48-1), U48.7 (U48-7), U48.10 (U48-10), U48.16 (U48-16), U49.1 (U49-1), U49.16 (U49-16), U50A.14 (U50-14), U50B.9 (U50-9), U51A.14 (U51-14), U52A.14 (U52-14), U53A.14 (U53-14), U54A.14 (U54-14), U55A.14 (U55-14), U56A.14 (U56-14), U57A.14 (U57-14), U58.1 (U58-1), U58.16 (U58-16), U59.1 (U59-1), U59.16 (U59-16), U62B.14 (U62-14), U63.16 (U63-16), U64.9 (U64-9), U64.16 (U64-16), U65.9 (U65-9), U65.16 (U65-16), U66.1 (U66-1), U66.6 (U66-6), U66.7 (U66-7), U66.16 (U66-16), U67.3 (U67-3), U67.16 (U67-16), U69C.14 (U69-14), U72E.14 (U72-14), U102C.14 (U102-14), U149A.14 (U149-14), U163E.14 (U163-14), U180A.14 (U180-14), U181.20 (U181-20), U182.1 (U182-1), U182.7 (U182-7), U182.10 (U182-10), U182.16 (U182-16), U200.16 (U200-16), U301.16 (U301-16)
VOICECLK: C1.2 (C1-2), U53B.3 (U53-3), U59.15 (U59-15)
WR: U2D.8 (U2-8), U5.11 (U5-11), U6.11 (U6-11), U15.14 (U15-14)
WRITE: U47B.4 (U47-4)
