hasseily/appletini-one/schematics/sc02_prototype/kicad/sc02_sheet_04_digital_2_schdoc.kicad_sch

## KiCad design schematics/sc02_prototype/kicad/sc02_sheet_04_digital_2_schdoc.kicad_sch (2026-08-26)

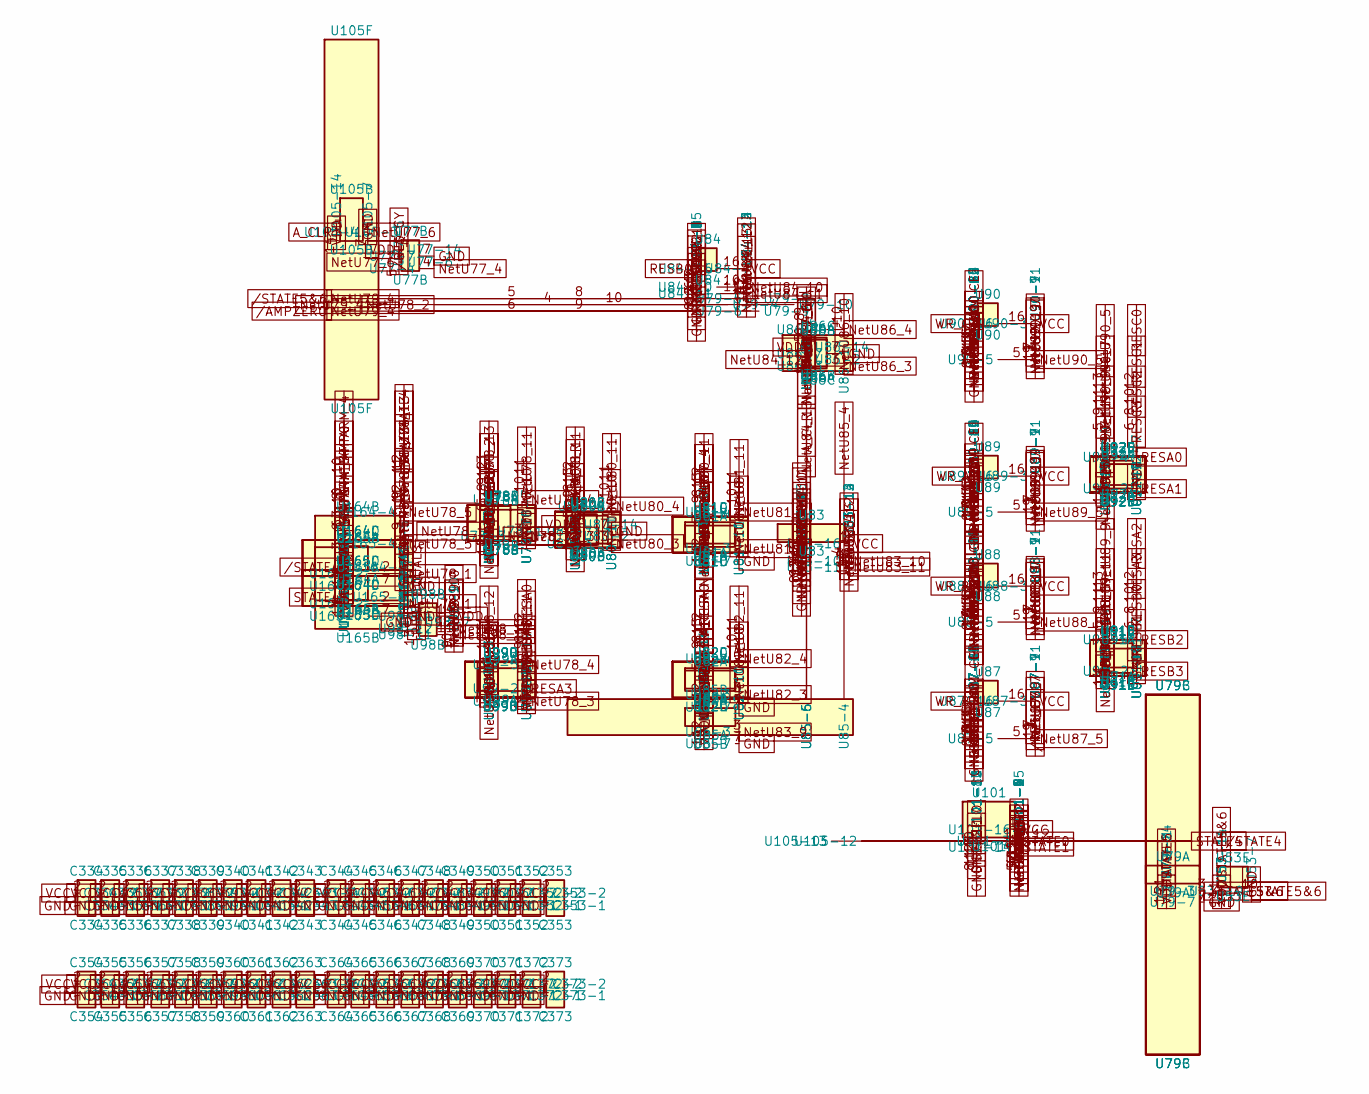
[picture p52: schematic sc02_sheet_04_digital_2_schdoc.kicad_sch]

Parts:
C334: C334
C335: C335
C336: C336
C337: C337
C338: C338
C339: C339
C340: C340
C341: C341
C342: C342
C343: C343
C344: C344
C345: C345
C346: C346
C347: C347
C348: C348
C349: C349
C350: C350
C351: C351
C352: C352
C353: C353
C354: C354
C355: C355
C356: C356
C357: C357
C358: C358
C359: C359
C360: C360
C361: C361
C362: C362
C363: C363
C364: C364
C365: C365
C366: C366
C367: C367
C368: C368
C369: C369
C370: C370
C371: C371
C372: C372
C373: C373
U53E: U53E
U77B: U77B
U78A: U78A
U78B: U78B
U78C: U78C
U78D: U78D
U79A: U79A
U79B: U79B
U79C: U79C
U80A: U80A
U80B: U80B
U80C: U80C
U80D: U80D
U81A: U81A
U81B: U81B
U81C: U81C
U81D: U81D
U82A: U82A
U82B: U82B
U82C: U82C
U82D: U82D
U83: U83
U84: U84
U85A: U85A
U85B: U85B
U86A: U86A
U86B: U86B
U86C: U86C
U87: U87
U88: U88
U89: U89
U90: U90
U91A: U91A
U91B: U91B
U91C: U91C
U91D: U91D
U91E: U91E
U91F: U91F
U92A: U92A
U92B: U92B
U92C: U92C
U92D: U92D
U92E: U92E
U92F: U92F
U98B: U98B
U99A: U99A
U99B: U99B
U99C: U99C
U99D: U99D
U101: U101
U105B: U105B
U105F: U105F
U164A: U164A
U164B: U164B
U164C: U164C
U164D: U164D
U165A: U165A
U165B: U165B
U165C: U165C
U165D: U165D

Connections:
/AMPZERO: U79B.6 (U79-6)
/RES_CY: U77B.5 (U77-5), U87.11 (U87-11)
/STATE4: U105F.12 (U105-12), U164A.13 (U164-13), U164B.5 (U164-5), U164C.6 (U164-6), U164D.12 (U164-12)
/STATE5&6: U53E.11 (U53-11), U79A.3 (U79-3), U79B.5 (U79-5)
AMP0: U165D.10 (U165-10)
AMP1: U165C.8 (U165-8)
AMP2: U165B.3 (U165-3)
AMP3: U165A.1 (U165-1)
A_CLR: U80A.1 (U80-1), U80B.5 (U80-5), U80C.9 (U80-9), U80D.13 (U80-13), U82A.1 (U82-1), U82B.5 (U82-5), U82C.9 (U82-9), U82D.13 (U82-13), U85A.1 (U85-1), U85B.5 (U85-5), U105B.3 (U105-3)
GND: C334.1 (C334-1), C335.1 (C335-1), C336.1 (C336-1), C337.1 (C337-1), C338.1 (C338-1), C339.1 (C339-1), C340.1 (C340-1), C341.1 (C341-1), C342.1 (C342-1), C343.1 (C343-1), C344.1 (C344-1), C345.1 (C345-1), C346.1 (C346-1), C347.1 (C347-1), C348.1 (C348-1), C349.1 (C349-1), C350.1 (C350-1), C351.1 (C351-1), C352.1 (C352-1), C353.1 (C353-1), C354.1 (C354-1), C355.1 (C355-1), C356.1 (C356-1), C357.1 (C357-1), C358.1 (C358-1), C359.1 (C359-1), C360.1 (C360-1), C361.1 (C361-1), C362.1 (C362-1), C363.1 (C363-1), C364.1 (C364-1), C365.1 (C365-1), C366.1 (C366-1), C367.1 (C367-1), C368.1 (C368-1), C369.1 (C369-1), C370.1 (C370-1), C371.1 (C371-1), C372.1 (C372-1), C373.1 (C373-1), U53E.7 (U53-7), U77B.7 (U77-7), U78A.7 (U78-7), U79A.7 (U79-7), U80A.7 (U80-7), U81A.7 (U81-7), U82A.7 (U82-7), U83.8 (U83-8), U84.8 (U84-8), U84.9 (U84-9), U85A.7 (U85-7), U86A.7 (U86-7), U87.4 (U87-4), U87.6 (U87-6), U87.8 (U87-8), U87.10 (U87-10), U87.13 (U87-13), U88.8 (U88-8), U88.13 (U88-13), U89.8 (U89-8), U89.13 (U89-13), U90.8 (U90-8), U90.13 (U90-13), U91A.7 (U91-7), U92A.7 (U92-7), U98B.7 (U98-7), U99A.7 (U99-7), U101.8 (U101-8), U101.11 (U101-11), U105B.7 (U105-7), U164A.7 (U164-7), U165A.7 (U165-7)
NetU77_4: U77B.4 (U77-4), U81A.1 (U81-1), U81B.5 (U81-5), U81C.9 (U81-9), U81D.13 (U81-13)
NetU77_6: U77B.6 (U77-6), U86A.1 (U86-1), U86B.5 (U86-5), U86C.8 (U86-8), U105B.4 (U105-4)
NetU78_1: U78A.1 (U78-1), U164A.2 (U164-2), U165A.2 (U165-2)
NetU78_2: U78A.2 (U78-2), U78B.6 (U78-6), U78C.8 (U78-8), U78D.12 (U78-12), U79C.10 (U79-10)
NetU78_3: U78A.3 (U78-3), U80A.2 (U80-2), U99A.1 (U99-1)
NetU78_4: U78B.4 (U78-4), U80B.6 (U80-6), U99B.5 (U99-5)
NetU78_5: U78B.5 (U78-5), U164B.4 (U164-4), U165B.4 (U165-4)
NetU78_9: U78C.9 (U78-9), U164C.9 (U164-9), U165C.9 (U165-9)
NetU78_10: U78C.10 (U78-10), U80C.8 (U80-8), U99C.9 (U99-9)
NetU78_11: U78D.11 (U78-11), U80D.12 (U80-12), U99D.13 (U99-13)
NetU78_13: U78D.13 (U78-13), U164D.11 (U164-11), U165D.11 (U165-11)
NetU79_4: U79B.4 (U79-4), U79C.8 (U79-8), U79C.9 (U79-9)
NetU80_3: U80A.3 (U80-3), U81A.2 (U81-2)
NetU80_4: U80B.4 (U80-4), U81B.6 (U81-6)
NetU80_10: U80C.10 (U80-10), U81C.8 (U81-8)
NetU80_11: U80D.11 (U80-11), U81D.12 (U81-12)
NetU81_3: U81A.3 (U81-3), U83.1 (U83-1)
NetU81_4: U81B.4 (U81-4), U83.3 (U83-3)
NetU81_10: U81C.10 (U81-10), U83.5 (U83-5)
NetU81_11: U81D.11 (U81-11), U83.7 (U83-7)
NetU82_3: U82A.3 (U82-3), U83.15 (U83-15)
NetU82_4: U82B.4 (U82-4), U83.2 (U83-2)
NetU82_10: U82C.10 (U82-10), U83.4 (U83-4)
NetU82_11: U82D.11 (U82-11), U83.6 (U83-6)
NetU83_9: U83.9 (U83-9), U85A.3 (U85-3)
NetU83_10: U83.10 (U83-10), U88.4 (U88-4), U89.4 (U89-4)
NetU83_11: U83.11 (U83-11), U88.6 (U88-6), U89.6 (U89-6)
NetU83_12: U83.12 (U83-12), U88.10 (U88-10), U89.10 (U89-10)
NetU83_13: U83.13 (U83-13), U88.12 (U88-12), U89.12 (U89-12)
NetU83_14: U83.14 (U83-14), U87.12 (U87-12)
NetU84_10: U84.10 (U84-10), U86C.9 (U86-9)
NetU84_11: U84.11 (U84-11), U86B.6 (U86-6)
NetU84_12: U84.12 (U84-12), U86A.2 (U86-2)
NetU84_13: U84.13 (U84-13), U85B.6 (U85-6)
NetU84_14: U84.14 (U84-14), U85A.2 (U85-2)
NetU85_4: U85B.4 (U85-4), U90.12 (U90-12)
NetU86_3: U86A.3 (U86-3), U90.10 (U90-10)
NetU86_4: U86B.4 (U86-4), U90.6 (U90-6)
NetU86_10: U86C.10 (U86-10), U90.4 (U90-4)
NetU87_5: U87.5 (U87-5)
NetU87_7: U87.7 (U87-7)
NetU87_9: U87.9 (U87-9)
NetU88_5: U88.5 (U88-5), U91D.9 (U91-9)
NetU88_7: U88.7 (U88-7), U91C.5 (U91-5)
NetU88_9: U88.9 (U88-9), U91B.3 (U91-3)
NetU88_11: U88.11 (U88-11), U91A.1 (U91-1)
NetU89_5: U89.5 (U89-5), U92B.3 (U92-3)
NetU89_7: U89.7 (U89-7), U92A.1 (U92-1)
NetU89_9: U89.9 (U89-9), U91F.13 (U91-13)
NetU89_11: U89.11 (U89-11), U91E.11 (U91-11)
NetU90_5: U90.5 (U90-5), U92F.13 (U92-13)
NetU90_7: U90.7 (U90-7), U92E.11 (U92-11)
NetU90_9: U90.9 (U90-9), U92D.9 (U92-9)
NetU90_11: U90.11 (U90-11), U92C.5 (U92-5)
NetU98_9: U98B.9 (U98-9), U99A.3 (U99-3)
NetU98_10: U98B.10 (U98-10), U99B.4 (U99-4)
NetU98_11: U98B.11 (U98-11), U99C.10 (U99-10)
NetU98_12: U98B.12 (U98-12), U99D.11 (U99-11)
NetU101_5: U101.5 (U101-5)
NetU101_9: U101.9 (U101-9)
RAM_CE: U87.2 (U87-2), U88.2 (U88-2), U89.2 (U89-2), U90.2 (U90-2)
RESA0: U82D.12 (U82-12), U92B.4 (U92-4), U99D.12 (U99-12)
RESA1: U82C.8 (U82-8), U92A.2 (U92-2), U99C.8 (U99-8)
RESA2: U82B.6 (U82-6), U91F.12 (U91-12), U99B.6 (U99-6)
RESA3: U82A.2 (U82-2), U91E.10 (U91-10), U99A.2 (U99-2)
RESA_EQUALS: U98B.13 (U98-13)
RESB0: U84.7 (U84-7), U91D.8 (U91-8)
RESB1: U84.5 (U84-5), U91C.6 (U91-6)
RESB2: U84.3 (U84-3), U91B.4 (U91-4)
RESB3: U84.1 (U84-1), U91A.2 (U91-2)
RESC0: U84.6 (U84-6), U92F.12 (U92-12)
RESC1: U84.4 (U84-4), U92E.10 (U92-10)
RESC2: U84.2 (U84-2), U92D.8 (U92-8)
RESC3: U84.15 (U84-15), U92C.6 (U92-6)
SEL0: U87.1 (U87-1), U88.1 (U88-1), U89.1 (U89-1), U90.1 (U90-1), U101.10 (U101-10)
SEL1: U87.15 (U87-15), U88.15 (U88-15), U89.15 (U89-15), U90.15 (U90-15), U101.13 (U101-13)
SEL2: U87.14 (U87-14), U88.14 (U88-14), U89.14 (U89-14), U90.14 (U90-14), U101.12 (U101-12)
STATE0: U101.3 (U101-3)
STATE1: U101.14 (U101-14)
STATE2: U101.2 (U101-2)
STATE3: U101.15 (U101-15)
STATE4: U101.1 (U101-1), U105F.13 (U105-13), U165A.13 (U165-13), U165B.5 (U165-5), U165C.6 (U165-6), U165D.12 (U165-12)
STATE5: U79A.1 (U79-1), U101.6 (U101-6)
STATE5&6: U53E.10 (U53-10)
STATE6: U79A.2 (U79-2), U101.7 (U101-7)
STATE7: U101.4 (U101-4)
TPARM_4: U164D.10 (U164-10)
TPARM_5: U164C.8 (U164-8)
TPARM_6: U164B.3 (U164-3)
TPARM_7: U164A.1 (U164-1)
VCC: C334.2 (C334-2), C335.2 (C335-2), C336.2 (C336-2), C337.2 (C337-2), C338.2 (C338-2), C339.2 (C339-2), C340.2 (C340-2), C341.2 (C341-2), C342.2 (C342-2), C343.2 (C343-2), C344.2 (C344-2), C345.2 (C345-2), C346.2 (C346-2), C347.2 (C347-2), C348.2 (C348-2), C349.2 (C349-2), C350.2 (C350-2), C351.2 (C351-2), C352.2 (C352-2), C353.2 (C353-2), C354.2 (C354-2), C355.2 (C355-2), C356.2 (C356-2), C357.2 (C357-2), C358.2 (C358-2), C359.2 (C359-2), C360.2 (C360-2), C361.2 (C361-2), C362.2 (C362-2), C363.2 (C363-2), C364.2 (C364-2), C365.2 (C365-2), C366.2 (C366-2), C367.2 (C367-2), C368.2 (C368-2), C369.2 (C369-2), C370.2 (C370-2), C371.2 (C371-2), C372.2 (C372-2), C373.2 (C373-2), U83.16 (U83-16), U84.16 (U84-16), U87.16 (U87-16), U88.16 (U88-16), U89.16 (U89-16), U90.16 (U90-16), U101.16 (U101-16)
VDD: U53E.14 (U53-14), U77B.14 (U77-14), U78A.14 (U78-14), U79A.14 (U79-14), U80A.14 (U80-14), U81A.14 (U81-14), U82A.14 (U82-14), U85A.14 (U85-14), U86B.14 (U86-14), U91A.14 (U91-14), U92A.14 (U92-14), U98B.14 (U98-14), U99A.14 (U99-14), U105B.14 (U105-14), U164A.14 (U164-14), U165A.14 (U165-14)
WR_A: U89.3 (U89-3)
WR_B: U87.3 (U87-3), U88.3 (U88-3)
WR_C: U90.3 (U90-3)
