hasseily/appletini-one/schematics/sc02_prototype/kicad/sc02_sheet_05_digital_3_schdoc.kicad_sch

## KiCad design schematics/sc02_prototype/kicad/sc02_sheet_05_digital_3_schdoc.kicad_sch (2026-08-26)

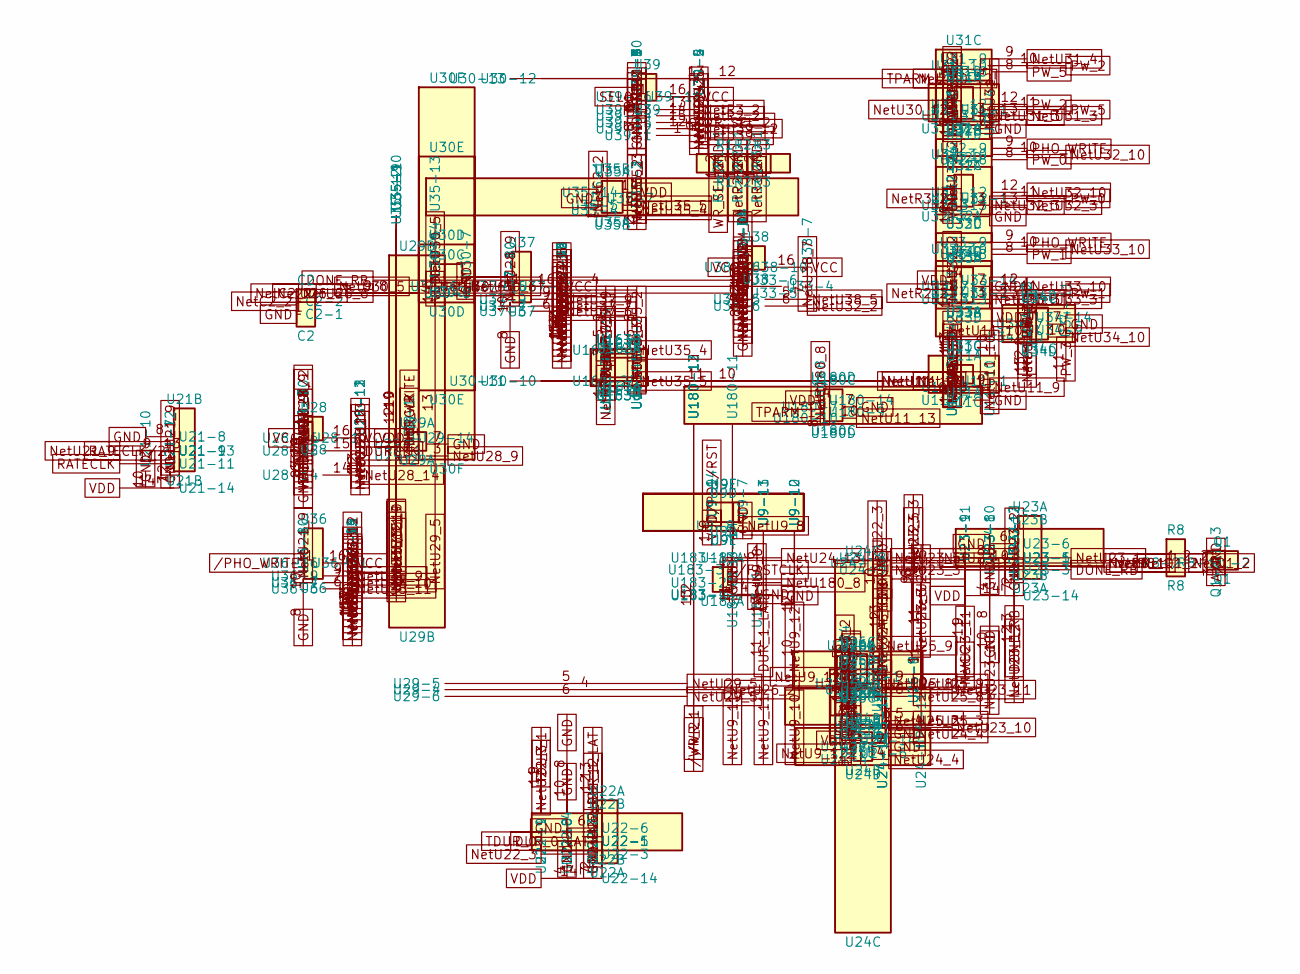
[picture p53: schematic sc02_sheet_05_digital_3_schdoc.kicad_sch]

Parts:
C2: C2
Q1: Q1
R1: R1
R2: R2
R3: R3
R8: R8
U9D: U9D
U9E: U9E
U9F: U9F
U11A: U11A
U11C: U11C
U21B: U21B
U22A: U22A
U22B: U22B
U23A: U23A
U23B: U23B
U24B: U24B
U24C: U24C
U24D: U24D
U25A: U25A
U25B: U25B
U25C: U25C
U25D: U25D
U26A: U26A
U26B: U26B
U26C: U26C
U28: U28
U29A: U29A
U29B: U29B
U30C: U30C
U30D: U30D
U30E: U30E
U30F: U30F
U31A: U31A
U31B: U31B
U31C: U31C
U31D: U31D
U32A: U32A
U32C: U32C
U32D: U32D
U33A: U33A
U33B: U33B
U33C: U33C
U33D: U33D
U34C: U34C
U34D: U34D
U35A: U35A
U35B: U35B
U36: U36
U37: U37
U38: U38
U39: U39
U163A: U163A
U163B: U163B
U163C: U163C
U163D: U163D
U180C: U180C
U180D: U180D
U183A: U183A

Connections:
/FASTCLK: U24D.12 (U24-12), U183A.3 (U183-3)
/PHO_WRITE: U25A.1 (U25-1), U29A.1 (U29-1), U36.11 (U36-11)
/WR_1: U180D.12 (U180-12)
/WR_2: U180D.13 (U180-13)
A/R: Q1.1 (Q1-1)
CTRL: U183A.5 (U183-5)
DONE_RB: U23B.13 (U23-13), U24C.9 (U24-9), U33B.6 (U33-6)
DURCLK: U28.15 (U28-15), U29A.2 (U29-2)
DUR_0_LAT: U22A.1 (U22-1)
DUR_1_LAT: U9F.13 (U9-13), U22B.13 (U22-13), U26B.5 (U26-5)
GND: C2.1 (C2-1), Q1.3 (Q1-3), R1.1 (R1-1), R2.1 (R2-1), R3.1 (R3-1), U9D.7 (U9-7), U11A.7 (U11-7), U21B.7 (U21-7), U21B.8 (U21-8), U21B.10 (U21-10), U22A.4 (U22-4), U22A.6 (U22-6), U22A.7 (U22-7), U22B.8 (U22-8), U22B.10 (U22-10), U23A.4 (U23-4), U23A.6 (U23-6), U23A.7 (U23-7), U23B.8 (U23-8), U24B.7 (U24-7), U25A.7 (U25-7), U26A.7 (U26-7), U28.8 (U28-8), U29A.7 (U29-7), U30C.7 (U30-7), U31A.7 (U31-7), U32A.7 (U32-7), U33A.7 (U33-7), U34C.7 (U34-7), U35A.7 (U35-7), U36.8 (U36-8), U37.8 (U37-8), U38.2 (U38-2), U38.4 (U38-4), U38.8 (U38-8), U38.12 (U38-12), U39.6 (U39-6), U39.7 (U39-7), U39.8 (U39-8), U163A.7 (U163-7), U180C.7 (U180-7), U183A.4 (U183-4), U183A.7 (U183-7)
LATCH: U39.3 (U39-3)
NetC2_2: C2.2 (C2-2), U30D.9 (U30-9), U35A.1 (U35-1), U38.3 (U38-3)
NetQ1_2: Q1.2 (Q1-2), R8.2 (R8-2)
NetR2_2: R2.2 (R2-2), U33A.2 (U33-2), U39.14 (U39-14)
NetR3_2: R3.2 (R3-2), U32A.1 (U32-1), U39.13 (U39-13)
NetR8_1: R8.1 (R8-1), U24C.10 (U24-10)
NetU9_8: U9D.8 (U9-8), U183A.6 (U183-6)
NetU9_10: U9E.10 (U9-10), U24B.5 (U24-5)
NetU9_11: U9E.11 (U9-11), U180D.11 (U180-11)
NetU9_12: U9F.12 (U9-12), U24B.6 (U24-6), U26A.1 (U26-1)
NetU11_1: U11A.1 (U11-1), U30E.10 (U30-10)
NetU11_9: U11A.9 (U11-9), U34D.13 (U34-13)
NetU11_10: U11C.10 (U11-10), U34C.9 (U34-9)
NetU11_13: U11C.13 (U11-13), U30E.11 (U30-11), U180C.10 (U180-10)
NetU21_9: U21B.9 (U21-9), U21B.12 (U21-12), U28.2 (U28-2), U36.10 (U36-10)
NetU22_2: U22A.2 (U22-2)
NetU22_3: U22A.3 (U22-3), U22B.11 (U22-11), U26C.10 (U26-10)
NetU22_12: U22B.12 (U22-12)
NetU23_1: U23A.1 (U23-1), U24C.8 (U24-8)
NetU23_2: U23A.2 (U23-2)
NetU23_3: U23A.3 (U23-3), U24D.11 (U24-11), U26C.8 (U26-8)
NetU23_5: U23A.5 (U23-5), U25D.11 (U25-11), U26C.9 (U26-9)
NetU23_10: U23B.10 (U23-10), U25B.4 (U25-4)
NetU23_11: U23B.11 (U23-11), U25C.10 (U25-10)
NetU23_12: U23B.12 (U23-12)
NetU24_4: U24B.4 (U24-4), U25B.6 (U25-6)
NetU24_13: U24D.13 (U24-13), U25A.2 (U25-2), U183A.1 (U183-1)
NetU25_3: U25A.3 (U25-3), U25B.5 (U25-5)
NetU25_8: U25C.8 (U25-8), U26A.3 (U26-3)
NetU25_9: U25C.9 (U25-9), U26B.4 (U26-4)
NetU26_2: U26A.2 (U26-2), U29B.4 (U29-4)
NetU26_6: U26B.6 (U26-6), U30D.8 (U30-8), U33B.5 (U33-5)
NetU28_9: U28.9 (U28-9), U29A.3 (U29-3), U37.10 (U37-10)
NetU28_11: U28.11 (U28-11)
NetU28_12: U28.12 (U28-12)
NetU28_13: U28.13 (U28-13)
NetU28_14: U28.14 (U28-14)
NetU29_5: U29B.5 (U29-5), U29B.6 (U29-6), U35B.13 (U35-13)
NetU30_5: U30C.5 (U30-5), U33B.4 (U33-4)
NetU30_6: U30C.6 (U30-6), U37.11 (U37-11)
NetU30_12: U30F.12 (U30-12), U31A.1 (U31-1)
NetU31_3: U31A.3 (U31-3), U31D.13 (U31-13)
NetU31_4: U31B.4 (U31-4), U31C.9 (U31-9)
NetU32_2: U32A.2 (U32-2), U33A.1 (U33-1), U38.6 (U38-6)
NetU32_3: U32A.3 (U32-3), U32D.13 (U32-13)
NetU32_10: U32C.10 (U32-10), U32D.12 (U32-12)
NetU33_3: U33A.3 (U33-3), U33D.13 (U33-13)
NetU33_10: U33C.10 (U33-10), U33D.12 (U33-12)
NetU34_10: U34C.10 (U34-10), U34D.12 (U34-12)
NetU35_2: U35A.2 (U35-2), U38.9 (U38-9), U163D.8 (U163-8)
NetU35_3: U35A.3 (U35-3), U38.11 (U38-11), U163C.6 (U163-6)
NetU35_4: U35A.4 (U35-4), U38.14 (U38-14), U163B.4 (U163-4)
NetU35_5: U35A.5 (U35-5), U38.1 (U38-1), U163A.2 (U163-2)
NetU35_9: U35B.9 (U35-9), U36.9 (U36-9)
NetU35_10: U35B.10 (U35-10), U36.7 (U36-7)
NetU35_11: U35B.11 (U35-11), U36.6 (U36-6)
NetU35_12: U35B.12 (U35-12), U36.5 (U36-5)
NetU36_1: U36.1 (U36-1)
NetU36_2: U36.2 (U36-2)
NetU36_3: U36.3 (U36-3)
NetU36_4: U36.4 (U36-4)
NetU36_12: U36.12 (U36-12)
NetU36_13: U36.13 (U36-13)
NetU36_14: U36.14 (U36-14)
NetU36_15: U36.15 (U36-15)
NetU37_1: U37.1 (U37-1)
NetU37_2: U37.2 (U37-2)
NetU37_3: U37.3 (U37-3)
NetU37_4: U37.4 (U37-4)
NetU37_5: U37.5 (U37-5), U163A.1 (U163-1)
NetU37_6: U37.6 (U37-6), U163B.3 (U163-3)
NetU37_7: U37.7 (U37-7), U163C.5 (U163-5)
NetU37_9: U37.9 (U37-9), U163D.9 (U163-9)
NetU37_12: U37.12 (U37-12)
NetU37_13: U37.13 (U37-13)
NetU37_14: U37.14 (U37-14)
NetU37_15: U37.15 (U37-15)
NetU38_5: U38.5 (U38-5)
NetU38_7: U38.7 (U38-7)
NetU39_1: U39.1 (U39-1)
NetU39_2: U39.2 (U39-2)
NetU39_4: U39.4 (U39-4)
NetU39_5: U39.5 (U39-5)
NetU39_12: U39.12 (U39-12)
NetU180_8: U180C.8 (U180-8), U183A.2 (U183-2)
PHO_WRITE: U32C.9 (U32-9), U33C.9 (U33-9)
PW_0: U32C.8 (U32-8), U32D.11 (U32-11)
PW_1: U11A.8 (U11-8), U11C.11 (U11-11), U33C.8 (U33-8), U33D.11 (U33-11)
PW_2: U31C.10 (U31-10), U31D.12 (U31-12)
PW_3: U34C.8 (U34-8), U34D.11 (U34-11)
PW_5: U31C.8 (U31-8), U31D.11 (U31-11)
RATECLK: U21B.11 (U21-11)
RATECLK/2: U21B.13 (U21-13), U28.10 (U28-10)
SEL0: U39.11 (U39-11)
SEL1: U39.10 (U39-10)
SEL2: U39.9 (U39-9)
T/PD_/RST: U9D.9 (U9-9)
TDUR_0: U22A.5 (U22-5), U25D.13 (U25-13), U28.3 (U28-3)
TDUR_1: U22B.9 (U22-9), U25D.12 (U25-12), U28.4 (U28-4)
TPARM_0: U38.13 (U38-13)
TPARM_1: U180C.9 (U180-9)
TPARM_2: U30F.13 (U30-13), U31B.6 (U31-6)
VCC: U23B.9 (U23-9), U28.1 (U28-1), U28.5 (U28-5), U28.6 (U28-6), U28.7 (U28-7), U28.16 (U28-16), U36.16 (U36-16), U37.16 (U37-16), U38.10 (U38-10), U38.15 (U38-15), U38.16 (U38-16), U39.16 (U39-16)
VDD: U9D.14 (U9-14), U11A.14 (U11-14), U21B.14 (U21-14), U22A.14 (U22-14), U23A.14 (U23-14), U24B.14 (U24-14), U25A.14 (U25-14), U26A.14 (U26-14), U29A.14 (U29-14), U30C.14 (U30-14), U31A.14 (U31-14), U32A.14 (U32-14), U33A.14 (U33-14), U34C.14 (U34-14), U35A.14 (U35-14), U163A.14 (U163-14), U180C.14 (U180-14), U183A.14 (U183-14)
WR_SEL_2: R1.2 (R1-2), U11A.2 (U11-2), U11C.12 (U11-12), U31A.2 (U31-2), U31B.5 (U31-5), U39.15 (U39-15)
