hasseily/appletini-one/schematics/sc02_prototype/kicad/sc02_sheet_06_digital_4_schdoc.kicad_sch

## KiCad design schematics/sc02_prototype/kicad/sc02_sheet_06_digital_4_schdoc.kicad_sch (2026-08-26)

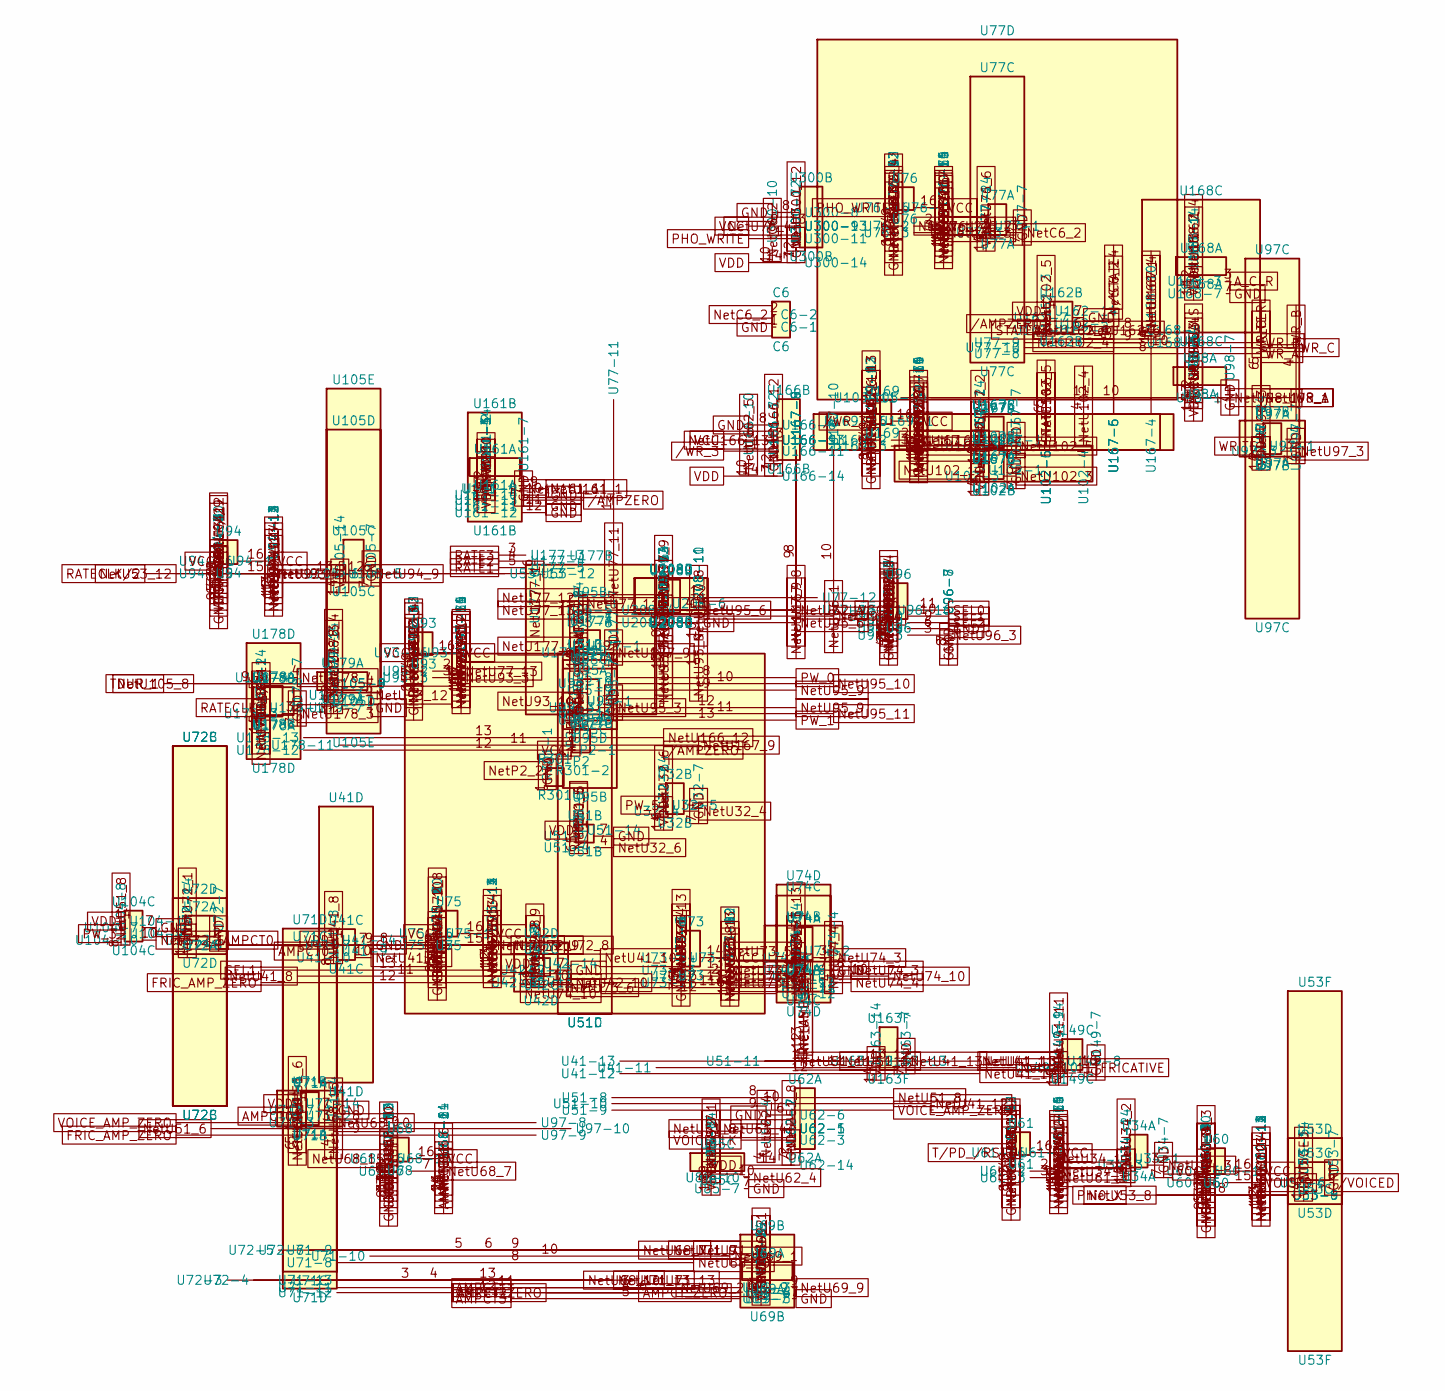
[picture p54: schematic sc02_sheet_06_digital_4_schdoc.kicad_sch]

Parts:
C6: C6
P2: P2
R301: R301
U32B: U32B
U34A: U34A
U41C: U41C
U41D: U41D
U42C: U42C
U42D: U42D
U51B: U51B
U51C: U51C
U51D: U51D
U53C: U53C
U53D: U53D
U53F: U53F
U60: U60
U61: U61
U62A: U62A
U68: U68
U69A: U69A
U69B: U69B
U71A: U71A
U71B: U71B
U71C: U71C
U71D: U71D
U72A: U72A
U72B: U72B
U72C: U72C
U72D: U72D
U73: U73
U74A: U74A
U74B: U74B
U74C: U74C
U74D: U74D
U75: U75
U76: U76
U77A: U77A
U77C: U77C
U77D: U77D
U85C: U85C
U93: U93
U94: U94
U95A: U95A
U95B: U95B
U95C: U95C
U95D: U95D
U96: U96
U97A: U97A
U97B: U97B
U97C: U97C
U98A: U98A
U102A: U102A
U102B: U102B
U104C: U104C
U105C: U105C
U105D: U105D
U105E: U105E
U149C: U149C
U161A: U161A
U161B: U161B
U162B: U162B
U163F: U163F
U166B: U166B
U167A: U167A
U167B: U167B
U167C: U167C
U168A: U168A
U168C: U168C
U169: U169
U177A: U177A
U177B: U177B
U178A: U178A
U178B: U178B
U178D: U178D
U179A: U179A
U208B: U208B
U208C: U208C
U208D: U208D
U300B: U300B

Connections:
/AMPZERO: U161B.13 (U161-13), U162B.5 (U162-5), U178D.12 (U178-12)
/STATE4: U167B.6 (U167-6)
/VOICED: U53C.6 (U53-6), U60.7 (U60-7)
/WR_3: U166B.11 (U166-11), U169.1 (U169-1)
AMP0: U161A.2 (U161-2)
AMP1: U161A.3 (U161-3)
AMP2: U161A.4 (U161-4)
AMP3: U161A.5 (U161-5)
AMPCT0: U41C.9 (U41-9), U71A.2 (U71-2), U72A.2 (U72-2)
AMPCT1: U68.11 (U68-11), U69B.3 (U69-3)
AMPCT2: U68.14 (U68-14), U69B.4 (U69-4)
AMPCT3: U68.2 (U68-2), U69B.5 (U69-5)
AMPCT_ZERO: U69B.6 (U69-6), U71D.12 (U71-12)
A_CLR: U97B.5 (U97-5), U98A.5 (U98-5), U168A.3 (U168-3)
DURCLK: U169.12 (U169-12)
FRICATIVE: U149C.10 (U149-10)
FRIC_AMP_ZERO: U42D.12 (U42-12), U51D.12 (U51-12), U97C.9 (U97-9)
GND: C6.1 (C6-1), R301.1 (R301-1), U32B.7 (U32-7), U34A.7 (U34-7), U41C.7 (U41-7), U42C.7 (U42-7), U51B.7 (U51-7), U53C.7 (U53-7), U60.5 (U60-5), U60.8 (U60-8), U61.8 (U61-8), U62A.6 (U62-6), U62A.7 (U62-7), U68.1 (U68-1), U68.3 (U68-3), U68.4 (U68-4), U68.5 (U68-5), U68.8 (U68-8), U68.12 (U68-12), U68.13 (U68-13), U69A.7 (U69-7), U69A.8 (U69-8), U71A.7 (U71-7), U72A.7 (U72-7), U73.7 (U73-7), U74A.7 (U74-7), U75.4 (U75-4), U75.5 (U75-5), U75.6 (U75-6), U75.8 (U75-8), U76.8 (U76-8), U77A.7 (U77-7), U85C.7 (U85-7), U93.8 (U93-8), U94.8 (U94-8), U95A.7 (U95-7), U96.4 (U96-4), U96.6 (U96-6), U96.7 (U96-7), U96.8 (U96-8), U97A.7 (U97-7), U98A.7 (U98-7), U102A.7 (U102-7), U104C.7 (U104-7), U105C.7 (U105-7), U149C.7 (U149-7), U161A.7 (U161-7), U161B.10 (U161-10), U161B.11 (U161-11), U161B.12 (U161-12), U162B.7 (U162-7), U163F.7 (U163-7), U166B.7 (U166-7), U166B.8 (U166-8), U167A.7 (U167-7), U168A.7 (U168-7), U169.8 (U169-8), U177A.7 (U177-7), U178A.7 (U178-7), U179A.7 (U179-7), U208B.7 (U208-7), U300B.7 (U300-7), U300B.8 (U300-8)
NetC6_2: C6.2 (C6-2), U77A.3 (U77-3), U167B.5 (U167-5), U300B.10 (U300-10)
NetP2_2: P2.2 (P2-2), R301.2 (R301-2), U177A.8 (U177-8)
NetU32_4: U32B.4 (U32-4), U95B.5 (U95-5)
NetU32_6: U32B.6 (U32-6), U51B.4 (U51-4)
NetU34_1: U34A.1 (U34-1), U61.2 (U61-2), U61.5 (U61-5)
NetU34_2: U34A.2 (U34-2), U61.6 (U61-6)
NetU34_3: U34A.3 (U34-3), U60.9 (U60-9)
NetU41_8: U41C.8 (U41-8), U42D.11 (U42-11)
NetU41_10: U41C.10 (U41-10), U73.3 (U73-3), U75.2 (U75-2)
NetU41_11: U41D.11 (U41-11), U149C.8 (U149-8), U149C.9 (U149-9)
NetU41_12: U41D.12 (U41-12), U51C.10 (U51-10)
NetU41_13: U41D.13 (U41-13), U163F.12 (U163-12)
NetU42_8: U42C.8 (U42-8), U75.11 (U75-11)
NetU42_9: U42C.9 (U42-9), U75.12 (U75-12)
NetU42_10: U42C.10 (U42-10), U74D.13 (U74-13)
NetU51_6: U51B.6 (U51-6), U71A.1 (U71-1), U97C.10 (U97-10)
NetU51_8: U51C.8 (U51-8), U62A.2 (U62-2), U62A.5 (U62-5), U104C.8 (U104-8)
NetU51_11: U51D.11 (U51-11), U163F.13 (U163-13)
NetU51_13: U51D.13 (U51-13), U73.1 (U73-1), U73.10 (U73-10)
NetU53_8: U53D.8 (U53-8), U60.2 (U60-2)
NetU53_12: U53F.12 (U53-12), U94.10 (U94-10)
NetU60_11: U60.11 (U60-11)
NetU60_12: U60.12 (U60-12)
NetU60_13: U60.13 (U60-13)
NetU60_14: U60.14 (U60-14)
NetU61_3: U61.3 (U61-3)
NetU61_4: U61.4 (U61-4), U62A.1 (U62-1)
NetU61_7: U61.7 (U61-7)
NetU61_10: U61.10 (U61-10)
NetU61_11: U61.11 (U61-11)
NetU61_12: U61.12 (U61-12)
NetU61_13: U61.13 (U61-13)
NetU61_14: U61.14 (U61-14)
NetU61_15: U61.15 (U61-15)
NetU62_4: U62A.4 (U62-4), U85C.10 (U85-10)
NetU68_6: U68.6 (U68-6)
NetU68_7: U68.7 (U68-7), U72C.5 (U72-5), U85C.8 (U85-8)
NetU68_10: U68.10 (U68-10), U71A.3 (U71-3), U71C.8 (U71-8), U72B.3 (U72-3)
NetU68_15: U68.15 (U68-15), U71B.4 (U71-4)
NetU69_1: U69A.1 (U69-1), U71C.10 (U71-10)
NetU69_2: U69A.2 (U69-2), U71D.11 (U71-11)
NetU69_9: U69A.9 (U69-9), U71B.6 (U71-6)
NetU71_9: U71C.9 (U71-9), U72C.6 (U72-6)
NetU71_13: U71D.13 (U71-13), U72B.4 (U72-4)
NetU72_1: U72A.1 (U72-1), U85C.9 (U85-9), U104C.10 (U104-10)
NetU72_8: U72D.8 (U72-8), U75.9 (U75-9)
NetU72_9: U72D.9 (U72-9), U75.15 (U75-15)
NetU73_2: U73.2 (U73-2)
NetU73_4: U73.4 (U73-4), U73.9 (U73-9), U74B.5 (U74-5)
NetU73_5: U73.5 (U73-5), U73.12 (U73-12), U74A.2 (U74-2)
NetU73_6: U73.6 (U73-6), U74D.11 (U74-11)
NetU73_8: U73.8 (U73-8), U74B.6 (U74-6)
NetU73_11: U73.11 (U73-11)
NetU73_13: U73.13 (U73-13), U74A.1 (U74-1)
NetU74_3: U74A.3 (U74-3), U74C.8 (U74-8)
NetU74_4: U74B.4 (U74-4), U74C.9 (U74-9)
NetU74_10: U74C.10 (U74-10), U74D.12 (U74-12)
NetU75_13: U75.13 (U75-13)
NetU75_14: U75.14 (U75-14)
NetU76_2: U76.2 (U76-2), U76.5 (U76-5), U77A.1 (U77-1)
NetU76_3: U76.3 (U76-3)
NetU76_4: U76.4 (U76-4), U98A.2 (U98-2), U300B.13 (U300-13)
NetU76_6: U76.6 (U76-6), U77A.2 (U77-2)
NetU76_7: U76.7 (U76-7)
NetU76_10: U76.10 (U76-10)
NetU76_11: U76.11 (U76-11)
NetU76_12: U76.12 (U76-12)
NetU76_13: U76.13 (U76-13)
NetU76_14: U76.14 (U76-14)
NetU76_15: U76.15 (U76-15)
NetU77_11: U77D.11 (U77-11), U208B.6 (U208-6)
NetU77_12: U77D.12 (U77-12), U93.6 (U93-6)
NetU77_13: U77D.13 (U77-13), U93.2 (U93-2), U93.5 (U93-5)
NetU93_3: U93.3 (U93-3)
NetU93_4: U93.4 (U93-4), U94.15 (U94-15), U105C.5 (U105-5)
NetU93_7: U93.7 (U93-7)
NetU93_10: U93.10 (U93-10), U93.13 (U93-13), U95A.1 (U95-1)
NetU93_11: U93.11 (U93-11)
NetU93_12: U93.12 (U93-12), U179A.3 (U179-3)
NetU93_14: U93.14 (U93-14), U95A.2 (U95-2)
NetU93_15: U93.15 (U93-15)
NetU94_9: U94.9 (U94-9), U105C.6 (U105-6)
NetU94_11: U94.11 (U94-11)
NetU94_12: U94.12 (U94-12)
NetU94_13: U94.13 (U94-13)
NetU94_14: U94.14 (U94-14)
NetU95_3: U95A.3 (U95-3), U208D.13 (U208-13)
NetU95_4: U95B.4 (U95-4), U96.12 (U96-12), U96.13 (U96-13), U96.14 (U96-14)
NetU95_6: U95B.6 (U95-6), U96.15 (U96-15), U208B.4 (U208-4)
NetU95_9: U95C.9 (U95-9), U95D.12 (U95-12), U208D.11 (U208-11)
NetU95_10: U95C.10 (U95-10), U96.5 (U96-5)
NetU95_11: U95D.11 (U95-11), U96.2 (U96-2)
NetU96_1: U96.1 (U96-1), U167C.10 (U167-10)
NetU96_3: U96.3 (U96-3), U97A.2 (U97-2)
NetU97_3: U97A.3 (U97-3), U98A.3 (U98-3)
NetU98_1: U98A.1 (U98-1), U105E.11 (U105-11)
NetU102_1: U102A.1 (U102-1), U169.10 (U169-10), U169.13 (U169-13)
NetU102_2: U102A.2 (U102-2), U169.14 (U169-14)
NetU102_3: U102A.3 (U102-3), U208C.9 (U208-9)
NetU102_4: U102B.4 (U102-4), U168C.9 (U168-9)
NetU102_5: U102B.5 (U102-5), U162B.3 (U162-3), U166B.10 (U166-10), U167A.3 (U167-3)
NetU105_8: U105D.8 (U105-8), U178B.5 (U178-5)
NetU161_1: U161A.1 (U161-1), U161B.9 (U161-9)
NetU162_6: U162B.6 (U162-6), U168C.8 (U168-8)
NetU166_12: U166B.12 (U166-12), U178D.13 (U178-13)
NetU166_13: U166B.13 (U166-13), U169.4 (U169-4)
NetU167_1: U167A.1 (U167-1), U169.2 (U169-2), U169.5 (U169-5)
NetU167_2: U167A.2 (U167-2), U169.6 (U169-6)
NetU167_4: U167B.4 (U167-4), U168A.2 (U168-2)
NetU167_8: U167C.8 (U167-8), U208C.10 (U208-10)
NetU167_9: U167C.9 (U167-9), U178D.11 (U178-11)
NetU168_1: U168A.1 (U168-1), U168C.10 (U168-10)
NetU169_3: U169.3 (U169-3)
NetU169_7: U169.7 (U169-7)
NetU169_11: U169.11 (U169-11)
NetU169_15: U169.15 (U169-15)
NetU177_1: U177A.1 (U177-1), U177B.6 (U177-6)
NetU177_9: U177A.9 (U177-9), U208B.5 (U208-5), U208C.8 (U208-8), U208D.12 (U208-12)
NetU178_3: U178A.3 (U178-3), U179A.1 (U179-1)
NetU178_4: U178B.4 (U178-4), U179A.2 (U179-2)
NetU300_12: U300B.12 (U300-12)
PHO_WRITE: U76.1 (U76-1), U300B.11 (U300-11)
PW_0: U95C.8 (U95-8)
PW_1: U95D.13 (U95-13)
PW_3: U104C.9 (U104-9)
PW_5: U32B.5 (U32-5)
Phi0_X: U53D.9 (U53-9), U61.9 (U61-9)
RATE0: U177A.2 (U177-2)
RATE1: U177B.5 (U177-5)
RATE2: U177B.4 (U177-4)
RATE3: U177B.3 (U177-3)
RATECLK: U178A.1 (U178-1)
RATECLK/2: U53F.13 (U53-13), U94.2 (U94-2), U178B.6 (U178-6)
RESA_EQUALS: U98A.4 (U98-4)
SEL0: U96.11 (U96-11)
SEL1: U42D.13 (U42-13), U96.10 (U96-10)
SEL2: U71B.5 (U71-5), U76.9 (U76-9), U93.9 (U93-9), U96.9 (U96-9), U169.9 (U169-9)
STATE4: U162B.4 (U162-4)
STATE5&6: U102B.6 (U102-6)
T/PD_/RST: U61.1 (U61-1)
TDUR_1: U105D.9 (U105-9), U178A.2 (U178-2)
TPHO_5: U51B.5 (U51-5)
TRANS0: U94.3 (U94-3)
TRANS1: U94.4 (U94-4)
TRANS2: U94.5 (U94-5)
VCC: P2.1 (P2-1), U60.1 (U60-1), U60.3 (U60-3), U60.4 (U60-4), U60.6 (U60-6), U60.10 (U60-10), U60.16 (U60-16), U61.16 (U61-16), U68.9 (U68-9), U68.16 (U68-16), U73.14 (U73-14), U75.1 (U75-1), U75.3 (U75-3), U75.7 (U75-7), U75.10 (U75-10), U75.16 (U75-16), U76.16 (U76-16), U93.1 (U93-1), U93.16 (U93-16), U94.1 (U94-1), U94.6 (U94-6), U94.7 (U94-7), U94.16 (U94-16), U96.16 (U96-16), U166B.9 (U166-9), U169.16 (U169-16), U300B.9 (U300-9)
VDD: U32B.14 (U32-14), U34A.14 (U34-14), U41C.14 (U41-14), U42C.14 (U42-14), U51B.14 (U51-14), U53C.14 (U53-14), U62A.14 (U62-14), U69A.14 (U69-14), U71A.14 (U71-14), U72A.14 (U72-14), U74B.14 (U74-14), U77A.14 (U77-14), U85C.14 (U85-14), U95A.14 (U95-14), U97A.14 (U97-14), U98A.14 (U98-14), U102A.14 (U102-14), U104C.14 (U104-14), U105C.14 (U105-14), U149C.14 (U149-14), U161A.14 (U161-14), U162B.14 (U162-14), U163F.14 (U163-14), U166B.14 (U166-14), U167A.14 (U167-14), U168A.14 (U168-14), U177A.14 (U177-14), U178A.14 (U178-14), U179A.14 (U179-14), U208B.14 (U208-14), U300B.14 (U300-14)
VOICECLK: U62A.3 (U62-3)
VOICED: U53C.5 (U53-5), U60.15 (U60-15)
VOICE_AMP_ZERO: U51C.9 (U51-9), U97C.8 (U97-8)
WRITE: U97A.1 (U97-1), U97B.6 (U97-6)
WR_A: U77C.8 (U77-8), U105E.10 (U105-10)
WR_B: U77C.9 (U77-9), U97B.4 (U97-4)
WR_C: U77C.10 (U77-10)
