hasseily/appletini-one/schematics/sc02_prototype/kicad/sc02_sheet_07_digital_5_schdoc.kicad_sch

## KiCad design schematics/sc02_prototype/kicad/sc02_sheet_07_digital_5_schdoc.kicad_sch (2026-08-26)

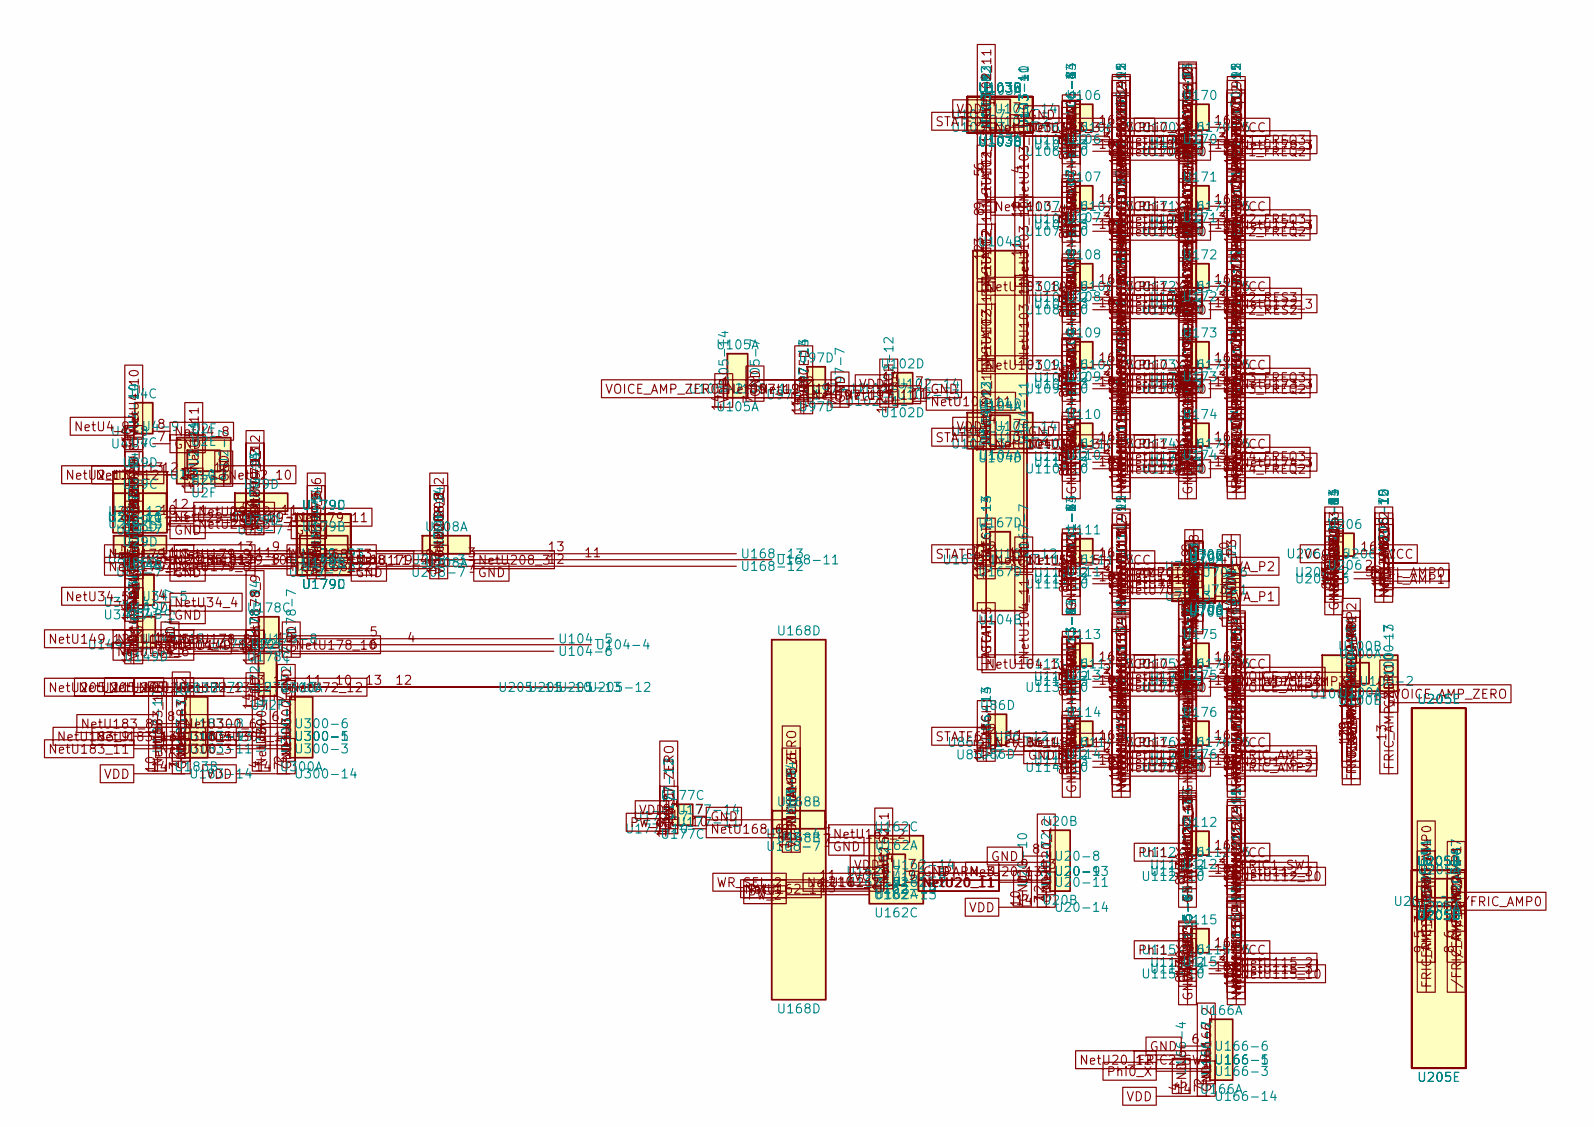
[picture p55: schematic sc02_sheet_07_digital_5_schdoc.kicad_sch]

Parts:
U2E: U2E
U2F: U2F
U4C: U4C
U20B: U20B
U29C: U29C
U29D: U29D
U34B: U34B
U70A: U70A
U70B: U70B
U70C: U70C
U70D: U70D
U72F: U72F
U79D: U79D
U85D: U85D
U86D: U86D
U97D: U97D
U100A: U100A
U100B: U100B
U102D: U102D
U103A: U103A
U103B: U103B
U103C: U103C
U103D: U103D
U104A: U104A
U104B: U104B
U104D: U104D
U105A: U105A
U106: U106
U107: U107
U108: U108
U109: U109
U110: U110
U111: U111
U112: U112
U113: U113
U114: U114
U115: U115
U149D: U149D
U162A: U162A
U162C: U162C
U166A: U166A
U167D: U167D
U168B: U168B
U168D: U168D
U170: U170
U171: U171
U172: U172
U173: U173
U174: U174
U175: U175
U176: U176
U177C: U177C
U178C: U178C
U179B: U179B
U179C: U179C
U179D: U179D
U183B: U183B
U205A: U205A
U205B: U205B
U205C: U205C
U205D: U205D
U205E: U205E
U205F: U205F
U206: U206
U208A: U208A
U300A: U300A

Connections:
5V: U2E.14 (U2-14), U4C.14 (U4-14)
/FRIC_AMP0: U205A.2 (U205-2)
/FRIC_AMP1: U205B.4 (U205-4)
/FRIC_AMP2: U205C.6 (U205-6)
/FRIC_AMP3: U205D.8 (U205-8)
AMPCT0: U70D.12 (U70-12)
AMPCT1: U70A.2 (U70-2)
AMPCT2: U70B.6 (U70-6)
AMPCT3: U70C.9 (U70-9)
AMPCT_ZERO: U177C.13 (U177-13)
F1_FREQ0: U170.1 (U170-1)
F1_FREQ1: U170.11 (U170-11)
F1_FREQ2: U170.10 (U170-10)
F1_FREQ3: U170.2 (U170-2)
F2_FREQ0: U171.1 (U171-1)
F2_FREQ1: U171.11 (U171-11)
F2_FREQ2: U171.10 (U171-10)
F2_FREQ3: U171.2 (U171-2)
F2_RES0: U172.1 (U172-1)
F2_RES1: U172.11 (U172-11)
F2_RES2: U172.10 (U172-10)
F2_RES3: U172.2 (U172-2)
F3_FREQ0: U173.1 (U173-1)
F3_FREQ1: U173.11 (U173-11)
F3_FREQ2: U173.10 (U173-10)
F3_FREQ3: U173.2 (U173-2)
F4_FREQ0: U174.1 (U174-1)
F4_FREQ1: U174.11 (U174-11)
F4_FREQ2: U174.10 (U174-10)
F4_FREQ3: U174.2 (U174-2)
FL_AMP0: U206.2 (U206-2)
FL_AMP1: U206.5 (U206-5)
FL_AMP2: U206.7 (U206-7)
FL_AMP3: U206.10 (U206-10)
FRIC1_SW: U112.2 (U112-2)
FRIC2_SW: U166A.1 (U166-1)
FRIC_AMP0: U100B.12 (U100-12), U176.1 (U176-1), U205A.1 (U205-1)
FRIC_AMP1: U100B.11 (U100-11), U176.11 (U176-11), U205B.3 (U205-3)
FRIC_AMP2: U100B.10 (U100-10), U176.10 (U176-10), U205C.5 (U205-5)
FRIC_AMP3: U100B.9 (U100-9), U176.2 (U176-2), U205D.9 (U205-9)
FRIC_AMP_ZERO: U100B.13 (U100-13), U168B.5 (U168-5)
GND: U2E.7 (U2-7), U4C.7 (U4-7), U20B.7 (U20-7), U20B.8 (U20-8), U20B.10 (U20-10), U29C.7 (U29-7), U34B.7 (U34-7), U70A.7 (U70-7), U72F.7 (U72-7), U79D.7 (U79-7), U85D.7 (U85-7), U86D.7 (U86-7), U97D.7 (U97-7), U100A.7 (U100-7), U102D.7 (U102-7), U103A.7 (U103-7), U104A.7 (U104-7), U105A.7 (U105-7), U106.8 (U106-8), U107.8 (U107-8), U108.8 (U108-8), U109.8 (U109-8), U110.8 (U110-8), U111.8 (U111-8), U112.8 (U112-8), U113.8 (U113-8), U114.8 (U114-8), U115.8 (U115-8), U149D.7 (U149-7), U162A.7 (U162-7), U166A.4 (U166-4), U166A.6 (U166-6), U166A.7 (U166-7), U167D.7 (U167-7), U168B.7 (U168-7), U170.8 (U170-8), U171.8 (U171-8), U172.8 (U172-8), U173.8 (U173-8), U174.8 (U174-8), U175.8 (U175-8), U176.8 (U176-8), U177C.7 (U177-7), U178C.7 (U178-7), U179B.7 (U179-7), U183B.7 (U183-7), U205A.7 (U205-7), U206.8 (U206-8), U208A.7 (U208-7), U300A.7 (U300-7)
LATCH: U86D.13 (U86-13), U102D.12 (U102-12), U104D.12 (U104-12), U167D.13 (U167-13)
NetU2_10: U2E.10 (U2-10)
NetU2_11: U2E.11 (U2-11)
NetU2_12: U2F.12 (U2-12)
NetU2_13: U2F.13 (U2-13)
NetU4_8: U4C.8 (U4-8)
NetU4_9: U4C.9 (U4-9)
NetU4_10: U4C.10 (U4-10)
NetU20_11: U20B.11 (U20-11), U162A.9 (U162-9)
NetU20_12: U20B.12 (U20-12), U166A.5 (U166-5)
NetU20_13: U20B.13 (U20-13), U112.4 (U112-4)
NetU29_8: U29C.8 (U29-8)
NetU29_9: U29C.9 (U29-9)
NetU29_10: U29C.10 (U29-10)
NetU29_11: U29D.11 (U29-11)
NetU29_12: U29D.12 (U29-12)
NetU29_13: U29D.13 (U29-13)
NetU34_4: U34B.4 (U34-4)
NetU34_5: U34B.5 (U34-5)
NetU34_6: U34B.6 (U34-6)
NetU70_1: U70A.1 (U70-1), U111.11 (U111-11)
NetU70_5: U70B.5 (U70-5), U111.10 (U111-10)
NetU70_8: U70C.8 (U70-8), U111.2 (U111-2)
NetU70_13: U70D.13 (U70-13), U111.1 (U111-1)
NetU72_12: U72F.12 (U72-12)
NetU72_13: U72F.13 (U72-13)
NetU79_11: U79D.11 (U79-11)
NetU79_12: U79D.12 (U79-12)
NetU79_13: U79D.13 (U79-13)
NetU85_11: U85D.11 (U85-11)
NetU85_12: U85D.12 (U85-12)
NetU85_13: U85D.13 (U85-13)
NetU86_11: U86D.11 (U86-11), U114.5 (U114-5)
NetU97_11: U97D.11 (U97-11), U102D.13 (U102-13)
NetU97_12: U97D.12 (U97-12), U105A.2 (U105-2)
NetU102_11: U102D.11 (U102-11), U103A.1 (U103-1), U103B.5 (U103-5), U103C.8 (U103-8), U103D.12 (U103-12), U104A.1 (U104-1)
NetU103_3: U103A.3 (U103-3), U106.5 (U106-5)
NetU103_4: U103B.4 (U103-4), U107.5 (U107-5)
NetU103_10: U103C.10 (U103-10), U108.5 (U108-5)
NetU103_11: U103D.11 (U103-11), U109.5 (U109-5)
NetU104_3: U104A.3 (U104-3), U110.5 (U110-5)
NetU104_4: U104B.4 (U104-4)
NetU104_5: U104B.5 (U104-5)
NetU104_6: U104B.6 (U104-6)
NetU104_11: U104D.11 (U104-11), U113.5 (U113-5)
NetU106_1: U106.1 (U106-1), U170.14 (U170-14)
NetU106_2: U106.2 (U106-2), U170.4 (U170-4)
NetU106_3: U106.3 (U106-3)
NetU106_9: U106.9 (U106-9)
NetU106_10: U106.10 (U106-10), U170.7 (U170-7)
NetU106_11: U106.11 (U106-11), U170.13 (U170-13)
NetU106_12: U106.12 (U106-12)
NetU106_15: U106.15 (U106-15)
NetU107_1: U107.1 (U107-1), U171.14 (U171-14)
NetU107_2: U107.2 (U107-2), U171.4 (U171-4)
NetU107_3: U107.3 (U107-3)
NetU107_9: U107.9 (U107-9)
NetU107_10: U107.10 (U107-10), U171.7 (U171-7)
NetU107_11: U107.11 (U107-11), U171.13 (U171-13)
NetU107_12: U107.12 (U107-12)
NetU107_15: U107.15 (U107-15)
NetU108_1: U108.1 (U108-1), U172.14 (U172-14)
NetU108_2: U108.2 (U108-2), U172.4 (U172-4)
NetU108_3: U108.3 (U108-3)
NetU108_9: U108.9 (U108-9)
NetU108_10: U108.10 (U108-10), U172.7 (U172-7)
NetU108_11: U108.11 (U108-11), U172.13 (U172-13)
NetU108_12: U108.12 (U108-12)
NetU108_15: U108.15 (U108-15)
NetU109_1: U109.1 (U109-1), U173.14 (U173-14)
NetU109_2: U109.2 (U109-2), U173.4 (U173-4)
NetU109_3: U109.3 (U109-3)
NetU109_9: U109.9 (U109-9)
NetU109_10: U109.10 (U109-10), U173.7 (U173-7)
NetU109_11: U109.11 (U109-11), U173.13 (U173-13)
NetU109_12: U109.12 (U109-12)
NetU109_15: U109.15 (U109-15)
NetU110_1: U110.1 (U110-1), U174.14 (U174-14)
NetU110_2: U110.2 (U110-2), U174.4 (U174-4)
NetU110_3: U110.3 (U110-3)
NetU110_9: U110.9 (U110-9)
NetU110_10: U110.10 (U110-10), U174.7 (U174-7)
NetU110_11: U110.11 (U110-11), U174.13 (U174-13)
NetU110_12: U110.12 (U110-12)
NetU110_15: U110.15 (U110-15)
NetU111_3: U111.3 (U111-3)
NetU111_5: U111.5 (U111-5), U167D.11 (U167-11)
NetU111_9: U111.9 (U111-9)
NetU111_12: U111.12 (U111-12)
NetU111_15: U111.15 (U111-15)
NetU112_1: U112.1 (U112-1)
NetU112_3: U112.3 (U112-3)
NetU112_7: U112.7 (U112-7)
NetU112_9: U112.9 (U112-9)
NetU112_10: U112.10 (U112-10)
NetU112_11: U112.11 (U112-11)
NetU112_12: U112.12 (U112-12)
NetU112_13: U112.13 (U112-13)
NetU112_14: U112.14 (U112-14)
NetU112_15: U112.15 (U112-15)
NetU113_1: U113.1 (U113-1), U175.14 (U175-14)
NetU113_2: U113.2 (U113-2), U175.4 (U175-4)
NetU113_3: U113.3 (U113-3)
NetU113_9: U113.9 (U113-9)
NetU113_10: U113.10 (U113-10), U175.7 (U175-7)
NetU113_11: U113.11 (U113-11), U175.13 (U175-13)
NetU113_12: U113.12 (U113-12)
NetU113_15: U113.15 (U113-15)
NetU114_1: U114.1 (U114-1), U176.14 (U176-14)
NetU114_2: U114.2 (U114-2), U176.4 (U176-4)
NetU114_3: U114.3 (U114-3)
NetU114_9: U114.9 (U114-9)
NetU114_10: U114.10 (U114-10), U176.7 (U176-7)
NetU114_11: U114.11 (U114-11), U176.13 (U176-13)
NetU114_12: U114.12 (U114-12)
NetU114_15: U114.15 (U114-15)
NetU115_1: U115.1 (U115-1)
NetU115_2: U115.2 (U115-2)
NetU115_3: U115.3 (U115-3)
NetU115_9: U115.9 (U115-9)
NetU115_10: U115.10 (U115-10)
NetU115_11: U115.11 (U115-11)
NetU115_12: U115.12 (U115-12)
NetU115_15: U115.15 (U115-15)
NetU149_11: U149D.11 (U149-11)
NetU149_12: U149D.12 (U149-12)
NetU149_13: U149D.13 (U149-13)
NetU162_1: U162A.1 (U162-1), U162C.10 (U162-10)
NetU162_2: U162A.2 (U162-2), U168B.4 (U168-4)
NetU166_2: U166A.2 (U166-2)
NetU168_6: U168B.6 (U168-6), U177C.10 (U177-10)
NetU168_11: U168D.11 (U168-11)
NetU168_12: U168D.12 (U168-12)
NetU168_13: U168D.13 (U168-13)
NetU170_3: U170.3 (U170-3)
NetU170_9: U170.9 (U170-9)
NetU170_12: U170.12 (U170-12)
NetU170_15: U170.15 (U170-15)
NetU171_3: U171.3 (U171-3)
NetU171_9: U171.9 (U171-9)
NetU171_12: U171.12 (U171-12)
NetU171_15: U171.15 (U171-15)
NetU172_3: U172.3 (U172-3)
NetU172_9: U172.9 (U172-9)
NetU172_12: U172.12 (U172-12)
NetU172_15: U172.15 (U172-15)
NetU173_3: U173.3 (U173-3)
NetU173_9: U173.9 (U173-9)
NetU173_12: U173.12 (U173-12)
NetU173_15: U173.15 (U173-15)
NetU174_3: U174.3 (U174-3)
NetU174_9: U174.9 (U174-9)
NetU174_12: U174.12 (U174-12)
NetU174_15: U174.15 (U174-15)
NetU175_3: U175.3 (U175-3)
NetU175_9: U175.9 (U175-9)
NetU175_12: U175.12 (U175-12)
NetU175_15: U175.15 (U175-15)
NetU176_3: U176.3 (U176-3)
NetU176_9: U176.9 (U176-9)
NetU176_12: U176.12 (U176-12)
NetU176_15: U176.15 (U176-15)
NetU178_8: U178C.8 (U178-8)
NetU178_9: U178C.9 (U178-9)
NetU178_10: U178C.10 (U178-10)
NetU179_4: U179B.4 (U179-4)
NetU179_5: U179B.5 (U179-5)
NetU179_6: U179B.6 (U179-6)
NetU179_8: U179C.8 (U179-8)
NetU179_9: U179C.9 (U179-9)
NetU179_10: U179C.10 (U179-10)
NetU179_11: U179D.11 (U179-11)
NetU179_12: U179D.12 (U179-12)
NetU179_13: U179D.13 (U179-13)
NetU183_8: U183B.8 (U183-8)
NetU183_9: U183B.9 (U183-9)
NetU183_10: U183B.10 (U183-10)
NetU183_11: U183B.11 (U183-11)
NetU183_12: U183B.12 (U183-12)
NetU183_13: U183B.13 (U183-13)
NetU205_10: U205E.10 (U205-10)
NetU205_11: U205E.11 (U205-11)
NetU205_12: U205F.12 (U205-12)
NetU205_13: U205F.13 (U205-13)
NetU206_12: U206.12 (U206-12)
NetU206_13: U206.13 (U206-13)
NetU206_14: U206.14 (U206-14)
NetU206_15: U206.15 (U206-15)
NetU208_1: U208A.1 (U208-1)
NetU208_2: U208A.2 (U208-2)
NetU208_3: U208A.3 (U208-3)
NetU300_1: U300A.1 (U300-1)
NetU300_2: U300A.2 (U300-2)
NetU300_3: U300A.3 (U300-3)
NetU300_4: U300A.4 (U300-4)
NetU300_5: U300A.5 (U300-5)
NetU300_6: U300A.6 (U300-6)
PW_0: U177C.11 (U177-11)
PW_1: U162C.12 (U162-12), U177C.12 (U177-12)
PW_2: U162C.13 (U162-13)
Phi0: U206.9 (U206-9)
Phi0_X: U166A.3 (U166-3), U170.5 (U170-5), U173.5 (U173-5), U175.5 (U175-5)
Phi1_X: U112.5 (U112-5), U115.5 (U115-5), U171.5 (U171-5), U172.5 (U172-5), U174.5 (U174-5), U176.5 (U176-5)
RESA0: U106.14 (U106-14), U107.14 (U107-14), U108.14 (U108-14), U109.14 (U109-14), U110.14 (U110-14), U111.14 (U111-14), U113.14 (U113-14), U114.14 (U114-14)
RESA1: U106.13 (U106-13), U107.13 (U107-13), U108.13 (U108-13), U109.13 (U109-13), U110.13 (U110-13), U111.13 (U111-13), U113.13 (U113-13), U114.13 (U114-13)
RESA2: U106.7 (U106-7), U107.7 (U107-7), U108.7 (U108-7), U109.7 (U109-7), U110.7 (U110-7), U111.7 (U111-7), U113.7 (U113-7), U114.7 (U114-7)
RESA3: U106.4 (U106-4), U107.4 (U107-4), U108.4 (U108-4), U109.4 (U109-4), U110.4 (U110-4), U111.4 (U111-4), U113.4 (U113-4), U114.4 (U114-4)
STATE0: U103A.2 (U103-2)
STATE1: U103B.6 (U103-6)
STATE2: U103C.9 (U103-9)
STATE3: U103D.13 (U103-13), U104A.2 (U104-2)
STATE4: U167D.12 (U167-12)
STATE5: U104D.13 (U104-13)
STATE6: U86D.12 (U86-12)
TPARM_3: U20B.9 (U20-9)
VA_P0: U70D.11 (U70-11), U115.14 (U115-14), U206.3 (U206-3)
VA_P1: U70A.3 (U70-3), U115.13 (U115-13), U206.4 (U206-4)
VA_P2: U70B.4 (U70-4), U115.7 (U115-7), U206.6 (U206-6)
VA_P3: U70C.10 (U70-10), U115.4 (U115-4), U206.11 (U206-11)
VCC: U106.6 (U106-6), U106.16 (U106-16), U107.6 (U107-6), U107.16 (U107-16), U108.6 (U108-6), U108.16 (U108-16), U109.6 (U109-6), U109.16 (U109-16), U110.6 (U110-6), U110.16 (U110-16), U111.6 (U111-6), U111.16 (U111-16), U112.6 (U112-6), U112.16 (U112-16), U113.6 (U113-6), U113.16 (U113-16), U114.6 (U114-6), U114.16 (U114-16), U115.6 (U115-6), U115.16 (U115-16), U162A.8 (U162-8), U170.6 (U170-6), U170.16 (U170-16), U171.6 (U171-6), U171.16 (U171-16), U172.6 (U172-6), U172.16 (U172-16), U173.6 (U173-6), U173.16 (U173-16), U174.6 (U174-6), U174.16 (U174-16), U175.6 (U175-6), U175.16 (U175-16), U176.6 (U176-6), U176.16 (U176-16), U206.1 (U206-1), U206.16 (U206-16)
VDD: U20B.14 (U20-14), U29C.14 (U29-14), U34B.14 (U34-14), U70D.14 (U70-14), U72F.14 (U72-14), U79D.14 (U79-14), U85D.14 (U85-14), U86D.14 (U86-14), U97D.14 (U97-14), U100A.14 (U100-14), U102D.14 (U102-14), U103A.14 (U103-14), U104A.14 (U104-14), U105A.14 (U105-14), U149D.14 (U149-14), U162A.14 (U162-14), U166A.14 (U166-14), U167D.14 (U167-14), U168B.14 (U168-14), U177C.14 (U177-14), U178C.14 (U178-14), U179B.14 (U179-14), U183B.14 (U183-14), U205B.14 (U205-14), U208A.14 (U208-14), U300A.14 (U300-14)
VOICED: U97D.13 (U97-13)
VOICE_AMP0: U100A.5 (U100-5), U175.1 (U175-1)
VOICE_AMP1: U100A.4 (U100-4), U175.11 (U175-11)
VOICE_AMP2: U100A.3 (U100-3), U175.10 (U175-10)
VOICE_AMP3: U100A.2 (U100-2), U175.2 (U175-2)
VOICE_AMP_ZERO: U100A.1 (U100-1), U105A.1 (U105-1)
WR_SEL_2: U162C.11 (U162-11)
