hasseily/appletini-one/ps_sources/frontend/uthernet2_control.c

#include "uthernet2_control.h"

#include <stdio.h>
#include <string.h>

#include "card_control_regs.h"
#include "../lib/common.h"
#include "sleep.h"
#include "xiltimer.h"

#define W5100_REG_MR        0x0000U
#define W5100_REG_GAR       0x0001U
#define W5100_REG_SUBR      0x0005U
#define W5100_REG_SHAR      0x0009U
#define W5100_REG_SIPR      0x000FU
#define W5100S_REG_PHYSR    0x003CU
#define W5100S_REG_VERR     0x0080U

#define W5100_S0_SR_MACRAW       0x42U
#define W5100S_PHYSR_LINK        0x01U

#define DHCP_CLIENT_PORT  68U
#define DHCP_SERVER_PORT  67U
#define DHCP_PACKET_MAX   548U
#define DHCP_FRAME_MAX    600U
#define DHCP_MAGIC_COOKIE 0x63825363UL
#define DHCP_DISCOVER     1U
#define DHCP_OFFER        2U
#define DHCP_REQUEST      3U
#define DHCP_ACK          5U
#define DHCP_NAK          6U
#define DHCP_ATTEMPTS     3U

#define ETH_HEADER_LEN    14U
#define IPV4_HEADER_LEN   20U
#define UDP_HEADER_LEN    8U

#define UTHERNET2_CMD_TIMEOUT_POLLS 10000U
#define UTHERNET2_READY_POLL_USEC   20U
#define DHCP_POLL_USEC              10000U
#define DHCP_RESET_WAIT_USEC        10000U
#define DHCP_LINK_WAIT_USEC         5000000U
#define DHCP_REPLY_WAIT_USEC        2000000U

typedef struct {
    uint8_t message_type;
    uint8_t server_id[UTHERNET2_IPV4_LEN];
    uint8_t subnet[UTHERNET2_IPV4_LEN];
    uint8_t gateway[UTHERNET2_IPV4_LEN];
    uint8_t ip[UTHERNET2_IPV4_LEN];
    uint8_t has_server_id;
    uint8_t has_subnet;
    uint8_t has_gateway;
} dhcp_parse_t;

typedef enum {
    DHCP_ASYNC_IDLE = 0,
    DHCP_ASYNC_RESET_WAIT,
    DHCP_ASYNC_LINK_WAIT,
    DHCP_ASYNC_OFFER_WAIT,
    DHCP_ASYNC_ACK_WAIT
} dhcp_async_state_t;

typedef struct {
    dhcp_async_state_t state;
    uint8_t attempt;
    uint8_t received;
    uint32_t xid;
    XTime deadline;
    XTime next_poll;
    uint8_t mac[UTHERNET2_MAC_LEN];
    uthernet2_network_config_t previous;
    dhcp_parse_t offer;
    uint8_t packet[DHCP_PACKET_MAX];
    uint8_t frame[DHCP_FRAME_MAX];
} dhcp_async_t;

static dhcp_async_t g_dhcp;
static uint32_t g_dhcp_xid_seed = 0x41545001UL;

static void uthernet2_io_barrier(void)
{
    __asm__ volatile ("dsb sy" ::: "memory");
}

static void set_detail(char *detail, size_t detail_len, const char *text)
{
    if (detail != NULL && detail_len != 0U) {
        (void)snprintf(detail, detail_len, "%s", text != NULL ? text : "");
    }
}

void uthernet2_default_config(uthernet2_network_config_t *config)
{
    static const uthernet2_network_config_t defaults = {
        {0x02U, 0x41U, 0x50U, 0x50U, 0x4CU, 0x01U},
        {192U, 168U, 1U, 50U},
        {255U, 255U, 255U, 0U},
        {192U, 168U, 1U, 1U}
    };

    if (config != NULL) {
        *config = defaults;
    }
}

uint8_t uthernet2_mac_is_valid(const uint8_t mac[UTHERNET2_MAC_LEN])
{
    uint8_t nonzero = 0U;

    if (mac == NULL || (mac[0] & 0x01U) != 0U) {
        return 0U;
    }
    for (uint8_t i = 0U; i < UTHERNET2_MAC_LEN; ++i) {
        nonzero |= mac[i];
    }
    return nonzero != 0U;
}

static int uthernet2_command(uint16_t addr,
                             uint8_t write,
                             uint8_t wdata,
                             uint8_t *rdata)
{
    uint32_t status;
    uint8_t start_sequence;

    for (uint32_t poll = 0U; poll < UTHERNET2_CMD_TIMEOUT_POLLS; ++poll) {
        status = REG_READ(CARD_CTRL_ETH_STATUS_REG);
        if ((status & CARD_CTRL_ETH_STATUS_READY) != 0U &&
            (status & CARD_CTRL_ETH_STATUS_BUSY) == 0U) {
            start_sequence = (uint8_t)(
                (status >> CARD_CTRL_ETH_STATUS_SEQ_SHIFT) &
                CARD_CTRL_ETH_STATUS_SEQ_MASK);
            break;
        }
        if (poll == UTHERNET2_CMD_TIMEOUT_POLLS - 1U) {
            return -1;
        }
        usleep(UTHERNET2_READY_POLL_USEC);
    }

    REG_WRITE(CARD_CTRL_ETH_ADDR_REG, addr);
    if (write != 0U) {
        REG_WRITE(CARD_CTRL_ETH_DATA_REG, wdata);
    }
    uthernet2_io_barrier();
    REG_WRITE(CARD_CTRL_ETH_CMD_REG,
              CARD_CTRL_ETH_CMD_GO |
              (write != 0U ? CARD_CTRL_ETH_CMD_WRITE : 0U));
    uthernet2_io_barrier();

    for (uint32_t poll = 0U; poll < UTHERNET2_CMD_TIMEOUT_POLLS; ++poll) {
        uint8_t sequence;

        status = REG_READ(CARD_CTRL_ETH_STATUS_REG);
        sequence = (uint8_t)(
            (status >> CARD_CTRL_ETH_STATUS_SEQ_SHIFT) &
            CARD_CTRL_ETH_STATUS_SEQ_MASK);
        if (sequence != start_sequence &&
            (status & CARD_CTRL_ETH_STATUS_DONE) != 0U) {
            if ((status & CARD_CTRL_ETH_STATUS_ERROR) != 0U) {
                return -2;
            }
            if (rdata != NULL) {
                *rdata = (uint8_t)((status >> CARD_CTRL_ETH_STATUS_RDATA_SHIFT) &
                                   CARD_CTRL_ETH_STATUS_RDATA_MASK);
            }
            return 0;
        }
    }
    return -3;
}

int uthernet2_read_reg(uint16_t addr, uint8_t *value)
{
    return value != NULL ? uthernet2_command(addr, 0U, 0U, value) : -1;
}

int uthernet2_write_reg(uint16_t addr, uint8_t value)
{
    return uthernet2_command(addr, 1U, value, NULL);
}

static int w5100_read(uint16_t addr, uint8_t *dst, uint16_t len)
{
    if (dst == NULL) {
        return -1;
    }
    for (uint16_t i = 0U; i < len; ++i) {
        if (uthernet2_read_reg((uint16_t)(addr + i), &dst[i]) != 0) {
            return -1;
        }
    }
    return 0;
}

static int w5100_write(uint16_t addr, const uint8_t *src, uint16_t len)
{
    if (src == NULL) {
        return -1;
    }
    for (uint16_t i = 0U; i < len; ++i) {
        if (uthernet2_write_reg((uint16_t)(addr + i), src[i]) != 0) {
            return -1;
        }
    }
    return 0;
}

int uthernet2_read_block(uint16_t addr, uint8_t *dst, uint16_t len)
{
    return w5100_read(addr, dst, len);
}

int uthernet2_write_block(uint16_t addr, const uint8_t *src, uint16_t len)
{
    return w5100_write(addr, src, len);
}

static const uint16_t w5100_tx_base_4_2_1_1[4] = {
    0x4000U, 0x5000U, 0x5800U, 0x5C00U
};
static const uint16_t w5100_rx_base_4_2_1_1[4] = {
    0x6000U, 0x7000U, 0x7800U, 0x7C00U
};
static const uint16_t w5100_mask_4_2_1_1[4] = {
    0x0FFFU, 0x07FFU, 0x03FFU, 0x03FFU
};

uint16_t uthernet2_w5100_socket_reg(uint8_t socket, uint16_t offset)
{
    return socket < 4U ?
        (uint16_t)(0x0400U + ((uint16_t)socket * 0x0100U) + offset) : 0U;
}

int uthernet2_w5100_read16(uint16_t addr, uint16_t *value)
{
    uint8_t bytes[2];

    if (value == NULL || w5100_read(addr, bytes, sizeof(bytes)) != 0) {
        return -1;
    }
    *value = (uint16_t)(((uint16_t)bytes[0] << 8) | bytes[1]);
    return 0;
}

int uthernet2_w5100_read16_stable(uint16_t addr, uint16_t *value)
{
    uint16_t previous;
    uint16_t current;

    if (value == NULL || uthernet2_w5100_read16(addr, &previous) != 0) {
        return -1;
    }
    for (uint8_t i = 0U; i < 8U; ++i) {
        if (uthernet2_w5100_read16(addr, &current) != 0) {
            return -1;
        }
        if (current == previous) {
            *value = current;
            return 0;
        }
        previous = current;
    }
    return -1;
}

int uthernet2_w5100_write16(uint16_t addr, uint16_t value)
{
    const uint8_t bytes[2] = {
        (uint8_t)(value >> 8), (uint8_t)value
    };

    return w5100_write(addr, bytes, sizeof(bytes));
}

int uthernet2_w5100_socket_status(uint8_t socket, uint8_t *status)
{
    return socket < 4U && status != NULL ?
        uthernet2_read_reg(
            uthernet2_w5100_socket_reg(socket, W5100_SN_SR), status) : -1;
}

int uthernet2_read_network_config(uthernet2_network_config_t *config)
{
    if (config == NULL ||
        w5100_read(W5100_REG_SHAR, config->mac, sizeof(config->mac)) != 0 ||
        w5100_read(W5100_REG_SIPR, config->ip, sizeof(config->ip)) != 0 ||
        w5100_read(W5100_REG_SUBR, config->subnet, sizeof(config->subnet)) != 0 ||
        w5100_read(W5100_REG_GAR, config->gateway, sizeof(config->gateway)) != 0) {
        return -1;
    }
    return 0;
}

static int w5100_write_network_config(const uthernet2_network_config_t *config)
{
    if (w5100_write(W5100_REG_SHAR, config->mac, sizeof(config->mac)) != 0 ||
        w5100_write(W5100_REG_GAR, config->gateway, sizeof(config->gateway)) != 0 ||
        w5100_write(W5100_REG_SUBR, config->subnet, sizeof(config->subnet)) != 0 ||
        w5100_write(W5100_REG_SIPR, config->ip, sizeof(config->ip)) != 0) {
        return -1;
    }
    return 0;
}

int uthernet2_write_network_config(const uthernet2_network_config_t *config)
{
    return config != NULL && uthernet2_mac_is_valid(config->mac) != 0U ?
        w5100_write_network_config(config) : -1;
}

int uthernet2_test(uthernet2_test_result_t *result)
{
    if (result == NULL) {
        return -1;
    }
    memset(result, 0, sizeof(*result));
    if (uthernet2_read_reg(W5100S_REG_VERR, &result->version) != 0 ||
        uthernet2_read_reg(W5100S_REG_PHYSR, &result->physr) != 0 ||
        uthernet2_read_network_config(&result->config) != 0) {
        return -1;
    }
    result->link_up = (result->physr & W5100S_PHYSR_LINK) != 0U;
    return 0;
}

int uthernet2_w5100_socket_command(uint8_t socket, uint8_t command)
{
    uint8_t value;
    uint16_t command_reg;

    if (socket >= 4U) {
        return -1;
    }
    command_reg = uthernet2_w5100_socket_reg(socket, W5100_SN_CR);
    if (uthernet2_write_reg(command_reg, command) != 0) {
        return -1;
    }
    for (uint16_t poll = 0U; poll < 1000U; ++poll) {
        if (uthernet2_read_reg(command_reg, &value) != 0) {
            return -1;
        }
        if (value == 0U) {
            return 0;
        }
    }
    return -1;
}

static int w5100_close_sockets(void)
{
    int result = 0;

    for (uint8_t socket = 0U; socket < 4U; ++socket) {
        if (uthernet2_w5100_socket_command(socket, W5100_CR_CLOSE) != 0 ||
            uthernet2_write_reg(
                uthernet2_w5100_socket_reg(socket, W5100_SN_IR), 0xFFU) != 0) {
            result = -1;
        }
    }
    return result;
}

static int w5100_raw_open(const uint8_t mac[UTHERNET2_MAC_LEN])
{
    uint8_t state;

    if (w5100_close_sockets() != 0 ||
        uthernet2_write_reg(W5100_REG_RMSR, W5100_SOCKET_MEM_4_2_1_1) != 0 ||
        uthernet2_write_reg(W5100_REG_TMSR, W5100_SOCKET_MEM_4_2_1_1) != 0 ||
        w5100_write(W5100_REG_SHAR, mac, UTHERNET2_MAC_LEN) != 0 ||
        uthernet2_write_reg(
            uthernet2_w5100_socket_reg(0U, W5100_SN_MR),
            W5100_SN_MR_MACRAW_MF) != 0 ||
        uthernet2_w5100_socket_command(0U, W5100_CR_OPEN) != 0 ||
        uthernet2_w5100_socket_status(0U, &state) != 0 ||
        state != W5100_S0_SR_MACRAW) {
        return -1;
    }
    return 0;
}

int uthernet2_w5100_socket_ring_write(uint8_t socket,
                                      uint16_t pointer,
                                      const uint8_t *src,
                                      uint16_t len)
{
    const uint16_t base = socket < 4U ?
        w5100_tx_base_4_2_1_1[socket] : 0U;
    const uint16_t mask = socket < 4U ?
        w5100_mask_4_2_1_1[socket] : 0U;

    if (socket >= 4U || (src == NULL && len != 0U)) {
        return -1;
    }
    while (len != 0U) {
        const uint16_t offset = (uint16_t)(pointer & mask);
        uint16_t chunk = (uint16_t)((mask + 1U) - offset);

        if (chunk > len) {
            chunk = len;
        }
        if (w5100_write((uint16_t)(base + offset), src, chunk) != 0) {
            return -1;
        }
        pointer = (uint16_t)(pointer + chunk);
        src += chunk;
        len = (uint16_t)(len - chunk);
    }
    return 0;
}

int uthernet2_w5100_socket_ring_read(uint8_t socket,
                                     uint16_t pointer,
                                     uint8_t *dst,
                                     uint16_t len)
{
    const uint16_t base = socket < 4U ?
        w5100_rx_base_4_2_1_1[socket] : 0U;
    const uint16_t mask = socket < 4U ?
        w5100_mask_4_2_1_1[socket] : 0U;

    if (socket >= 4U || (dst == NULL && len != 0U)) {
        return -1;
    }
    while (len != 0U) {
        const uint16_t offset = (uint16_t)(pointer & mask);
        uint16_t chunk = (uint16_t)((mask + 1U) - offset);

        if (chunk > len) {
            chunk = len;
        }
        if (w5100_read((uint16_t)(base + offset), dst, chunk) != 0) {
            return -1;
        }
        pointer = (uint16_t)(pointer + chunk);
        dst += chunk;
        len = (uint16_t)(len - chunk);
    }
    return 0;
}

static int w5100_raw_send(const uint8_t *frame, uint16_t len)
{
    uint16_t free_size = 0U;
    uint16_t write_pointer;
    uint8_t interrupt;

    for (uint16_t poll = 0U; poll < 200U; ++poll) {
        if (uthernet2_w5100_read16_stable(
                uthernet2_w5100_socket_reg(0U, W5100_SN_TX_FSR),
                &free_size) != 0) {
            return -1;
        }
        if (free_size >= len) {
            break;
        }
        usleep(1000U);
    }
    if (free_size < len ||
        uthernet2_w5100_read16(
            uthernet2_w5100_socket_reg(0U, W5100_SN_TX_WR),
            &write_pointer) != 0 ||
        uthernet2_w5100_socket_ring_write(
            0U, write_pointer, frame, len) != 0 ||
        uthernet2_w5100_write16(
            uthernet2_w5100_socket_reg(0U, W5100_SN_TX_WR),
            (uint16_t)(write_pointer + len)) != 0 ||
        uthernet2_write_reg(
            uthernet2_w5100_socket_reg(0U, W5100_SN_IR),
                           W5100_IR_SENDOK | W5100_IR_TIMEOUT) != 0 ||
        uthernet2_w5100_socket_command(0U, W5100_CR_SEND) != 0) {
        return -1;
    }

    for (uint16_t poll = 0U; poll < 200U; ++poll) {
        if (uthernet2_read_reg(
                uthernet2_w5100_socket_reg(0U, W5100_SN_IR),
                &interrupt) != 0) {
            return -1;
        }
        if ((interrupt & W5100_IR_SENDOK) != 0U) {
            (void)uthernet2_write_reg(
                uthernet2_w5100_socket_reg(0U, W5100_SN_IR),
                W5100_IR_SENDOK);
            return 0;
        }
        if ((interrupt & W5100_IR_TIMEOUT) != 0U) {
            (void)uthernet2_write_reg(
                uthernet2_w5100_socket_reg(0U, W5100_SN_IR),
                W5100_IR_TIMEOUT);
            return -1;
        }
        usleep(1000U);
    }
    return -1;
}

static int w5100_raw_receive(uint8_t *frame,
                             uint16_t capacity,
                             uint16_t *frame_len)
{
    uint8_t length_header[2];
    uint16_t received_size;
    uint16_t read_pointer;
    uint16_t packet_size;
    uint16_t copy_len;

    *frame_len = 0U;
    if (uthernet2_w5100_read16_stable(
            uthernet2_w5100_socket_reg(0U, W5100_SN_RX_RSR),
            &received_size) != 0) {
        return -1;
    }
    if (received_size < 2U) {
        return 1;
    }
    if (uthernet2_w5100_read16(
            uthernet2_w5100_socket_reg(0U, W5100_SN_RX_RD),
            &read_pointer) != 0 ||
        uthernet2_w5100_socket_ring_read(
            0U, read_pointer, length_header, sizeof(length_header)) != 0) {
        return -1;
    }
    packet_size = (uint16_t)(((uint16_t)length_header[0] << 8) |
                             length_header[1]);
    if (packet_size < 2U || packet_size > received_size) {
        return 1;
    }
    copy_len = (uint16_t)(packet_size - 2U);
    if (copy_len > capacity) {
        copy_len = capacity;
    }
    if (uthernet2_w5100_socket_ring_read(
            0U, (uint16_t)(read_pointer + 2U), frame, copy_len) != 0 ||
        uthernet2_w5100_write16(
            uthernet2_w5100_socket_reg(0U, W5100_SN_RX_RD),
            (uint16_t)(read_pointer + packet_size)) != 0 ||
        uthernet2_w5100_socket_command(0U, W5100_CR_RECV) != 0) {
        return -1;
    }
    *frame_len = copy_len;
    return 0;
}

static uint16_t get_be16(const uint8_t *src)
{
    return (uint16_t)(((uint16_t)src[0] << 8) | src[1]);
}

static void put_be16(uint8_t *dst, uint16_t value)
{
    dst[0] = (uint8_t)(value >> 8);
    dst[1] = (uint8_t)value;
}

static void put_be32(uint8_t *dst, uint32_t value)
{
    dst[0] = (uint8_t)(value >> 24);
    dst[1] = (uint8_t)(value >> 16);
    dst[2] = (uint8_t)(value >> 8);
    dst[3] = (uint8_t)value;
}

static uint16_t checksum(const uint8_t *data, uint16_t len)
{
    uint32_t sum = 0U;

    while (len >= 2U) {
        sum += get_be16(data);
        data += 2;
        len = (uint16_t)(len - 2U);
    }
    if (len != 0U) {
        sum += (uint16_t)data[0] << 8;
    }
    while ((sum >> 16) != 0U) {
        sum = (sum & 0xFFFFU) + (sum >> 16);
    }
    return (uint16_t)~sum;
}

static uint16_t dhcp_build_packet(uint8_t *packet,
                                  uint8_t message_type,
                                  uint32_t xid,
                                  const uint8_t mac[UTHERNET2_MAC_LEN],
                                  const uint8_t *requested_ip,
                                  const uint8_t *server_id)
{
    uint16_t pos = 240U;

    memset(packet, 0, DHCP_PACKET_MAX);
    packet[0] = 1U;
    packet[1] = 1U;
    packet[2] = UTHERNET2_MAC_LEN;
    put_be32(&packet[4], xid);
    put_be16(&packet[10], 0x8000U);
    memcpy(&packet[28], mac, UTHERNET2_MAC_LEN);
    put_be32(&packet[236], DHCP_MAGIC_COOKIE);

#define DHCP_OPTION(code, len) do { packet[pos++] = (code); packet[pos++] = (len); } while (0)
    DHCP_OPTION(53U, 1U);
    packet[pos++] = message_type;
    if (message_type == DHCP_REQUEST) {
        DHCP_OPTION(54U, 4U);
        memcpy(&packet[pos], server_id, UTHERNET2_IPV4_LEN);
        pos = (uint16_t)(pos + UTHERNET2_IPV4_LEN);
        DHCP_OPTION(50U, 4U);
        memcpy(&packet[pos], requested_ip, UTHERNET2_IPV4_LEN);
        pos = (uint16_t)(pos + UTHERNET2_IPV4_LEN);
    } else {
        DHCP_OPTION(55U, 3U);
        packet[pos++] = 1U;
        packet[pos++] = 3U;
        packet[pos++] = 6U;
    }
    packet[pos++] = 255U;
#undef DHCP_OPTION
    return pos;
}

static uint8_t dhcp_parse_packet(const uint8_t *packet,
                                 uint16_t len,
                                 uint32_t xid,
                                 const uint8_t mac[UTHERNET2_MAC_LEN],
                                 dhcp_parse_t *out)
{
    uint8_t xid_bytes[4];
    uint16_t pos = 240U;

    put_be32(xid_bytes, xid);
    if (len < 241U || packet[0] != 2U || packet[1] != 1U ||
        packet[2] != UTHERNET2_MAC_LEN ||
        memcmp(&packet[4], xid_bytes, sizeof(xid_bytes)) != 0 ||
        memcmp(&packet[28], mac, UTHERNET2_MAC_LEN) != 0 ||
        memcmp(&packet[236], "\x63\x82\x53\x63", 4U) != 0) {
        return 0U;
    }

    memset(out, 0, sizeof(*out));
    memcpy(out->ip, &packet[16], UTHERNET2_IPV4_LEN);
    while (pos < len) {
        const uint8_t code = packet[pos++];
        uint8_t option_len;

        if (code == 255U) {
            break;
        }
        if (code == 0U) {
            continue;
        }
        if (pos >= len) {
            return 0U;
        }
        option_len = packet[pos++];
        if ((uint16_t)(pos + option_len) > len) {
            return 0U;
        }
        if (code == 53U && option_len >= 1U) {
            out->message_type = packet[pos];
        } else if (code == 54U && option_len >= 4U) {
            memcpy(out->server_id, &packet[pos], 4U);
            out->has_server_id = 1U;
        } else if (code == 1U && option_len >= 4U) {
            memcpy(out->subnet, &packet[pos], 4U);
            out->has_subnet = 1U;
        } else if (code == 3U && option_len >= 4U) {
            memcpy(out->gateway, &packet[pos], 4U);
            out->has_gateway = 1U;
        }
        pos = (uint16_t)(pos + option_len);
    }
    return out->message_type != 0U;
}

static uint16_t dhcp_build_frame(uint8_t *frame,
                                 const uint8_t mac[UTHERNET2_MAC_LEN],
                                 const uint8_t *payload,
                                 uint16_t payload_len,
                                 uint32_t xid)
{
    uint8_t *ip = &frame[ETH_HEADER_LEN];
    uint8_t *udp = &ip[IPV4_HEADER_LEN];
    const uint16_t ip_len = (uint16_t)(IPV4_HEADER_LEN + UDP_HEADER_LEN +
                                       payload_len);

    memset(frame, 0, DHCP_FRAME_MAX);
    memset(frame, 0xFF, 6U);
    memcpy(&frame[6], mac, UTHERNET2_MAC_LEN);
    put_be16(&frame[12], 0x0800U);

    ip[0] = 0x45U;
    put_be16(&ip[2], ip_len);
    put_be16(&ip[4], (uint16_t)xid);
    ip[8] = 64U;
    ip[9] = 17U;
    memset(&ip[16], 0xFF, UTHERNET2_IPV4_LEN);
    put_be16(&ip[10], checksum(ip, IPV4_HEADER_LEN));

    put_be16(&udp[0], DHCP_CLIENT_PORT);
    put_be16(&udp[2], DHCP_SERVER_PORT);
    put_be16(&udp[4], (uint16_t)(UDP_HEADER_LEN + payload_len));
    memcpy(&udp[UDP_HEADER_LEN], payload, payload_len);
    return (uint16_t)(ETH_HEADER_LEN + ip_len);
}

static uint8_t dhcp_frame_payload(const uint8_t *frame,
                                  uint16_t frame_len,
                                  const uint8_t **payload,
                                  uint16_t *payload_len)
{
    const uint8_t *ip;
    const uint8_t *udp;
    uint16_t ip_header_len;
    uint16_t ip_len;
    uint16_t udp_len;

    if (frame_len < ETH_HEADER_LEN + IPV4_HEADER_LEN + UDP_HEADER_LEN ||
        get_be16(&frame[12]) != 0x0800U) {
        return 0U;
    }
    ip = &frame[ETH_HEADER_LEN];
    ip_header_len = (uint16_t)(ip[0] & 0x0FU) * 4U;
    ip_len = get_be16(&ip[2]);
    if ((ip[0] >> 4) != 4U || ip_header_len < IPV4_HEADER_LEN ||
        ip[9] != 17U || (get_be16(&ip[6]) & 0x1FFFU) != 0U ||
        ip_len < ip_header_len + UDP_HEADER_LEN ||
        ETH_HEADER_LEN + ip_len > frame_len) {
        return 0U;
    }
    udp = &ip[ip_header_len];
    udp_len = get_be16(&udp[4]);
    if (get_be16(&udp[0]) != DHCP_SERVER_PORT ||
        get_be16(&udp[2]) != DHCP_CLIENT_PORT ||
        udp_len < UDP_HEADER_LEN || udp_len > ip_len - ip_header_len) {
        return 0U;
    }
    *payload = &udp[UDP_HEADER_LEN];
    *payload_len = (uint16_t)(udp_len - UDP_HEADER_LEN);
    return 1U;
}

static XTime dhcp_now(void)
{
    XTime now = 0U;

    XTime_GetTime(&now);
    return now;
}

static XTime dhcp_ticks_from_usec(uint32_t usec)
{
    return (XTime)(((uint64_t)usec * (uint64_t)COUNTS_PER_SECOND) / 1000000ULL);
}

static uint8_t dhcp_time_reached(XTime now, XTime deadline)
{
    return ((int64_t)(now - deadline) >= 0) ? 1U : 0U;
}

static int dhcp_async_fail(char *detail,
                           size_t detail_len,
                           const char *message)
{
    if (g_dhcp.state != DHCP_ASYNC_IDLE) {
        (void)w5100_close_sockets();
    }
    (void)w5100_write_network_config(&g_dhcp.previous);
    g_dhcp.state = DHCP_ASYNC_IDLE;
    set_detail(detail, detail_len, message);
    return -1;
}

static int dhcp_async_send(uint8_t message_type,
                           XTime now,
                           char *detail,
                           size_t detail_len)
{
    const uint8_t *requested_ip = NULL;
    const uint8_t *server_id = NULL;
    uint16_t packet_len;
    uint16_t frame_len;

    if (message_type == DHCP_REQUEST) {
        requested_ip = g_dhcp.offer.ip;
        server_id = g_dhcp.offer.server_id;
    }
    packet_len = dhcp_build_packet(g_dhcp.packet,
                                   message_type,
                                   g_dhcp.xid,
                                   g_dhcp.mac,
                                   requested_ip,
                                   server_id);
    frame_len = dhcp_build_frame(g_dhcp.frame,
                                 g_dhcp.mac,
                                 g_dhcp.packet,
                                 packet_len,
                                 g_dhcp.xid);
    if (w5100_raw_send(g_dhcp.frame, frame_len) != 0) {
        return dhcp_async_fail(detail,
                               detail_len,
                               message_type == DHCP_DISCOVER ?
                                   "DHCP DISCOVER FAILED" :
                                   "DHCP REQUEST FAILED");
    }
    g_dhcp.attempt++;
    g_dhcp.received = 0U;
    g_dhcp.deadline = now + dhcp_ticks_from_usec(DHCP_REPLY_WAIT_USEC);
    g_dhcp.next_poll = now;
    return 0;
}

static int dhcp_async_receive(uint8_t wanted_type, dhcp_parse_t *reply)
{
    const uint8_t *payload;
    uint16_t frame_len;
    uint16_t payload_len;
    const int receive = w5100_raw_receive(g_dhcp.frame,
                                           DHCP_FRAME_MAX,
                                           &frame_len);

    if (receive != 0) {
        return receive;
    }
    g_dhcp.received = 1U;
    if (dhcp_frame_payload(g_dhcp.frame,
                           frame_len,
                           &payload,
                           &payload_len) == 0U ||
        dhcp_parse_packet(payload,
                          payload_len,
                          g_dhcp.xid,
                          g_dhcp.mac,
                          reply) == 0U) {
        return 2;
    }
    return (reply->message_type == wanted_type ||
            reply->message_type == DHCP_NAK) ? 0 : 2;
}

static int dhcp_async_complete(const dhcp_parse_t *ack,
                               uthernet2_network_config_t *lease,
                               char *detail,
                               size_t detail_len)
{
    uthernet2_network_config_t acquired;

    memcpy(acquired.mac, g_dhcp.mac, sizeof(acquired.mac));
    memcpy(acquired.ip, ack->ip, sizeof(acquired.ip));
    if (ack->has_subnet != 0U) {
        memcpy(acquired.subnet, ack->subnet, sizeof(acquired.subnet));
    } else if (g_dhcp.offer.has_subnet != 0U) {
        memcpy(acquired.subnet,
               g_dhcp.offer.subnet,
               sizeof(acquired.subnet));
    } else {
        memset(acquired.subnet, 0, sizeof(acquired.subnet));
    }
    if (ack->has_gateway != 0U) {
        memcpy(acquired.gateway, ack->gateway, sizeof(acquired.gateway));
    } else if (g_dhcp.offer.has_gateway != 0U) {
        memcpy(acquired.gateway,
               g_dhcp.offer.gateway,
               sizeof(acquired.gateway));
    } else {
        memset(acquired.gateway, 0, sizeof(acquired.gateway));
    }

    (void)w5100_close_sockets();
    if (uthernet2_write_network_config(&acquired) != 0) {
        return dhcp_async_fail(detail,
                               detail_len,
                               "DHCP LEASE WRITE FAILED");
    }
    g_dhcp.state = DHCP_ASYNC_IDLE;
    if (lease != NULL) {
        *lease = acquired;
    }
    set_detail(detail, detail_len, "DHCP LEASE ACQUIRED");
    return 1;
}

int uthernet2_dhcp_start(const uint8_t mac[UTHERNET2_MAC_LEN],
                         char *detail,
                         size_t detail_len)
{
    uthernet2_network_config_t previous;
    XTime now;

    if (uthernet2_mac_is_valid(mac) == 0U) {
        set_detail(detail, detail_len, "DHCP INVALID SOURCE MAC");
        return -1;
    }
    if (g_dhcp.state != DHCP_ASYNC_IDLE) {
        uthernet2_dhcp_cancel();
    }
    if (uthernet2_read_network_config(&previous) != 0) {
        set_detail(detail, detail_len, "DHCP CONFIG SAVE FAILED");
        return -1;
    }

    memset(&g_dhcp, 0, sizeof(g_dhcp));
    g_dhcp.previous = previous;
    memcpy(g_dhcp.mac, mac, sizeof(g_dhcp.mac));
    if (uthernet2_write_reg(W5100_REG_MR, 0x80U) != 0) {
        return dhcp_async_fail(detail, detail_len, "DHCP RESET FAILED");
    }

    now = dhcp_now();
    g_dhcp.state = DHCP_ASYNC_RESET_WAIT;
    g_dhcp.deadline = now + dhcp_ticks_from_usec(DHCP_RESET_WAIT_USEC);
    set_detail(detail, detail_len, "DHCP REQUEST IN PROGRESS");
    return 0;
}

int uthernet2_dhcp_poll(uthernet2_network_config_t *lease,
                        char *detail,
                        size_t detail_len)
{
    XTime now;

    if (g_dhcp.state == DHCP_ASYNC_IDLE) {
        set_detail(detail, detail_len, "DHCP NOT ACTIVE");
        return -1;
    }
    now = dhcp_now();

    if (g_dhcp.state == DHCP_ASYNC_RESET_WAIT) {
        if (dhcp_time_reached(now, g_dhcp.deadline) == 0U) {
            return 0;
        }
        g_dhcp.state = DHCP_ASYNC_LINK_WAIT;
        g_dhcp.next_poll = now;
        g_dhcp.deadline = now + dhcp_ticks_from_usec(DHCP_LINK_WAIT_USEC);
    }

    if (g_dhcp.state == DHCP_ASYNC_LINK_WAIT) {
        uint8_t physr;

        if (dhcp_time_reached(now, g_dhcp.next_poll) == 0U) {
            return 0;
        }
        g_dhcp.next_poll = now + dhcp_ticks_from_usec(DHCP_POLL_USEC);
        if (uthernet2_read_reg(W5100S_REG_PHYSR, &physr) != 0) {
            return dhcp_async_fail(detail, detail_len, "DHCP LINK READ FAILED");
        }
        if ((physr & W5100S_PHYSR_LINK) == 0U) {
            return dhcp_time_reached(now, g_dhcp.deadline) != 0U ?
                dhcp_async_fail(detail, detail_len, "DHCP LINK DOWN") : 0;
        }
        if (w5100_raw_open(g_dhcp.mac) != 0) {
            return dhcp_async_fail(detail,
                                   detail_len,
                                   "DHCP MACRAW OPEN FAILED");
        }
        g_dhcp_xid_seed += 0x01010101UL;
        g_dhcp.xid = g_dhcp_xid_seed;
        memset(&g_dhcp.offer, 0, sizeof(g_dhcp.offer));
        g_dhcp.attempt = 0U;
        g_dhcp.state = DHCP_ASYNC_OFFER_WAIT;
        return dhcp_async_send(DHCP_DISCOVER, now, detail, detail_len);
    }

    if (dhcp_time_reached(now, g_dhcp.next_poll) == 0U) {
        return 0;
    }
    g_dhcp.next_poll = now + dhcp_ticks_from_usec(DHCP_POLL_USEC);

    if (g_dhcp.state == DHCP_ASYNC_OFFER_WAIT) {
        dhcp_parse_t offer;
        const int receive = dhcp_async_receive(DHCP_OFFER, &offer);

        if (receive < 0) {
            return dhcp_async_fail(detail,
                                   detail_len,
                                   "DHCP OFFER RECEIVE FAILED");
        }
        if (receive == 0) {
            if (offer.message_type == DHCP_NAK) {
                return dhcp_async_fail(detail, detail_len, "DHCP NAK");
            }
            if (offer.message_type == DHCP_OFFER &&
                offer.has_server_id != 0U) {
                g_dhcp.offer = offer;
                g_dhcp.attempt = 0U;
                g_dhcp.state = DHCP_ASYNC_ACK_WAIT;
                return dhcp_async_send(DHCP_REQUEST,
                                       now,
                                       detail,
                                       detail_len);
            }
        }
        if (dhcp_time_reached(now, g_dhcp.deadline) != 0U) {
            if (g_dhcp.attempt < DHCP_ATTEMPTS) {
                return dhcp_async_send(DHCP_DISCOVER,
                                       now,
                                       detail,
                                       detail_len);
            }
            return dhcp_async_fail(detail,
                                   detail_len,
                                   g_dhcp.received == 0U ?
                                       "DHCP OFFER NO RX" :
                                       "DHCP OFFER INVALID RX");
        }
        return 0;
    }

    if (g_dhcp.state == DHCP_ASYNC_ACK_WAIT) {
        dhcp_parse_t ack;
        const int receive = dhcp_async_receive(DHCP_ACK, &ack);

        if (receive < 0) {
            return dhcp_async_fail(detail,
                                   detail_len,
                                   "DHCP ACK RECEIVE FAILED");
        }
        if (receive == 0) {
            if (ack.message_type == DHCP_NAK) {
                return dhcp_async_fail(detail, detail_len, "DHCP NAK");
            }
            if (ack.message_type == DHCP_ACK) {
                return dhcp_async_complete(&ack, lease, detail, detail_len);
            }
        }
        if (dhcp_time_reached(now, g_dhcp.deadline) != 0U) {
            if (g_dhcp.attempt < DHCP_ATTEMPTS) {
                return dhcp_async_send(DHCP_REQUEST,
                                       now,
                                       detail,
                                       detail_len);
            }
            return dhcp_async_fail(detail,
                                   detail_len,
                                   g_dhcp.received == 0U ?
                                       "DHCP ACK NO RX" :
                                       "DHCP ACK INVALID RX");
        }
        return 0;
    }

    return dhcp_async_fail(detail, detail_len, "DHCP INVALID STATE");
}

void uthernet2_dhcp_cancel(void)
{
    if (g_dhcp.state != DHCP_ASYNC_IDLE) {
        (void)w5100_close_sockets();
        (void)w5100_write_network_config(&g_dhcp.previous);
        g_dhcp.state = DHCP_ASYNC_IDLE;
    }
}

int uthernet2_dhcp_acquire(const uint8_t mac[UTHERNET2_MAC_LEN],
                           uthernet2_network_config_t *lease,
                           char *detail,
                           size_t detail_len)
{
    int result;

    if (lease == NULL) {
        set_detail(detail, detail_len, "INVALID DHCP ARGUMENT");
        return -1;
    }
    if (uthernet2_dhcp_start(mac, detail, detail_len) != 0) {
        return -1;
    }
    do {
        result = uthernet2_dhcp_poll(lease, detail, detail_len);
        if (result == 0) {
            usleep(1000U);
        }
    } while (result == 0);
    return result > 0 ? 0 : -1;
}
